AlistairCheeseman/SmartHome-Project/Hardware/Device Pictures/DSC_0228.JPG

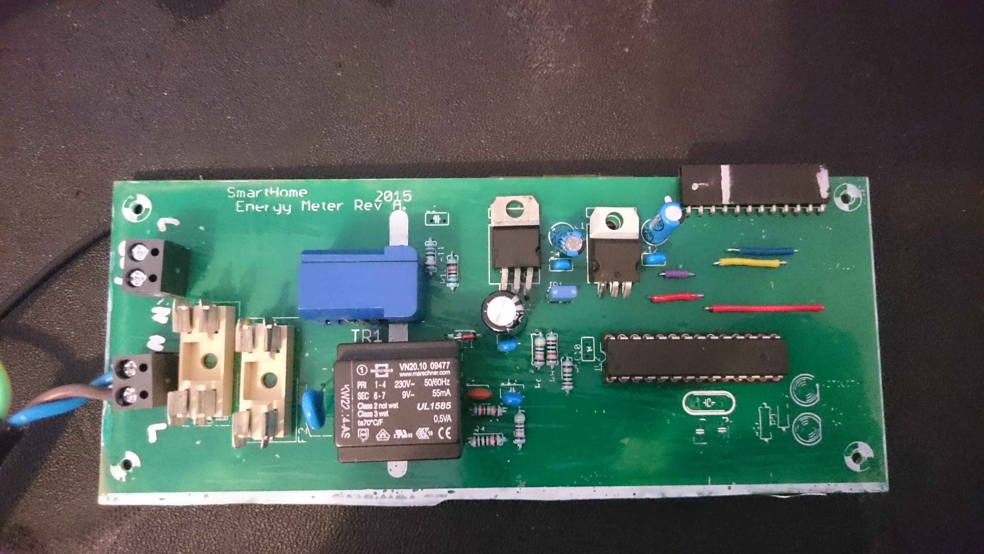
Hardware/Device Pictures/DSC_0228.JPG
