AlistairCheeseman/SmartHome-Project/Hardware/Device Pictures/DSCF8857.JPG

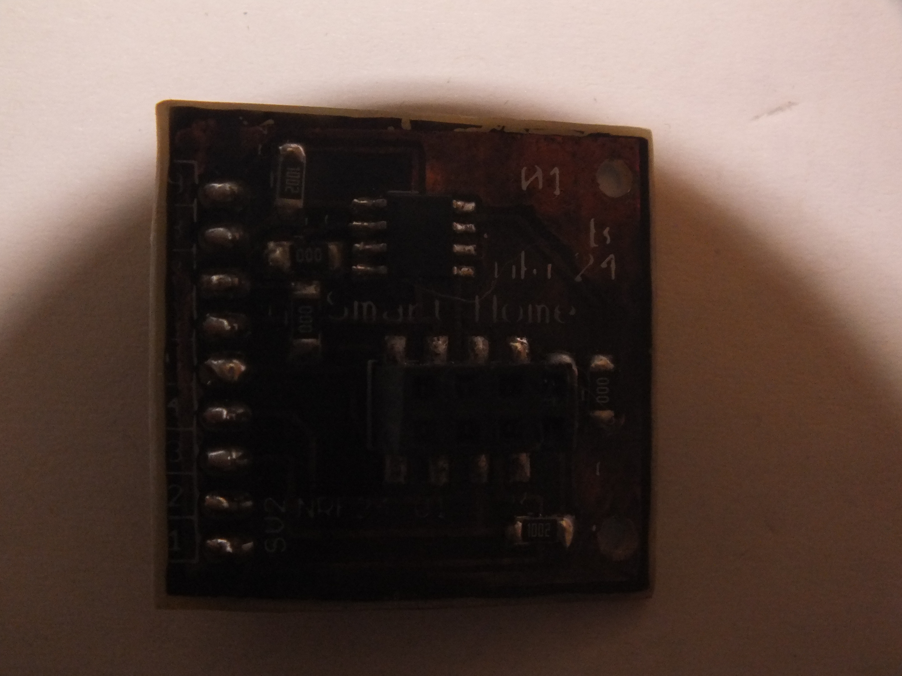
Hardware/Device Pictures/DSCF8857.JPG
