AlistairCheeseman/SmartHome-Project/Hardware/Device Pictures/DSCF8858.JPG

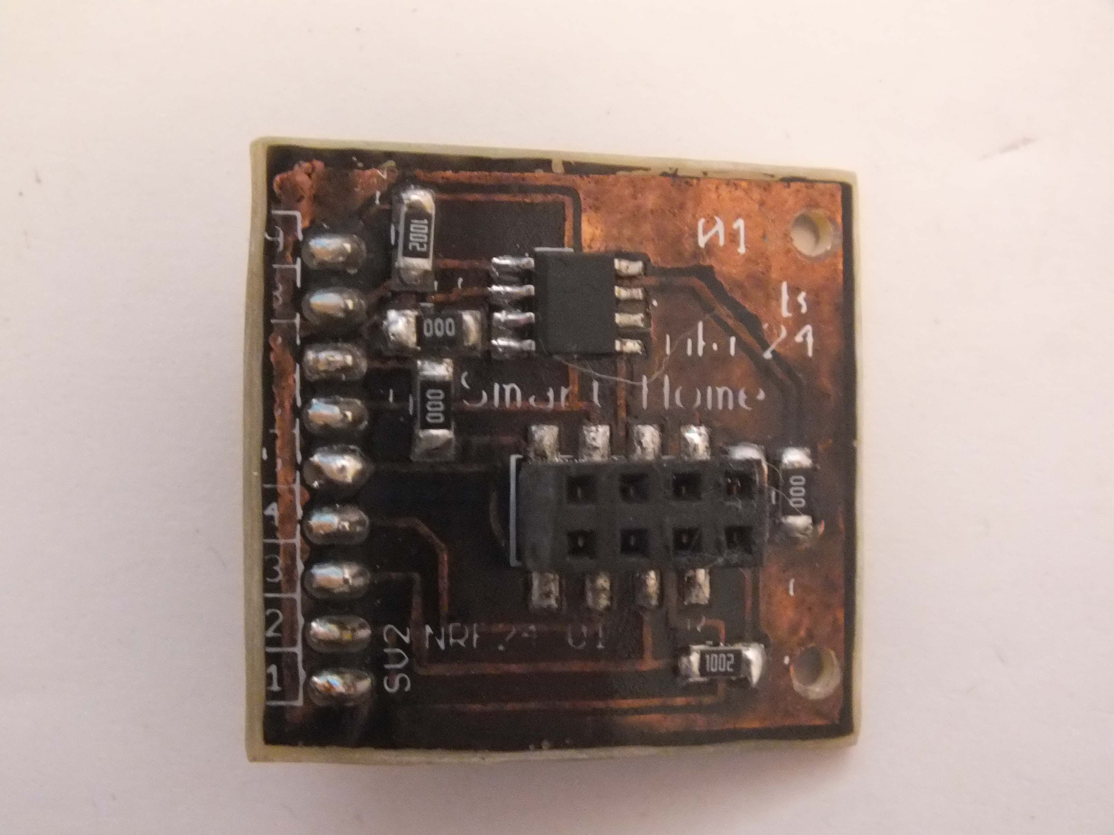
Hardware/Device Pictures/DSCF8858.JPG
