AlistairCheeseman/SmartHome-Project/Hardware/Device Pictures/DSCF8859.JPG

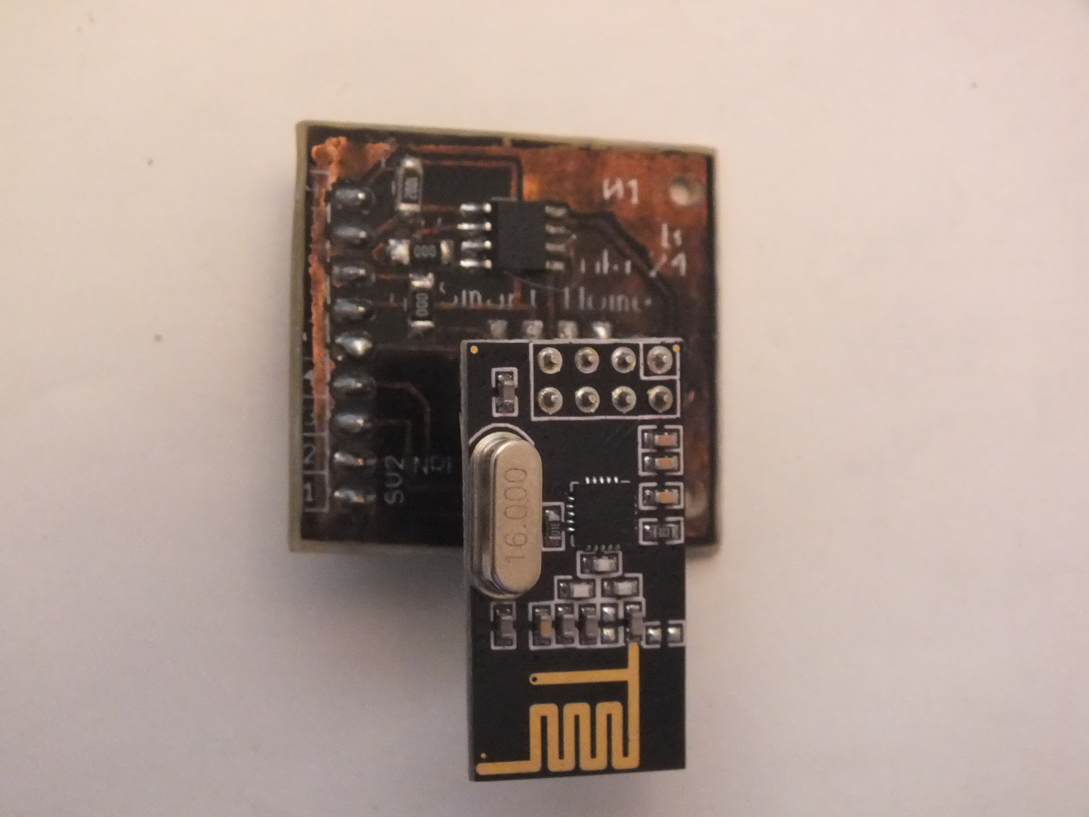
Hardware/Device Pictures/DSCF8859.JPG
