AlistairCheeseman/SmartHome-Project/Hardware/Device Pictures/DSCF8860.JPG

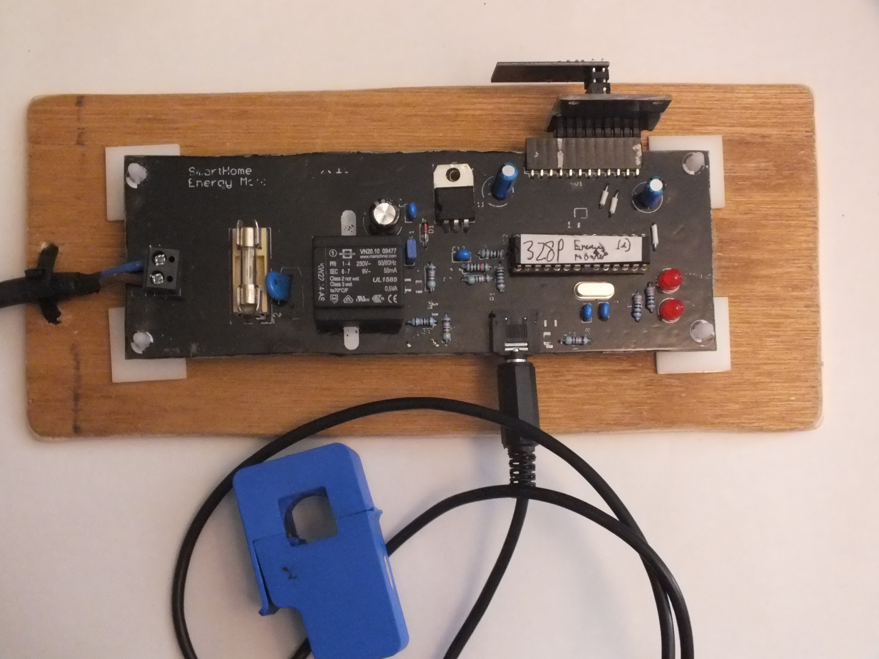
Hardware/Device Pictures/DSCF8860.JPG
