AlistairCheeseman/SmartHome-Project/Hardware/Device Pictures/DSCF8861.JPG

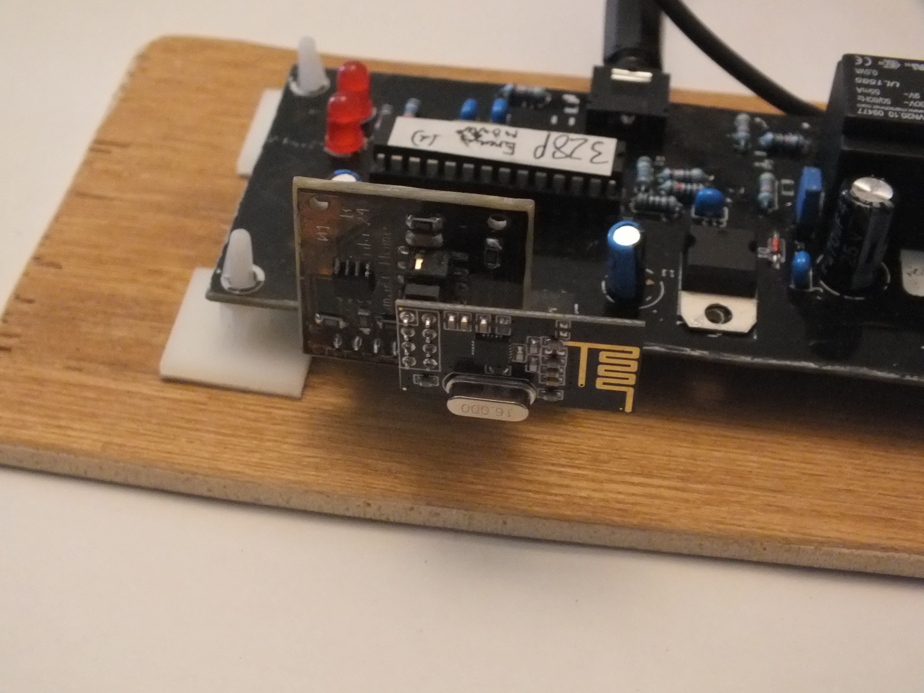
Hardware/Device Pictures/DSCF8861.JPG
