AlistairCheeseman/SmartHome-Project/Hardware/Device Pictures/DSCF8862.JPG

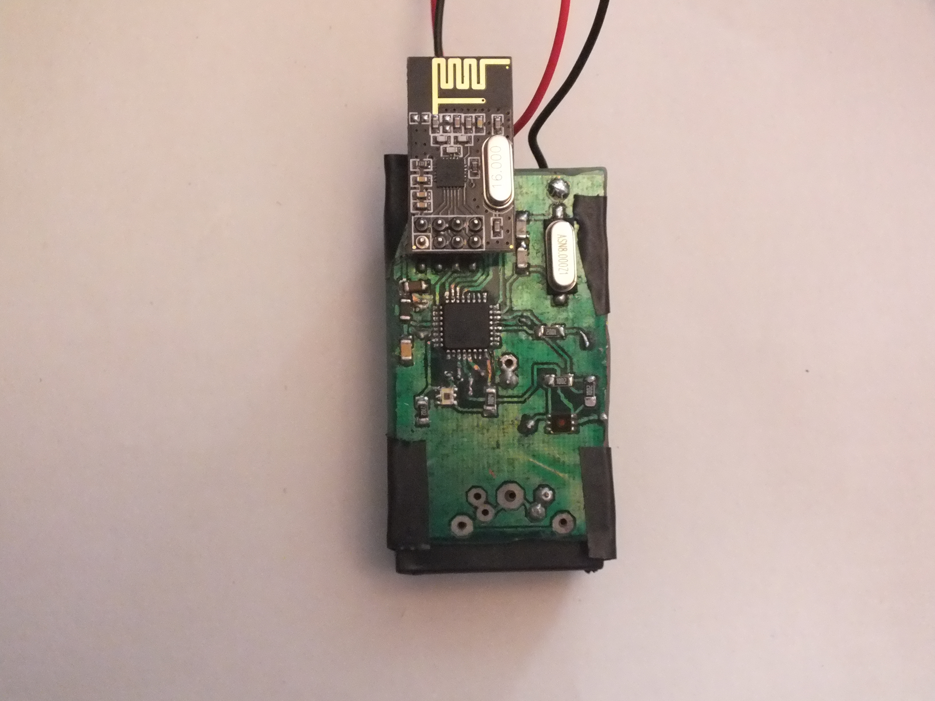
Hardware/Device Pictures/DSCF8862.JPG
