AlistairCheeseman/SmartHome-Project/Hardware/Device Pictures/DSCF8863.JPG

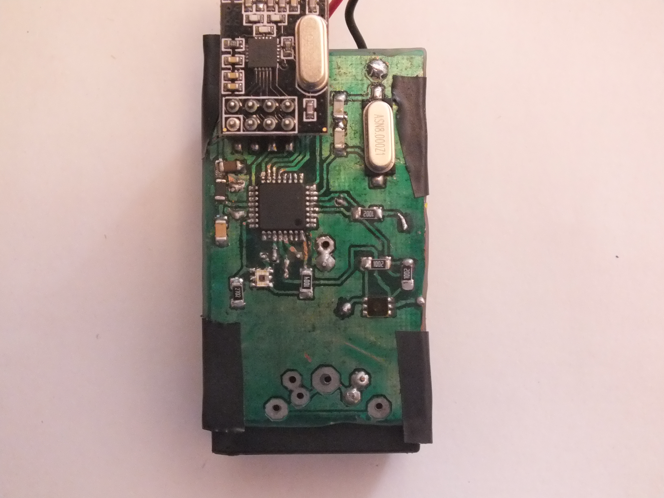
Hardware/Device Pictures/DSCF8863.JPG
