AlistairCheeseman/SmartHome-Project/Hardware/Device Pictures/DSCF8865.JPG

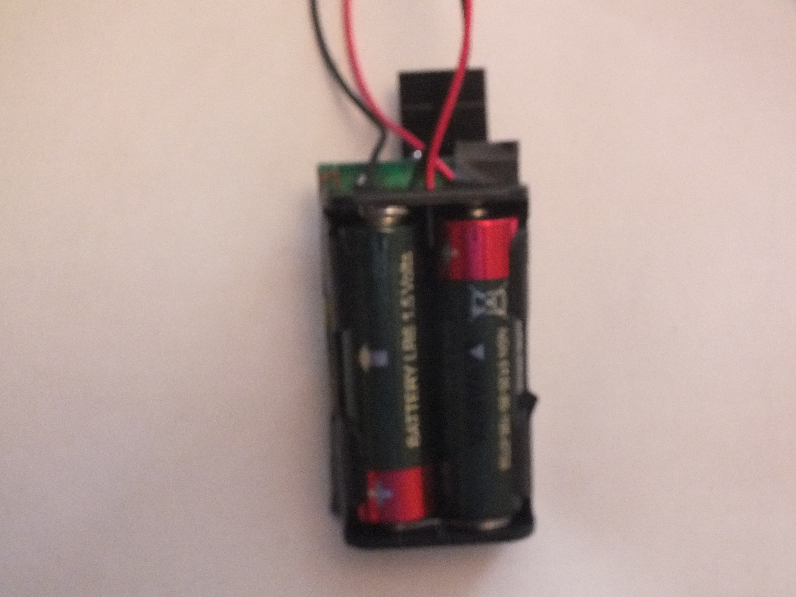
Hardware/Device Pictures/DSCF8865.JPG
