AlistairCheeseman/SmartHome-Project/Hardware/Device Pictures/DSCF8866.JPG

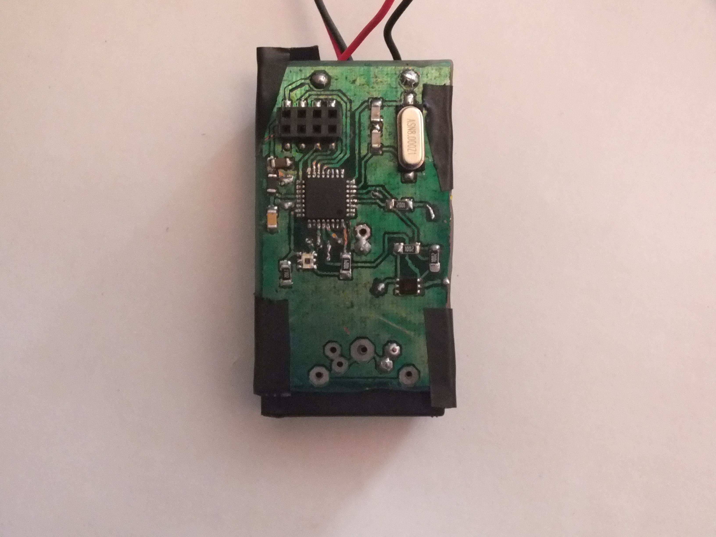
Hardware/Device Pictures/DSCF8866.JPG
