AlistairCheeseman/SmartHome-Project/Hardware/Device Pictures/DSCF8867.JPG

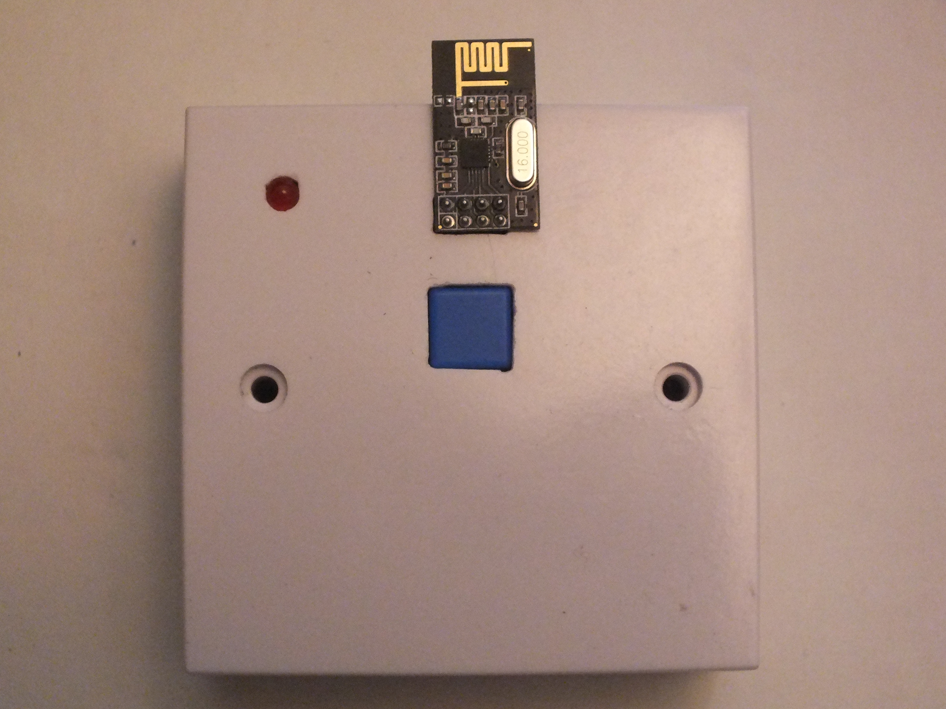
Hardware/Device Pictures/DSCF8867.JPG
