AlistairCheeseman/SmartHome-Project/Hardware/Device Pictures/DSCF8868.JPG

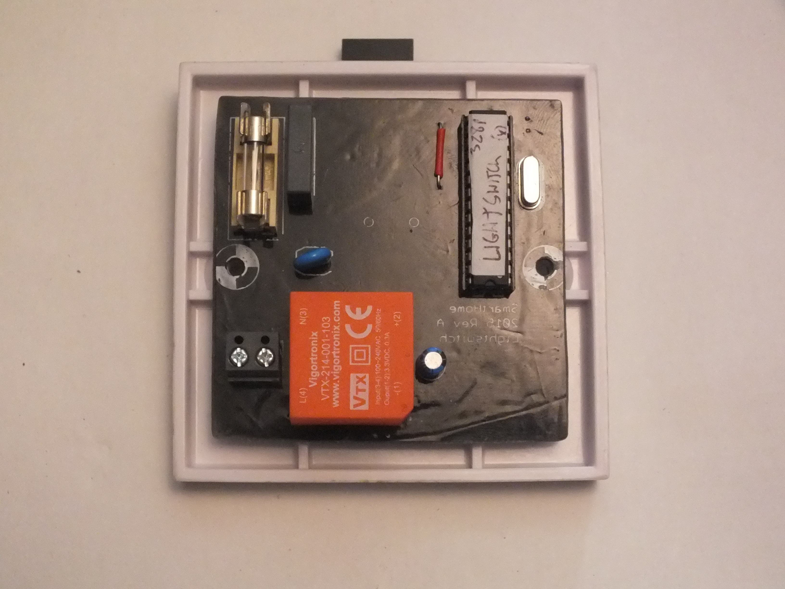
Hardware/Device Pictures/DSCF8868.JPG
