AlistairCheeseman/SmartHome-Project/Hardware/Device Pictures/DSCF8869.JPG

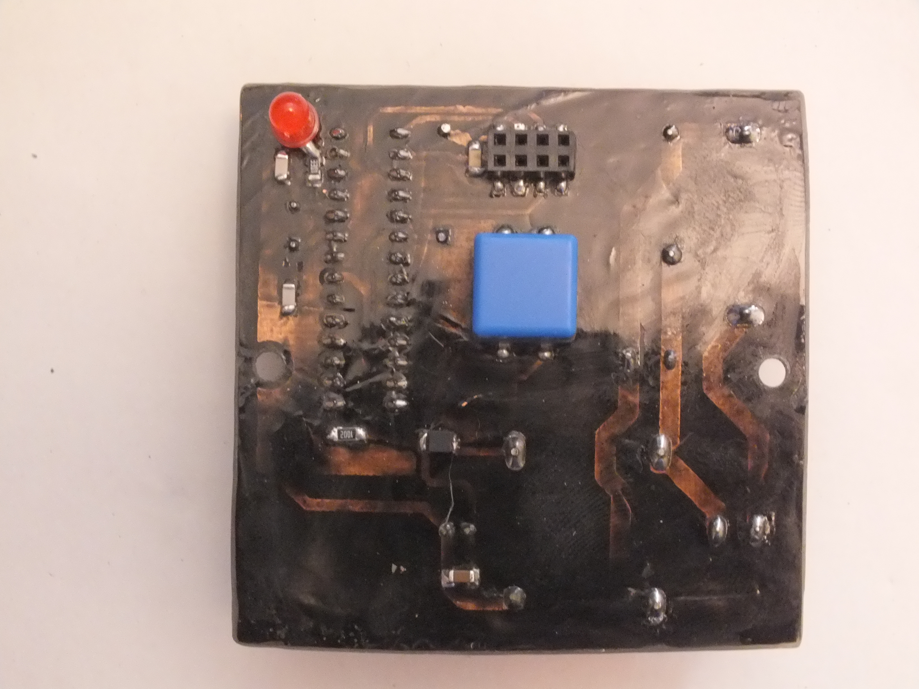
Hardware/Device Pictures/DSCF8869.JPG
