AlistairCheeseman/SmartHome-Project/Hardware/Device Pictures/DSCF8870.JPG

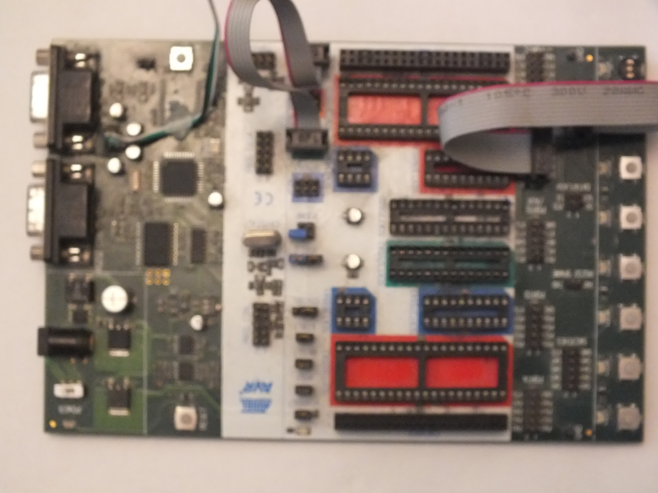
Hardware/Device Pictures/DSCF8870.JPG
