AlistairCheeseman/SmartHome-Project/Hardware/Device Pictures/DSCF8872.JPG

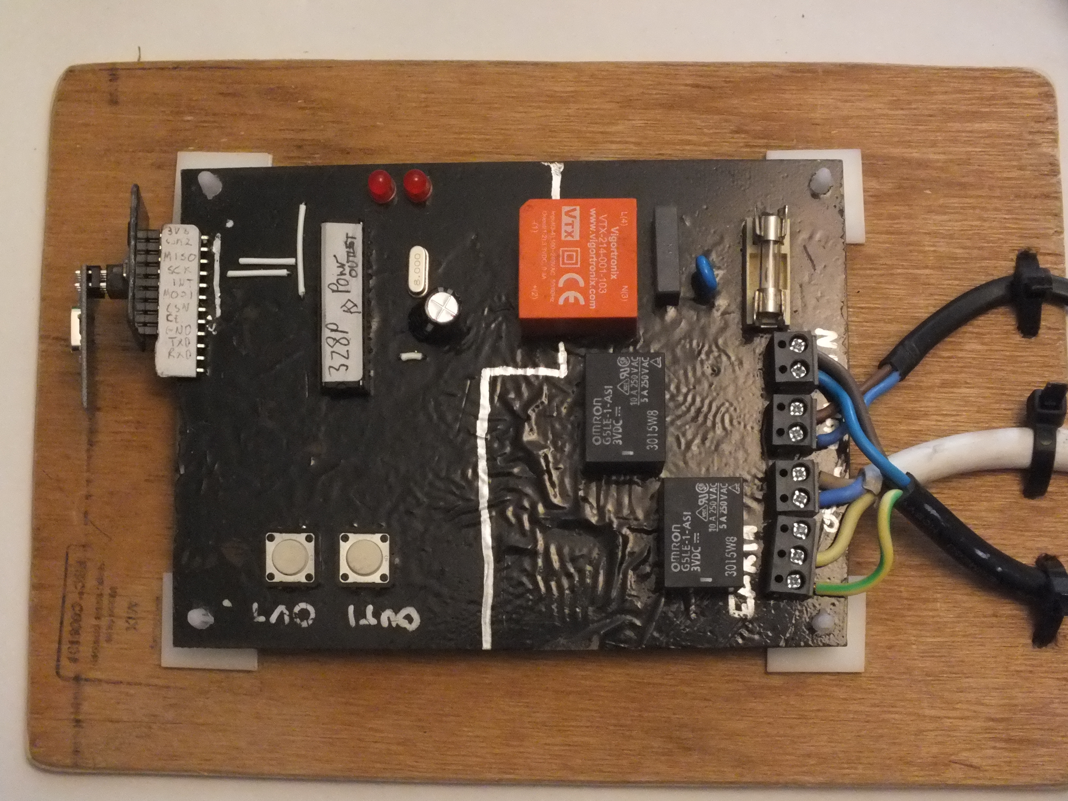
Hardware/Device Pictures/DSCF8872.JPG
