AlistairCheeseman/SmartHome-Project/Hardware/Device Pictures/DSCF8873.JPG

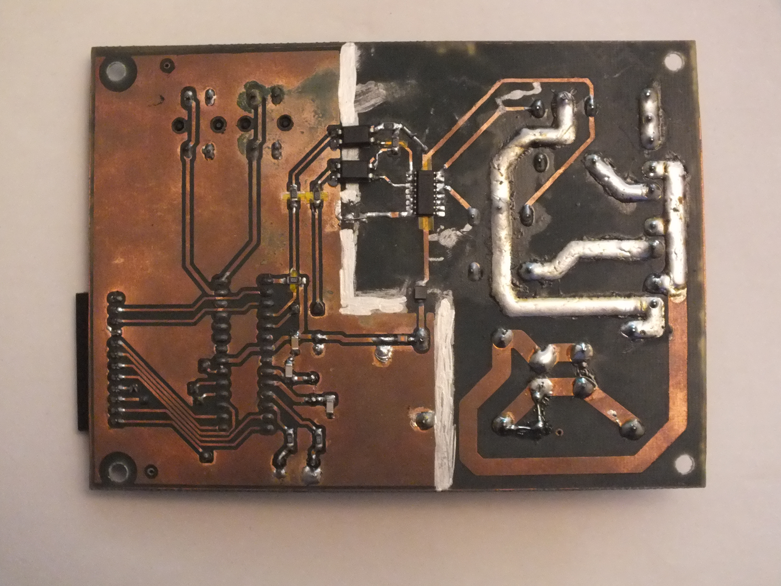
Hardware/Device Pictures/DSCF8873.JPG
