AlistairCheeseman/SmartHome-Project/Hardware/Device Pictures/DSCF8874.JPG

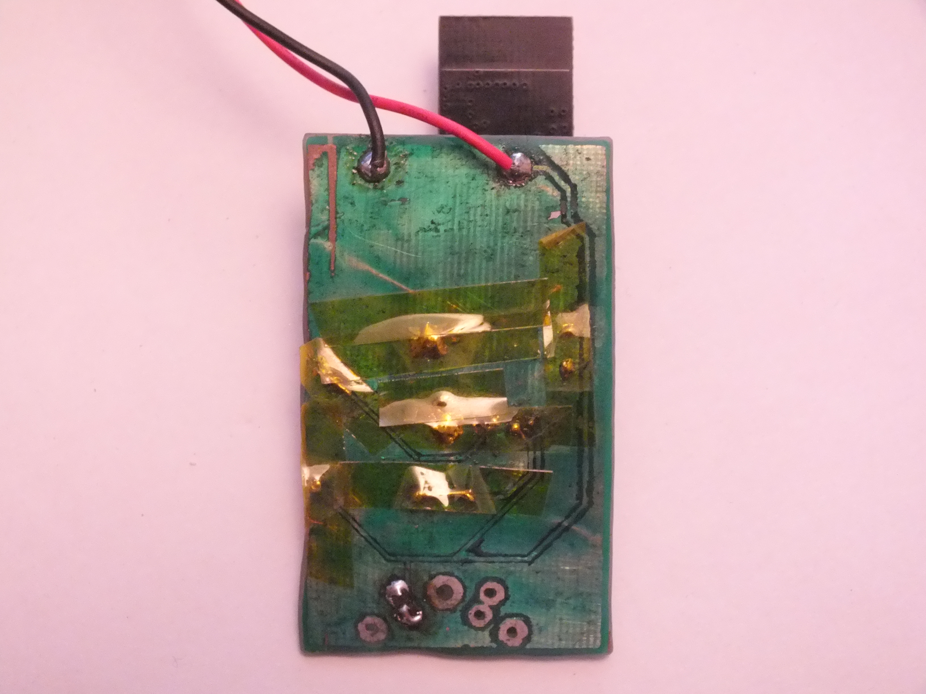
Hardware/Device Pictures/DSCF8874.JPG
