AlistairCheeseman/SmartHome-Project/Hardware/Device Pictures/DSCF8875.JPG

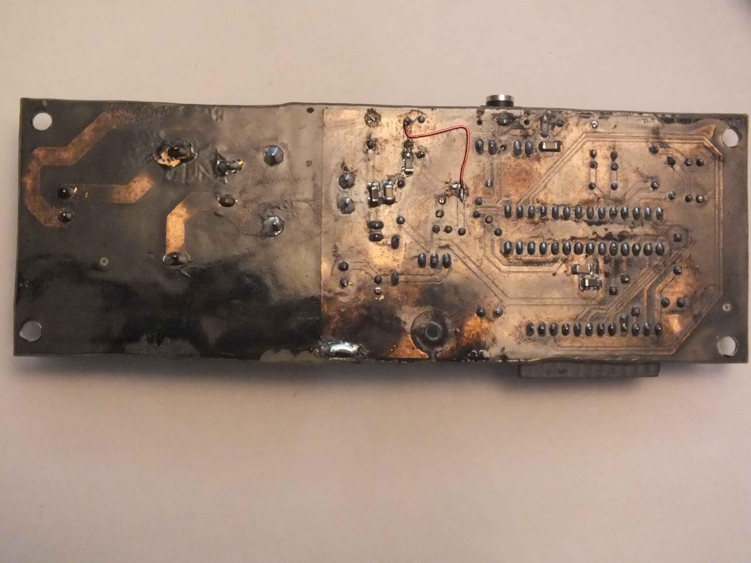
Hardware/Device Pictures/DSCF8875.JPG
