AlistairCheeseman/SmartHome-Project/Hardware/Device Pictures/DSCF8876.JPG

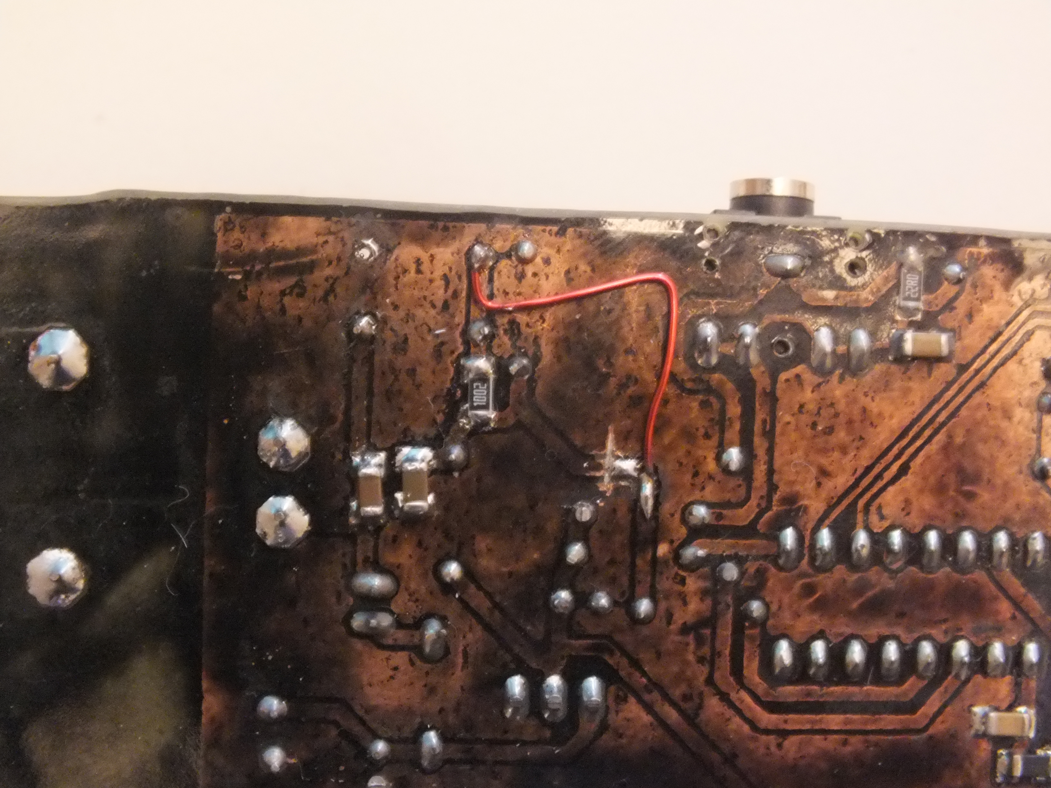
Hardware/Device Pictures/DSCF8876.JPG
