AlistairCheeseman/SmartHome-Project/Hardware/Device Pictures/DSCF8877.JPG

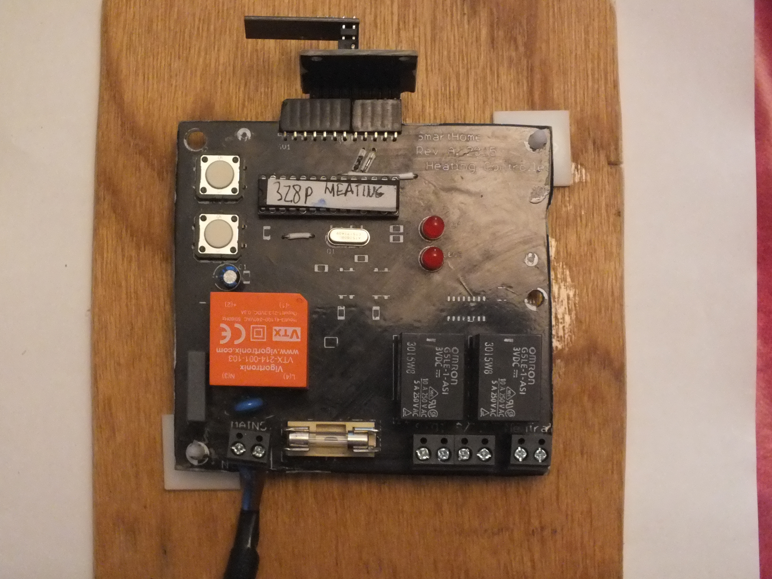
Hardware/Device Pictures/DSCF8877.JPG
