AlistairCheeseman/SmartHome-Project/Hardware/Device Pictures/DSCF8878.JPG

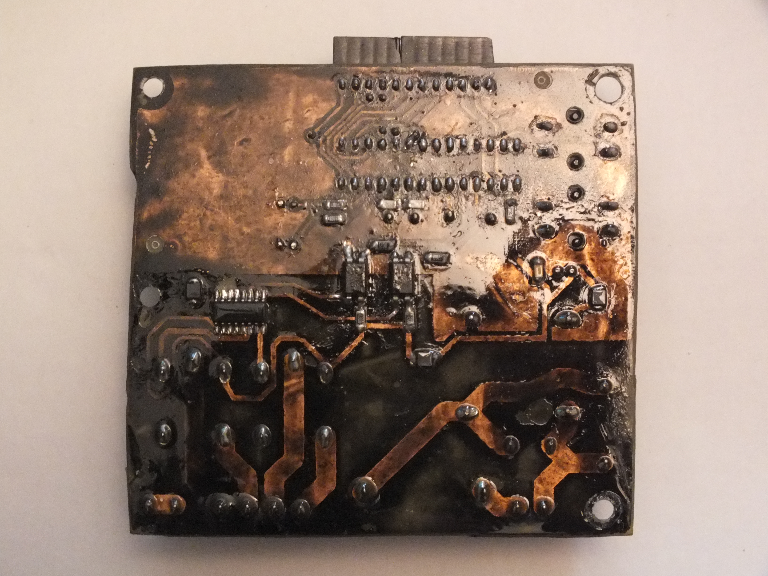
Hardware/Device Pictures/DSCF8878.JPG
