AlistairCheeseman/SmartHome-Project/Hardware/Device Pictures/DSCF8879.JPG

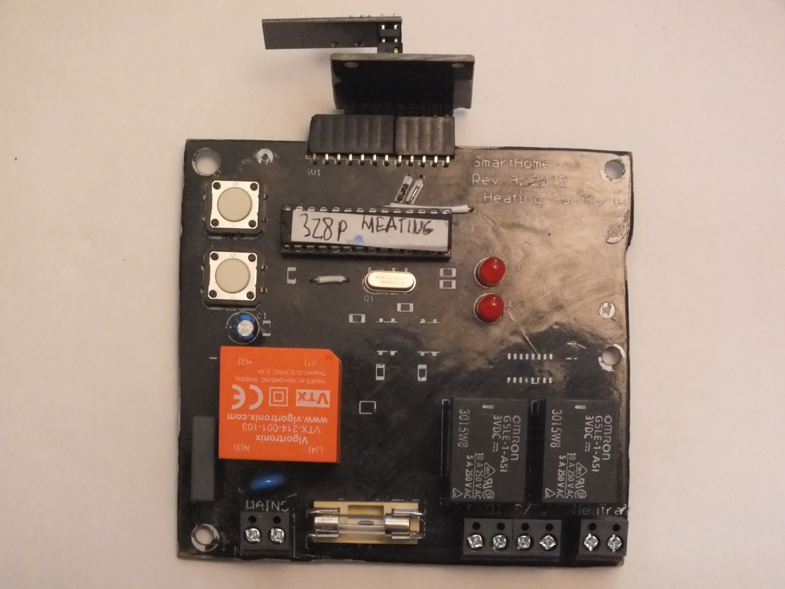
Hardware/Device Pictures/DSCF8879.JPG
