AlistairCheeseman/SmartHome-Project/Hardware/Device Pictures/DSCF8880.JPG

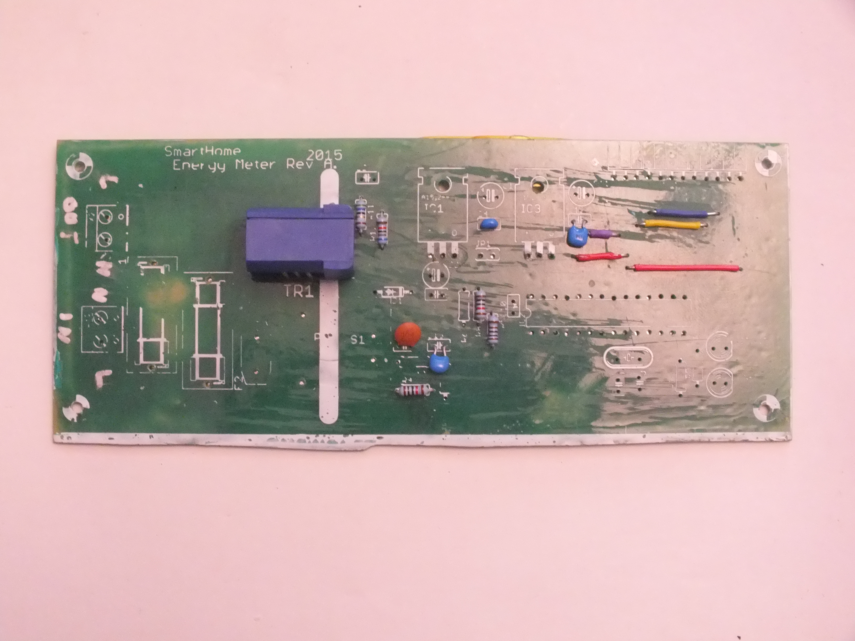
Hardware/Device Pictures/DSCF8880.JPG
