AlistairCheeseman/SmartHome-Project/Hardware/Device Pictures/DSCF8881.JPG

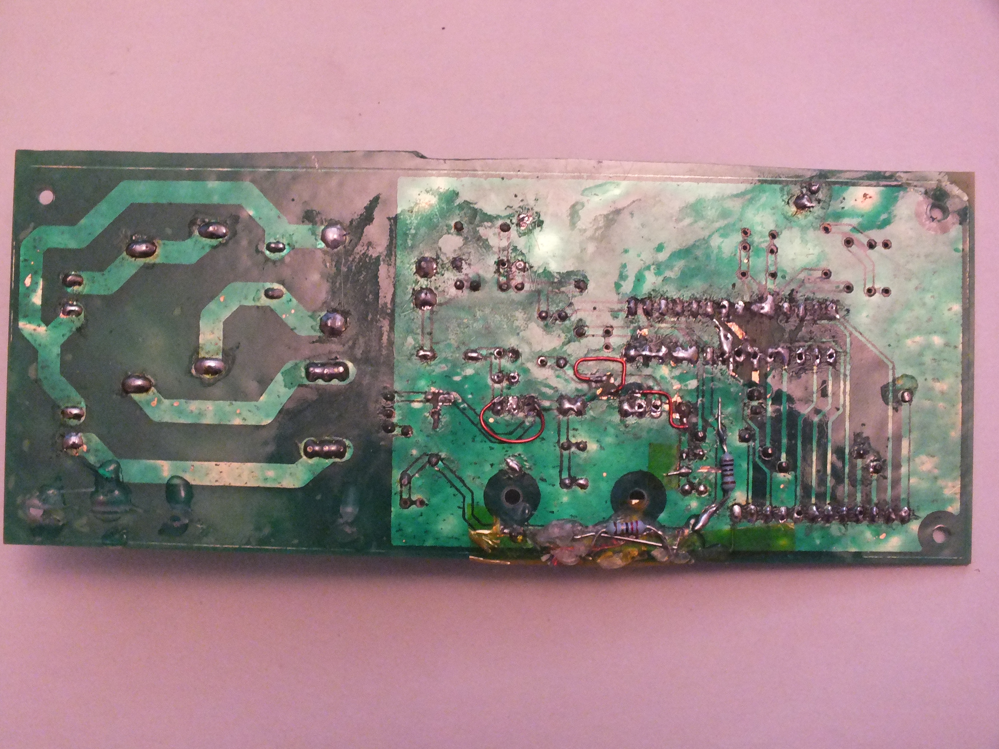
Hardware/Device Pictures/DSCF8881.JPG
