AlistairCheeseman/SmartHome-Project/Hardware/Device Pictures/DSCF8882.JPG

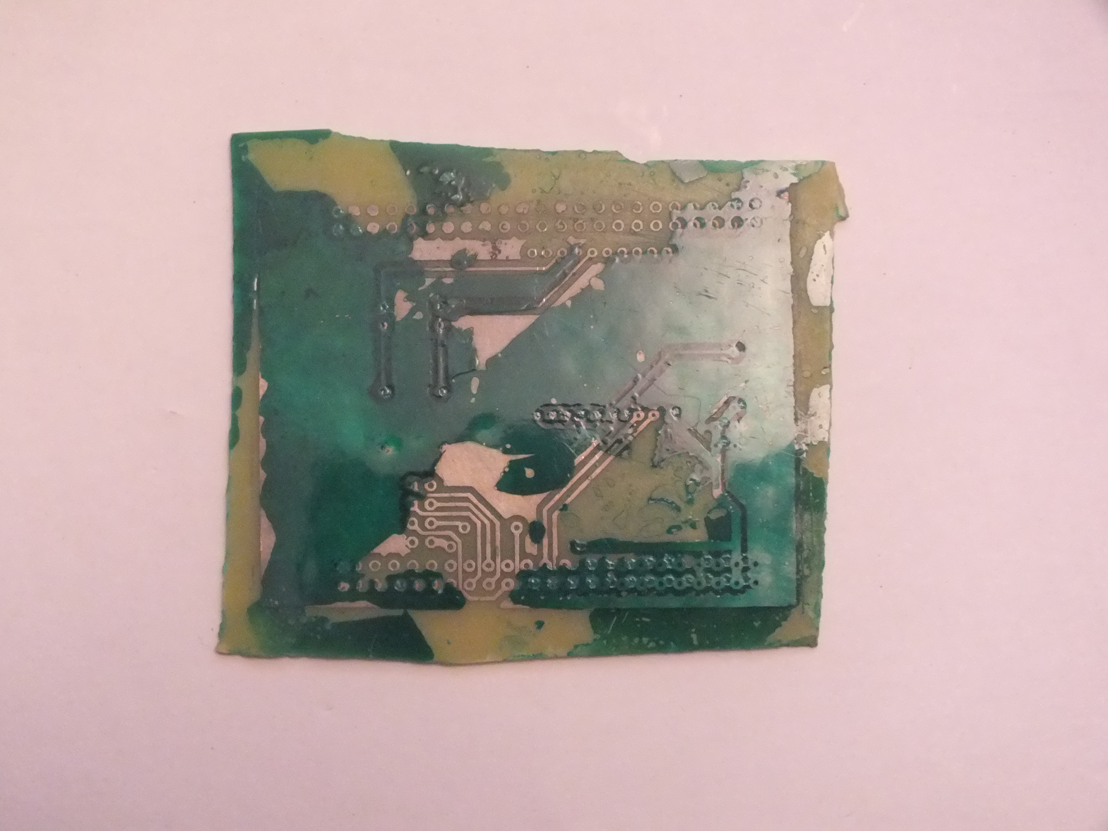
Hardware/Device Pictures/DSCF8882.JPG
