AlistairCheeseman/SmartHome-Project/Hardware/Device Pictures/DSCF8883.JPG

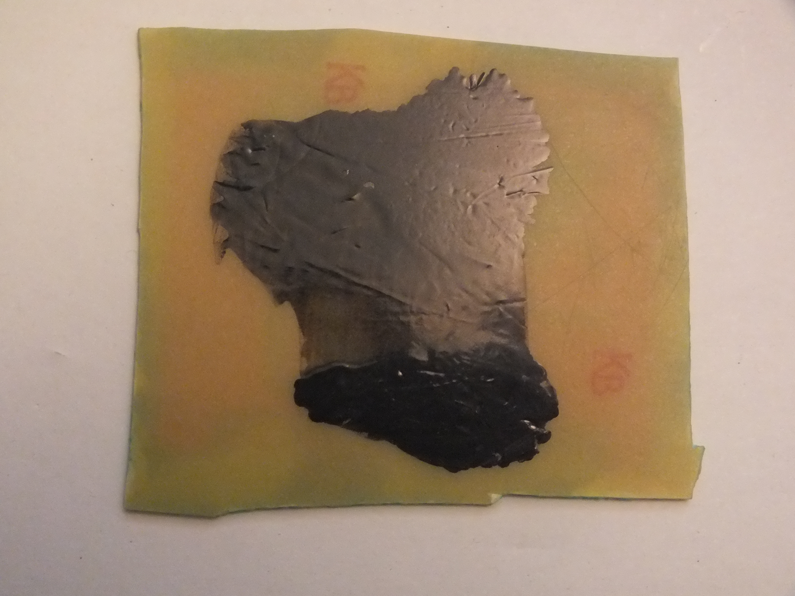
Hardware/Device Pictures/DSCF8883.JPG
