AlistairCheeseman/SmartHome-Project/Hardware/Device Pictures/DSCF8884.JPG

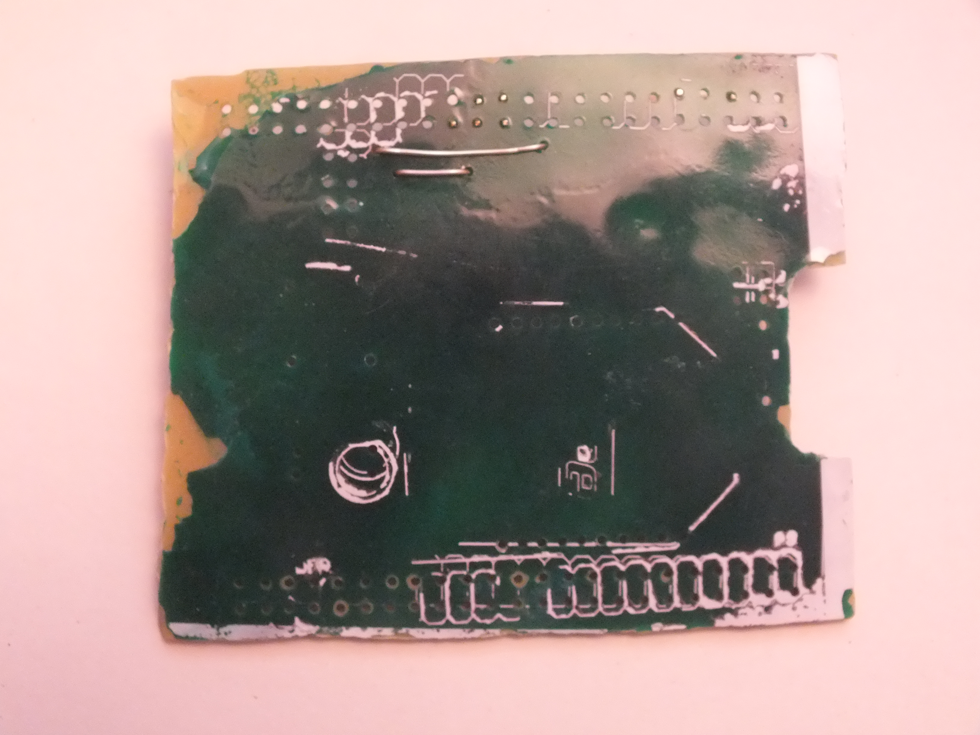
Hardware/Device Pictures/DSCF8884.JPG
