AlistairCheeseman/SmartHome-Project/Hardware/Device Pictures/DSCF8885.JPG

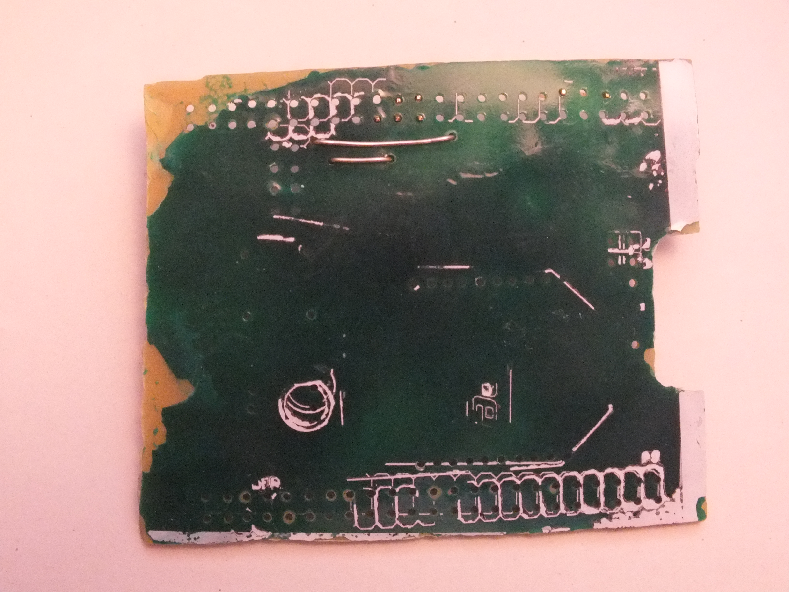
Hardware/Device Pictures/DSCF8885.JPG
