AlistairCheeseman/SmartHome-Project/Hardware/Device Pictures/DSCF8886.JPG

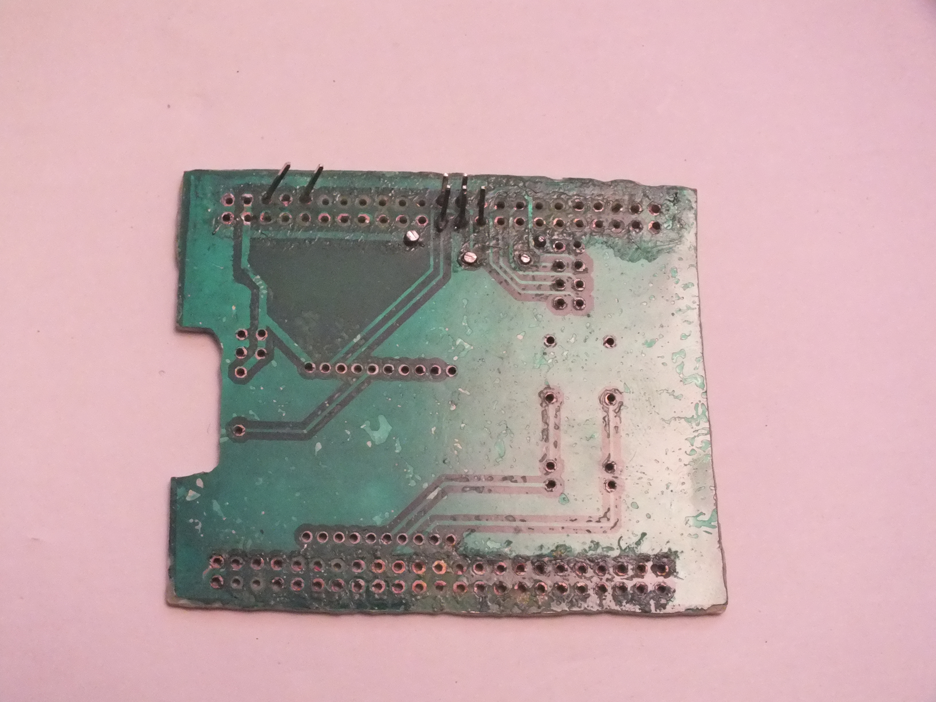
Hardware/Device Pictures/DSCF8886.JPG
