AlistairCheeseman/SmartHome-Project/Hardware/Device Pictures/DSCF8887.JPG

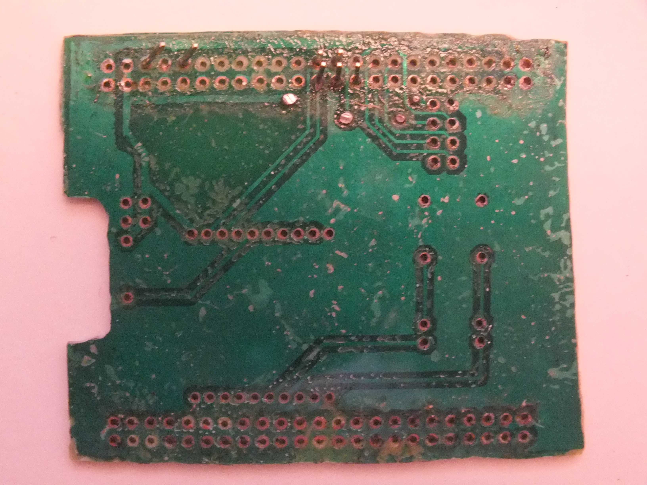
Hardware/Device Pictures/DSCF8887.JPG
