AlistairCheeseman/SmartHome-Project/Hardware/Device Pictures/DSCF8888.JPG

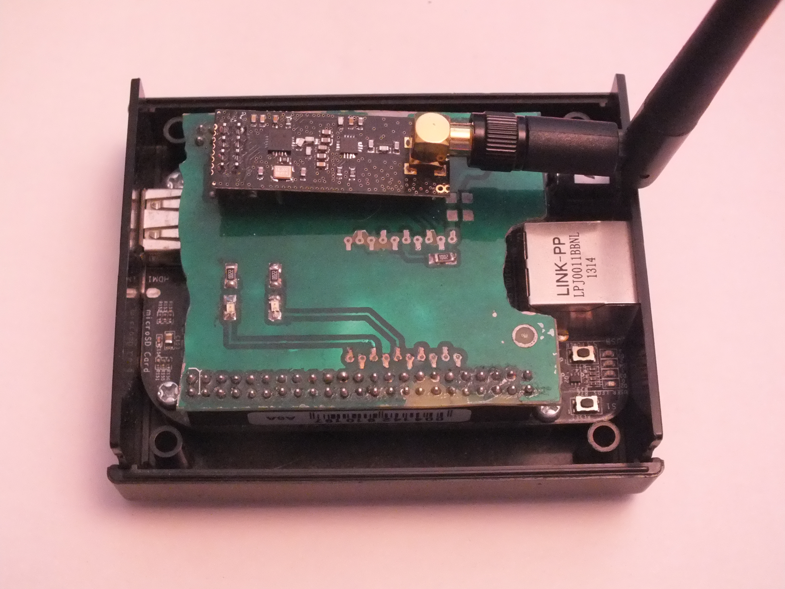
Hardware/Device Pictures/DSCF8888.JPG
