AlistairCheeseman/SmartHome-Project/Hardware/Device Pictures/DSCF8889.JPG

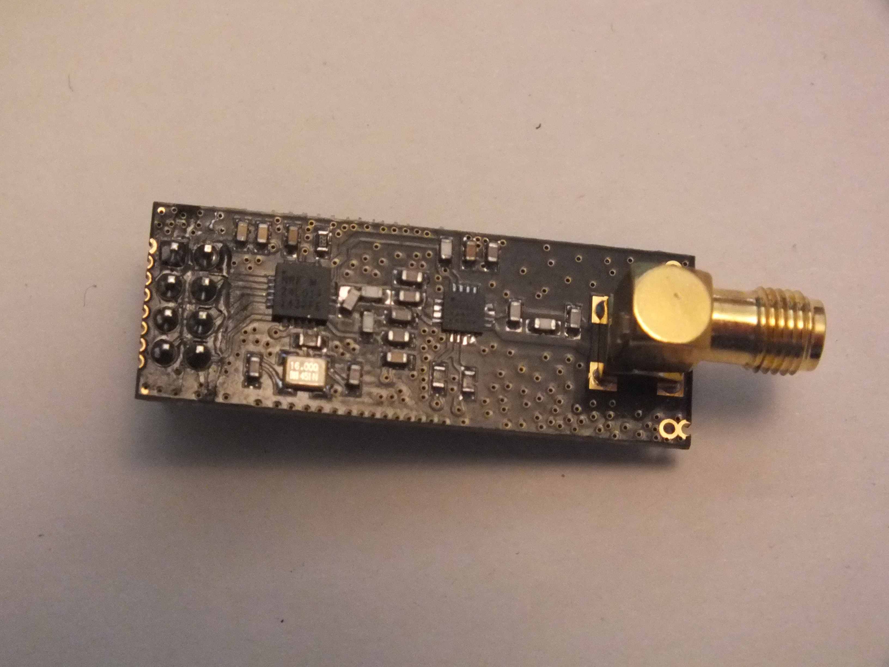
Hardware/Device Pictures/DSCF8889.JPG
