AlistairCheeseman/SmartHome-Project/Hardware/Device Pictures/DSCF8890.JPG

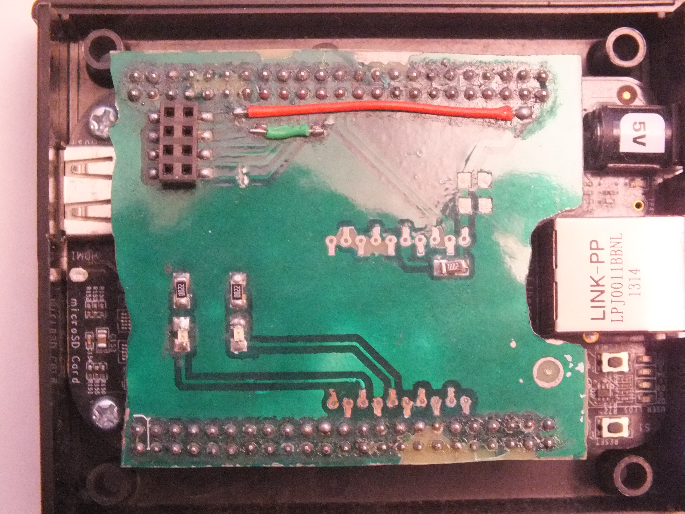
Hardware/Device Pictures/DSCF8890.JPG
