AlistairCheeseman/SmartHome-Project/Hardware/Device Pictures/DSCF8891.JPG

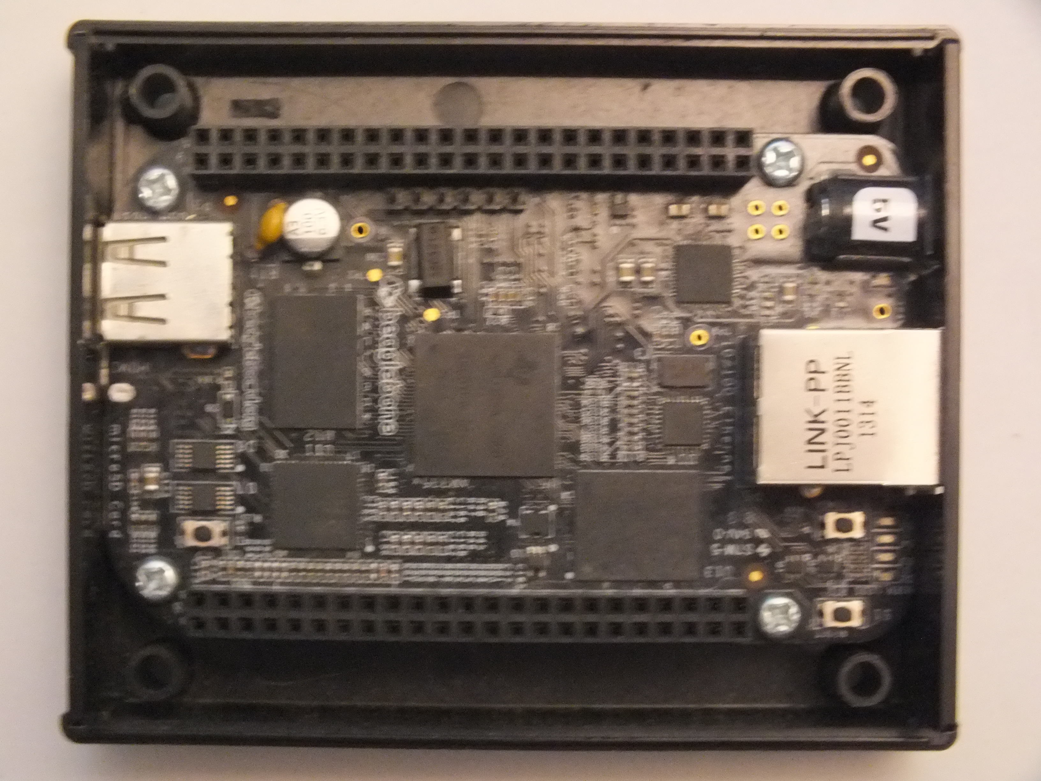
Hardware/Device Pictures/DSCF8891.JPG
