AlistairCheeseman/SmartHome-Project/Hardware/Device Pictures/DSCF8892.JPG

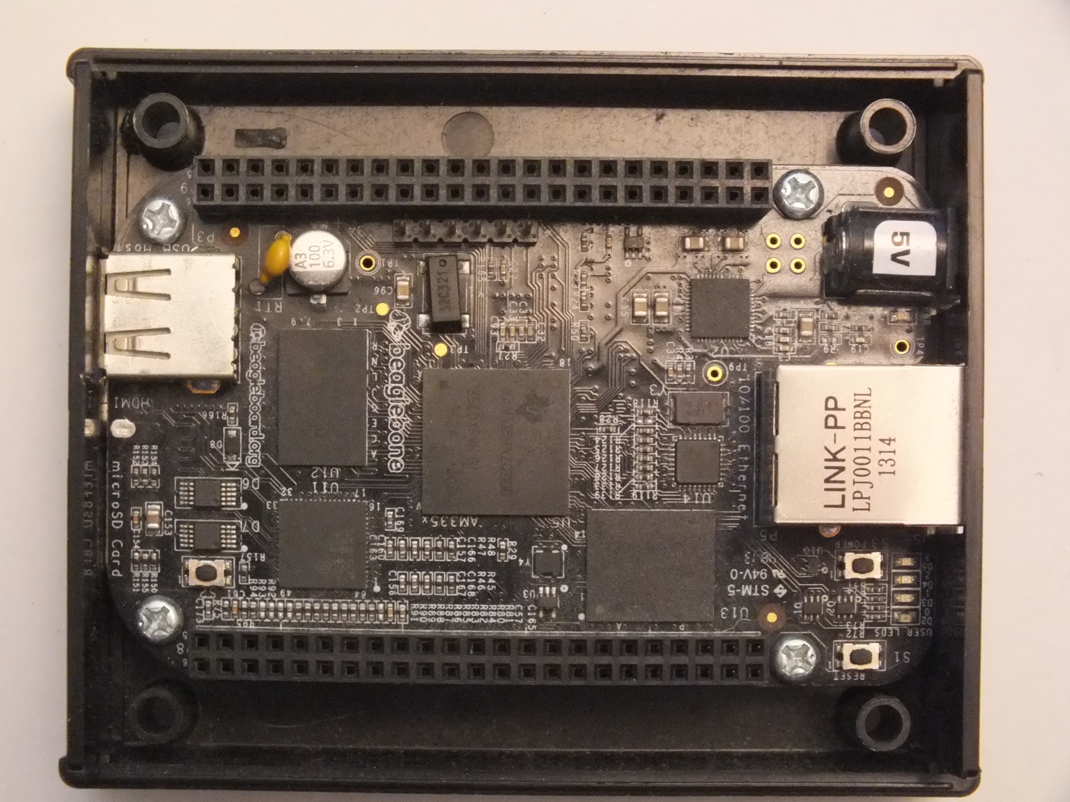
Hardware/Device Pictures/DSCF8892.JPG
