AlistairCheeseman/SmartHome-Project/Hardware/Device Pictures/DSCF8893.JPG

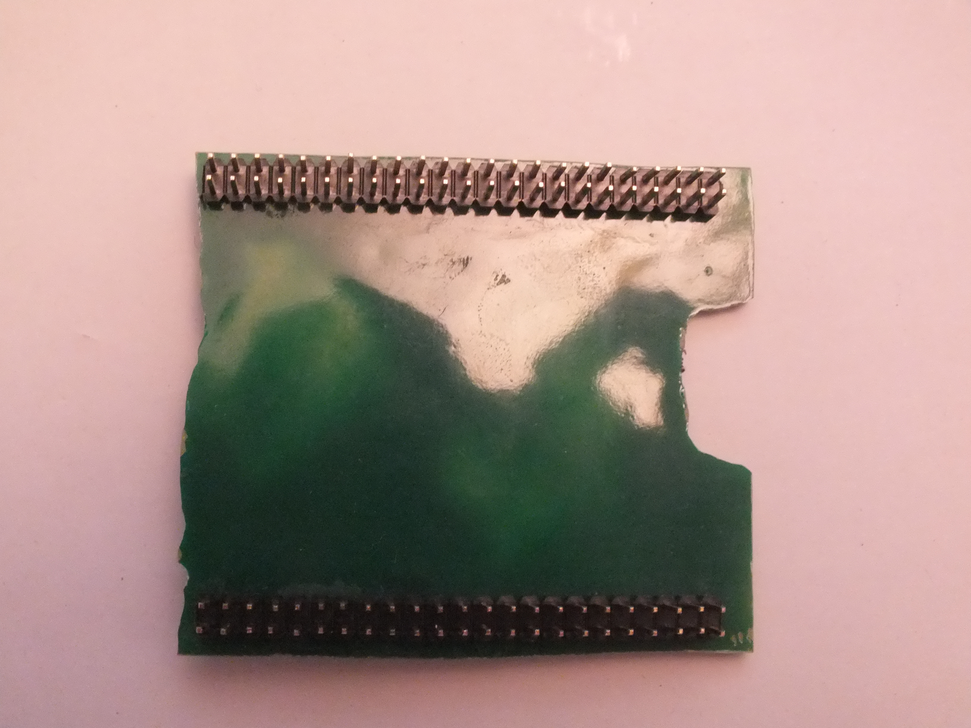
Hardware/Device Pictures/DSCF8893.JPG
