AlistairCheeseman/SmartHome-Project/Hardware/Device Pictures/DSCF8894.JPG

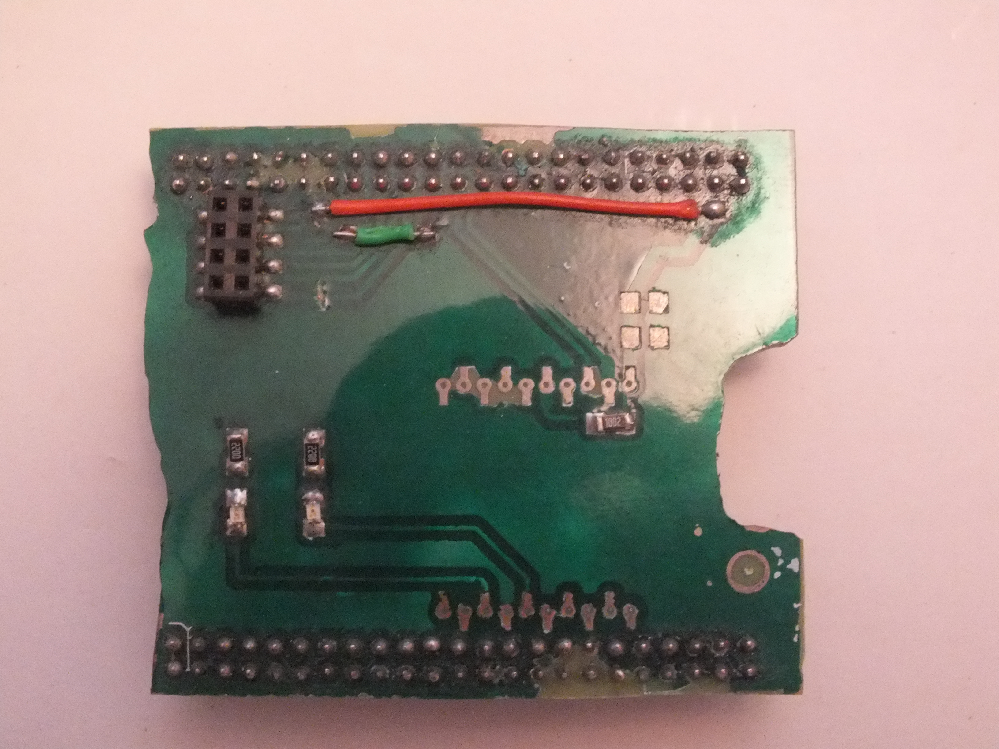
Hardware/Device Pictures/DSCF8894.JPG
