AlistairCheeseman/SmartHome-Project/Hardware/EnergySensor/Energy Sensor.JPG

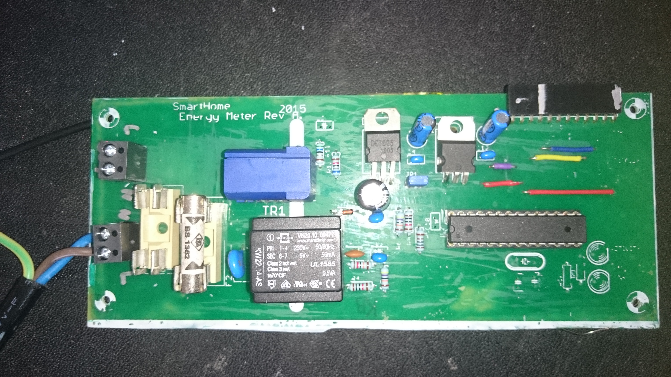
Hardware/EnergySensor/Energy Sensor.JPG
