AlistairCheeseman/SmartHome-Project/Hardware/Manufacturing Pictures/DSC_0122.JPG

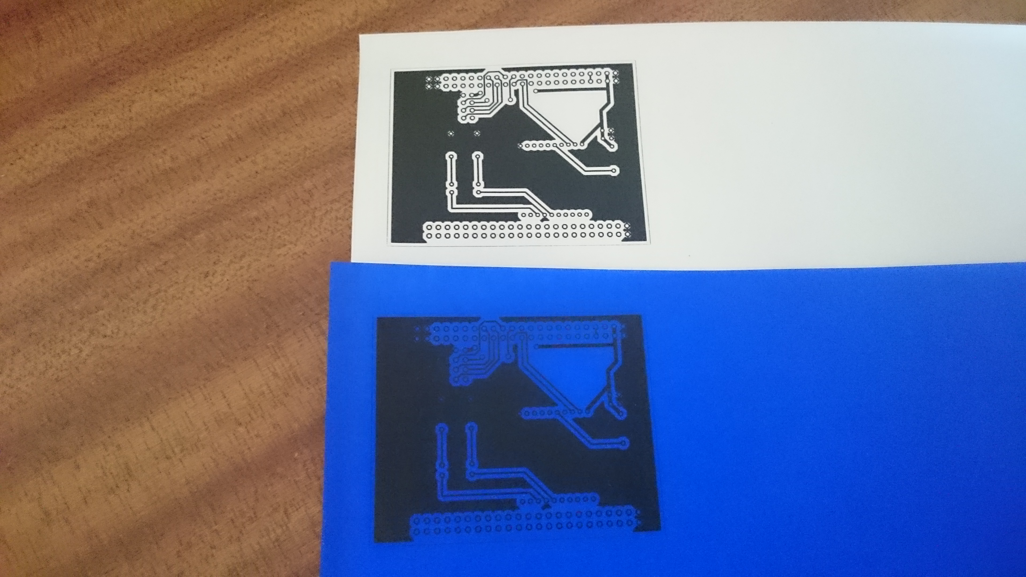
Hardware/Manufacturing Pictures/DSC_0122.JPG
