AlistairCheeseman/SmartHome-Project/Hardware/Manufacturing Pictures/DSC_0124.JPG

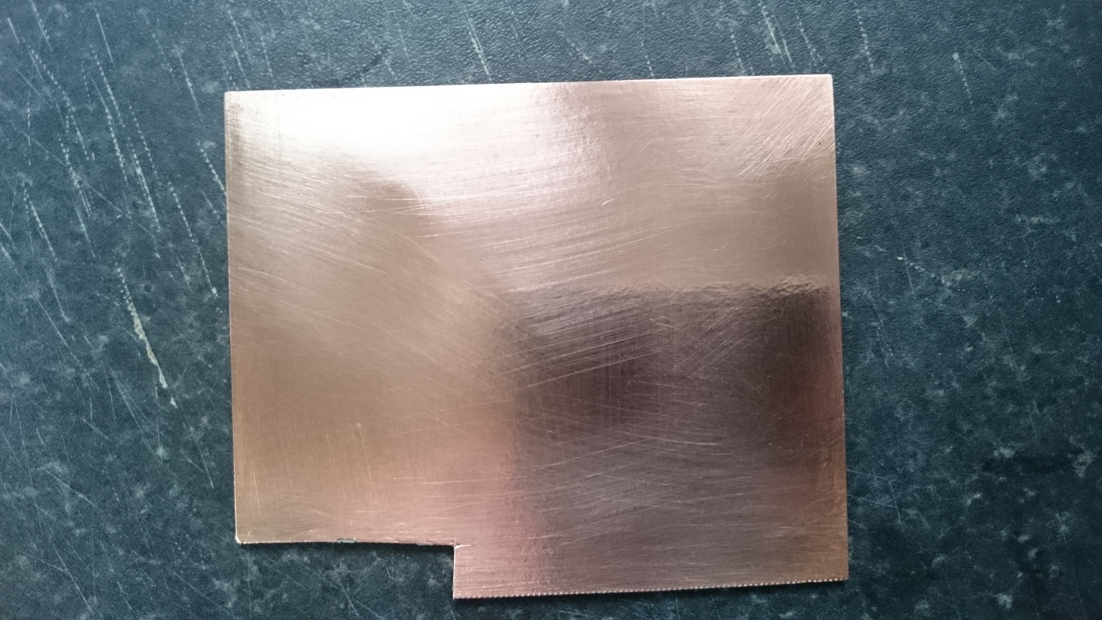
Hardware/Manufacturing Pictures/DSC_0124.JPG
