AlistairCheeseman/SmartHome-Project/Hardware/Manufacturing Pictures/DSC_0126.JPG

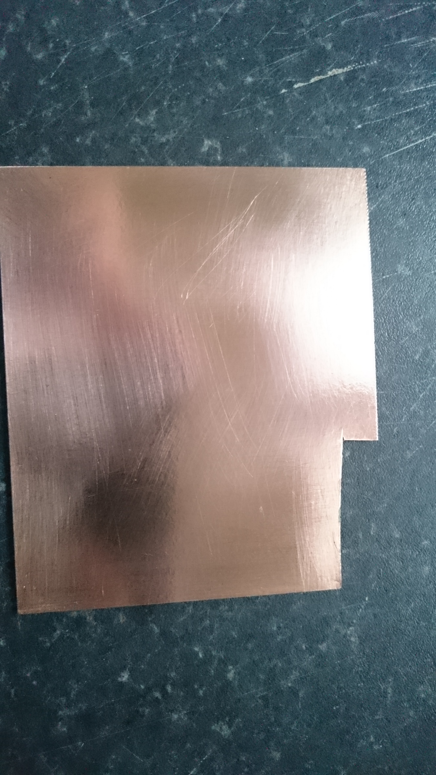
Hardware/Manufacturing Pictures/DSC_0126.JPG
