AlistairCheeseman/SmartHome-Project/Hardware/Manufacturing Pictures/DSC_0127.JPG

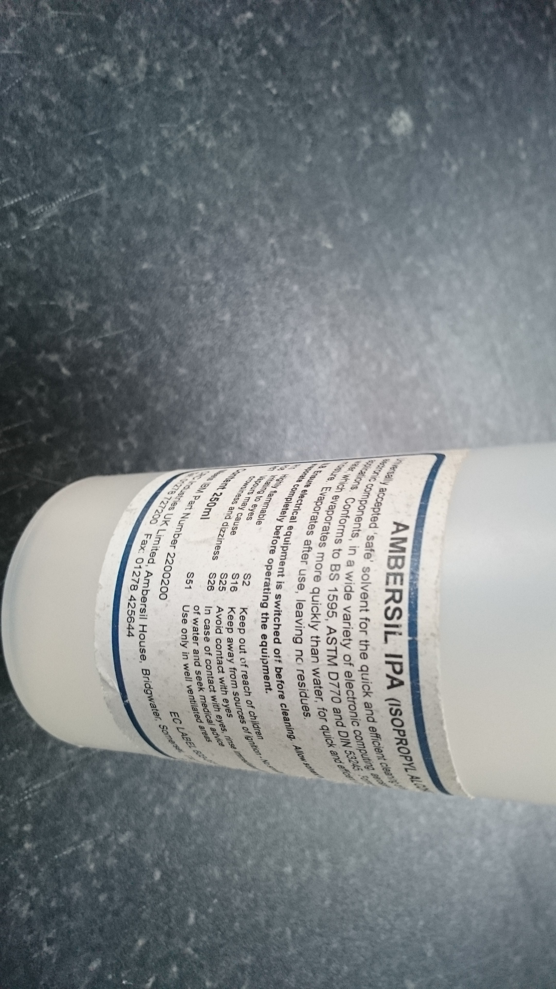
Hardware/Manufacturing Pictures/DSC_0127.JPG
