AlistairCheeseman/SmartHome-Project/Hardware/Manufacturing Pictures/DSC_0128.JPG

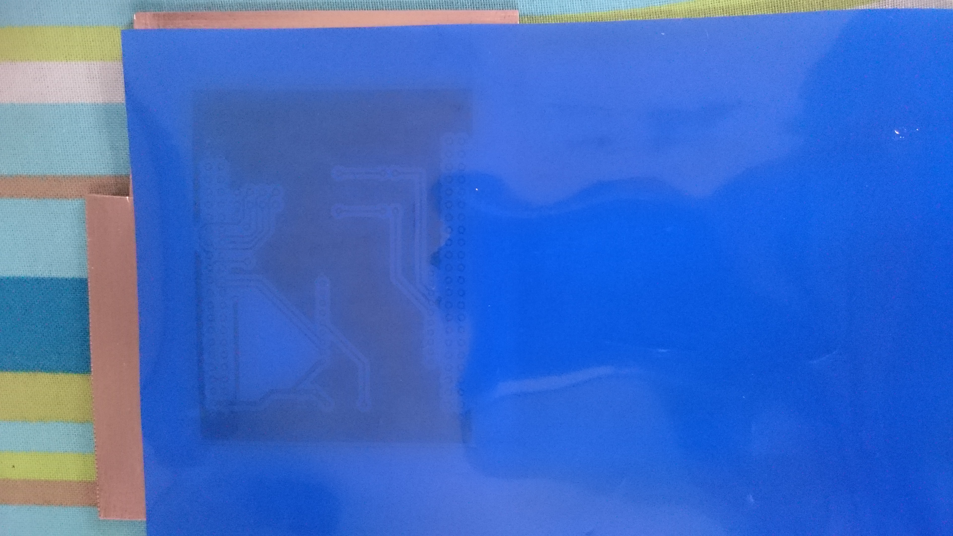
Hardware/Manufacturing Pictures/DSC_0128.JPG
