AlistairCheeseman/SmartHome-Project/Hardware/Manufacturing Pictures/DSC_0129.JPG

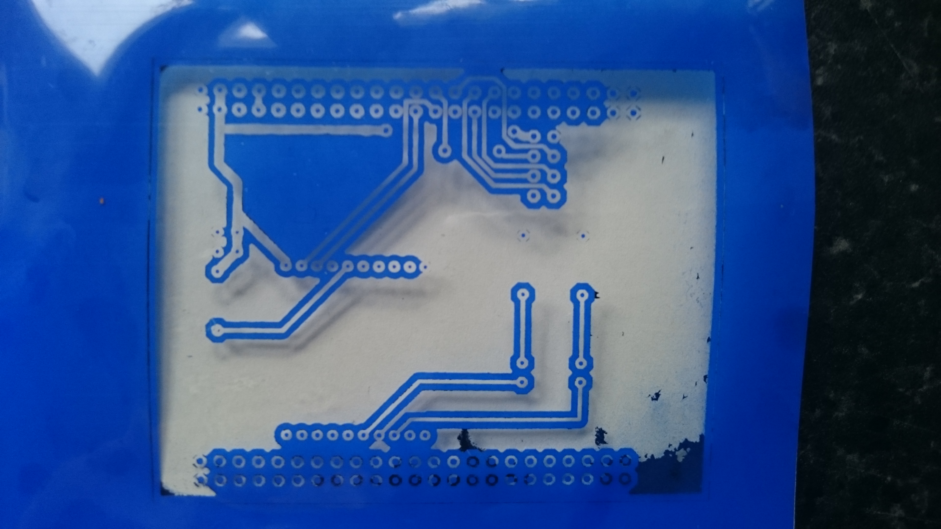
Hardware/Manufacturing Pictures/DSC_0129.JPG
