AlistairCheeseman/SmartHome-Project/Hardware/Manufacturing Pictures/DSC_0130.JPG

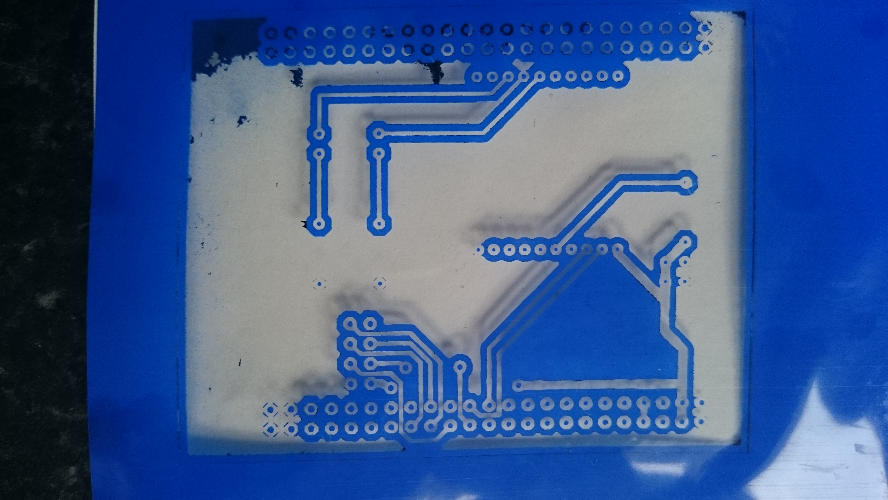
Hardware/Manufacturing Pictures/DSC_0130.JPG
