AlistairCheeseman/SmartHome-Project/Hardware/Manufacturing Pictures/DSC_0131.JPG

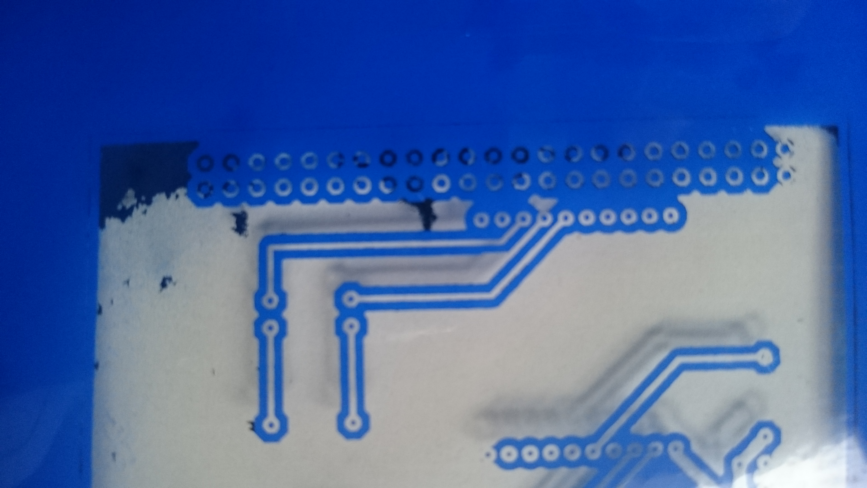
Hardware/Manufacturing Pictures/DSC_0131.JPG
