AlistairCheeseman/SmartHome-Project/Hardware/Manufacturing Pictures/DSC_0132.JPG

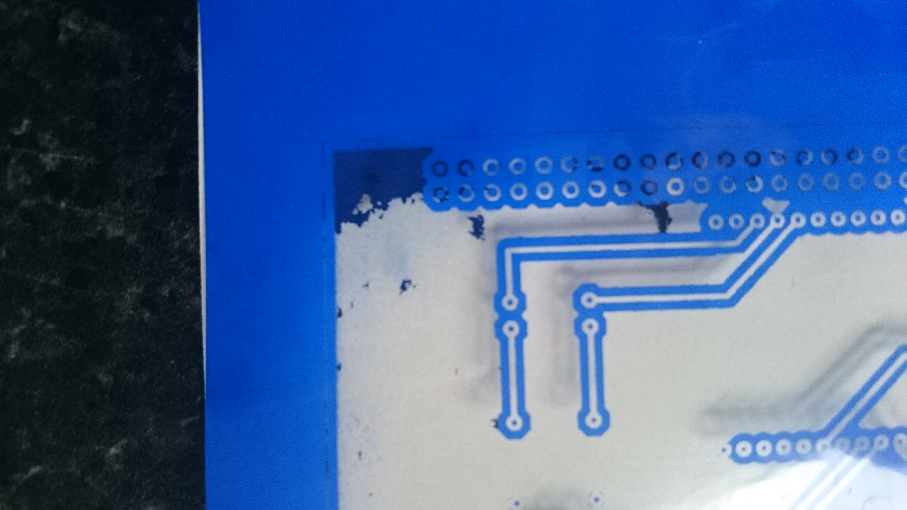
Hardware/Manufacturing Pictures/DSC_0132.JPG
