AlistairCheeseman/SmartHome-Project/Hardware/Manufacturing Pictures/DSC_0134.JPG

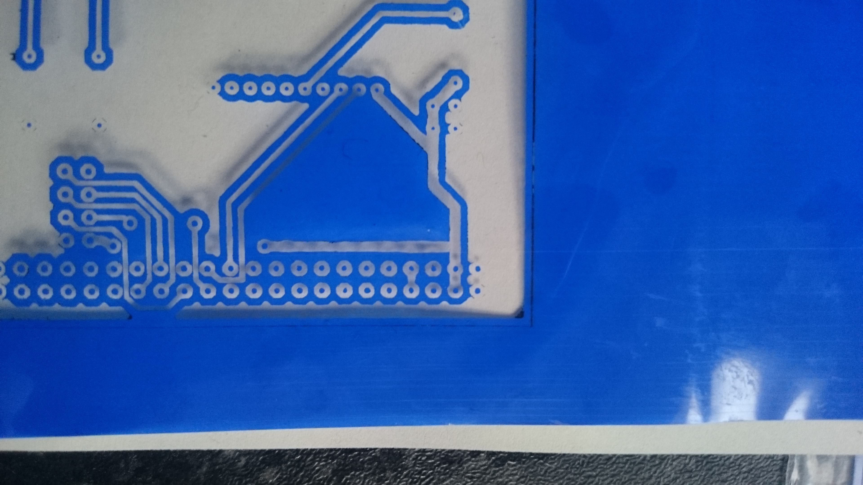
Hardware/Manufacturing Pictures/DSC_0134.JPG
