AlistairCheeseman/SmartHome-Project/Hardware/Manufacturing Pictures/DSC_0135.JPG

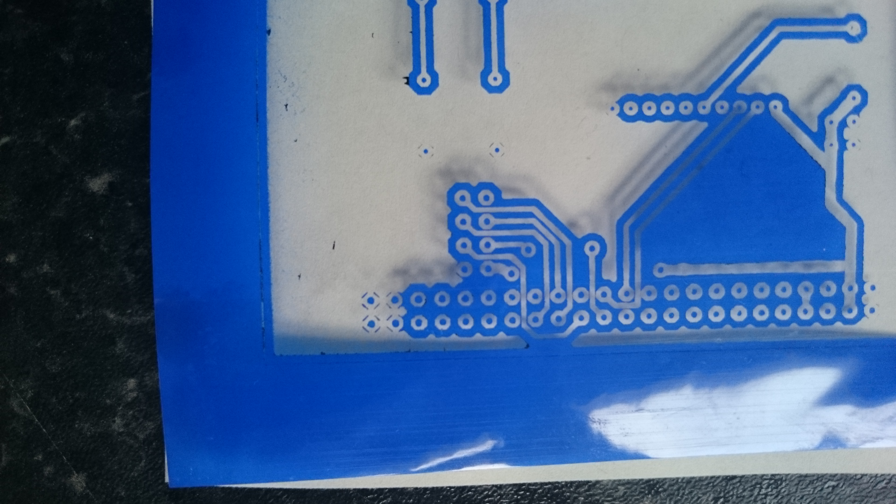
Hardware/Manufacturing Pictures/DSC_0135.JPG
