AlistairCheeseman/SmartHome-Project/Hardware/Manufacturing Pictures/DSC_0136.JPG

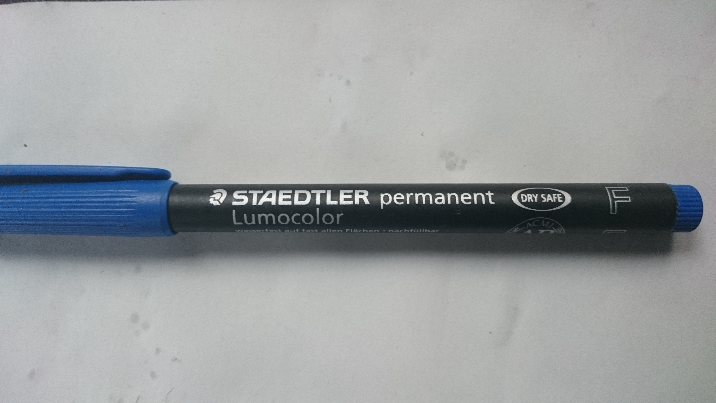
Hardware/Manufacturing Pictures/DSC_0136.JPG
