AlistairCheeseman/SmartHome-Project/Hardware/Manufacturing Pictures/DSC_0137.JPG

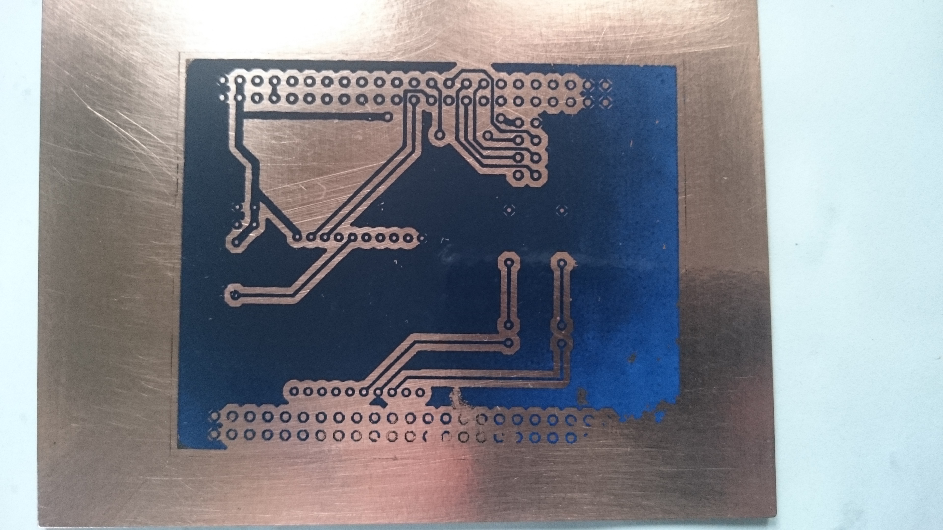
Hardware/Manufacturing Pictures/DSC_0137.JPG
