AlistairCheeseman/SmartHome-Project/Hardware/Manufacturing Pictures/DSC_0138.JPG

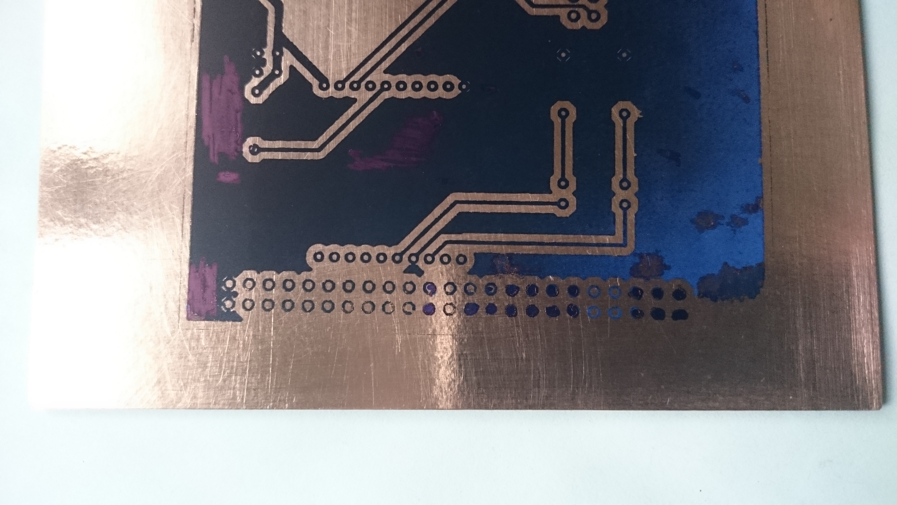
Hardware/Manufacturing Pictures/DSC_0138.JPG
