AlistairCheeseman/SmartHome-Project/Hardware/Manufacturing Pictures/DSC_0139.JPG

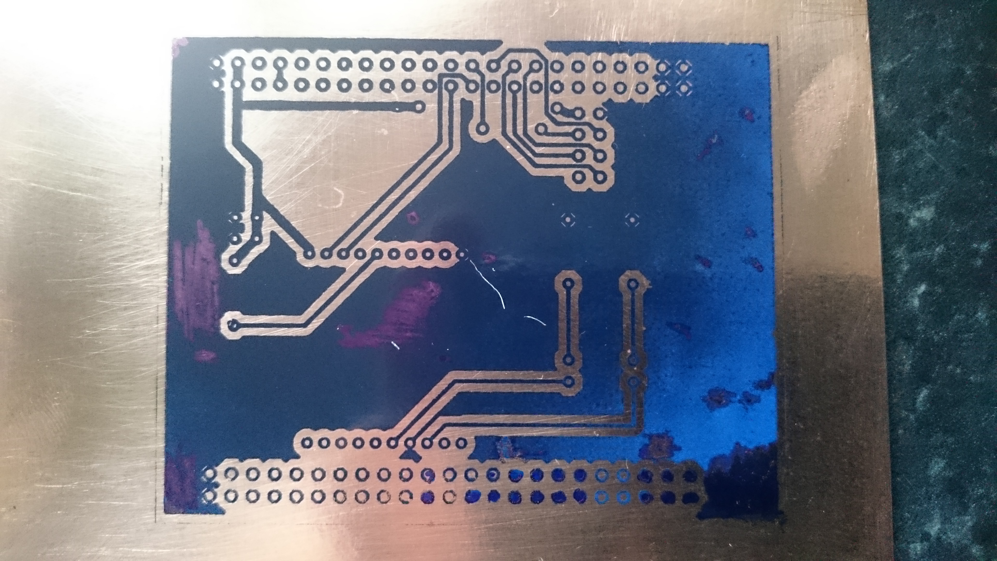
Hardware/Manufacturing Pictures/DSC_0139.JPG
