AlistairCheeseman/SmartHome-Project/Hardware/Manufacturing Pictures/DSC_0140.JPG

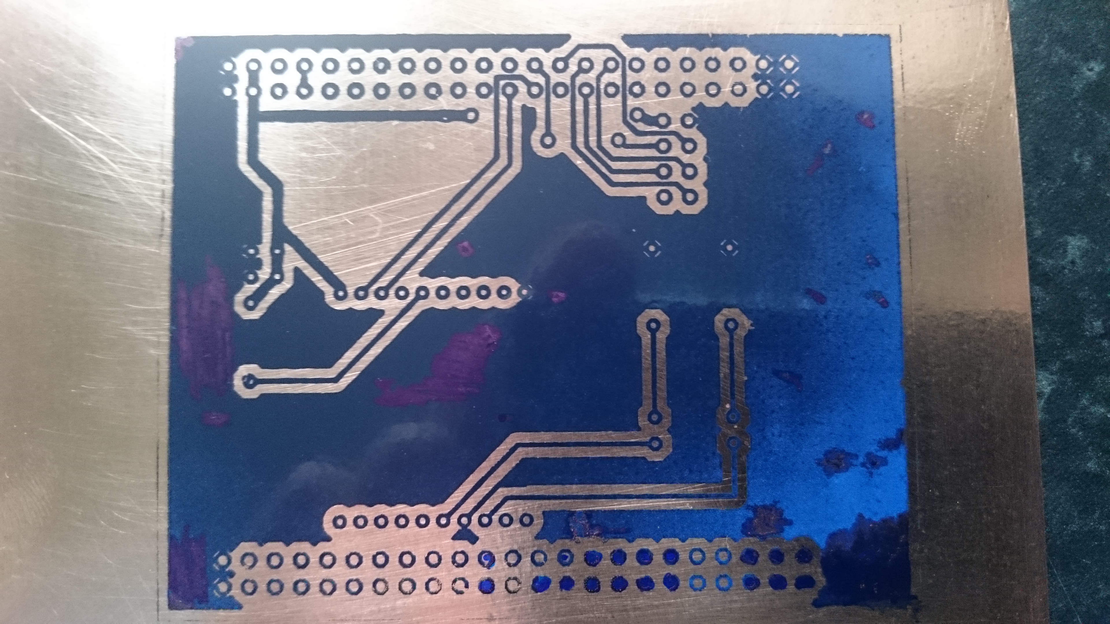
Hardware/Manufacturing Pictures/DSC_0140.JPG
