AlistairCheeseman/SmartHome-Project/Hardware/Manufacturing Pictures/DSC_0141.JPG

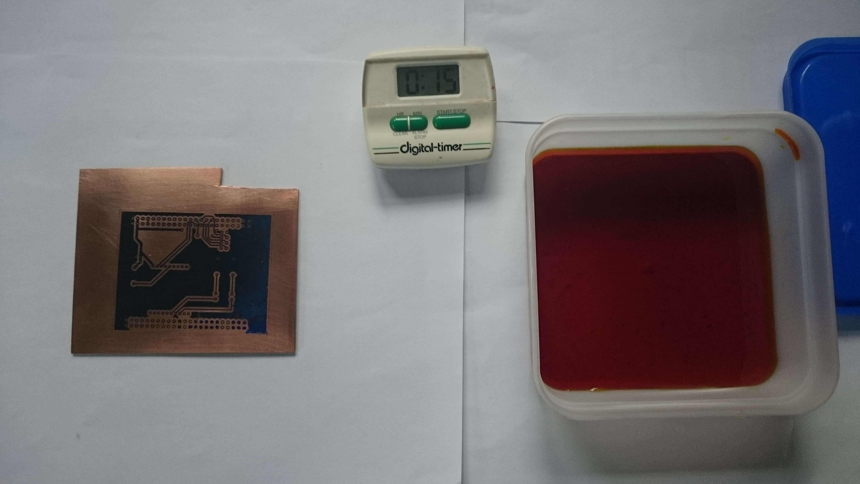
Hardware/Manufacturing Pictures/DSC_0141.JPG
