AlistairCheeseman/SmartHome-Project/Hardware/Manufacturing Pictures/DSC_0142.JPG

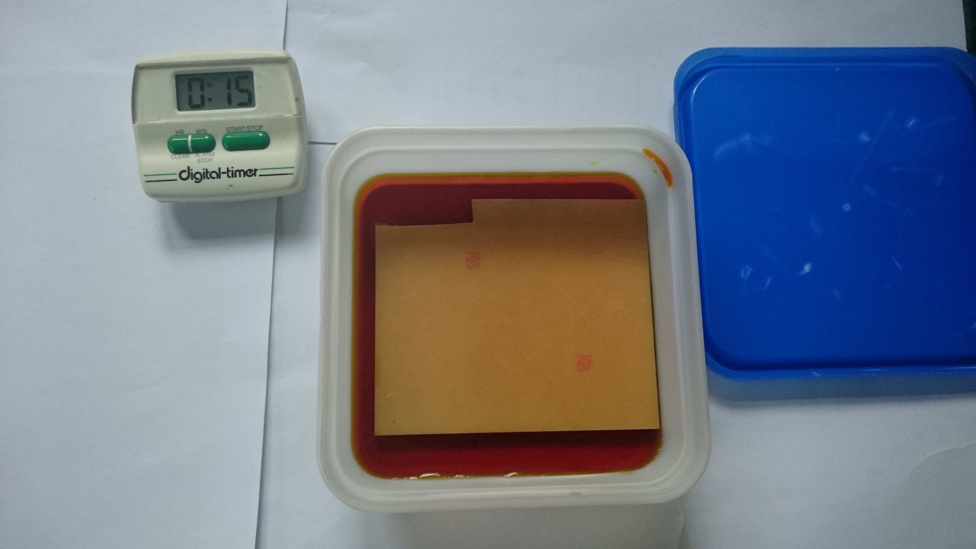
Hardware/Manufacturing Pictures/DSC_0142.JPG
