AlistairCheeseman/SmartHome-Project/Hardware/Manufacturing Pictures/DSC_0144.JPG

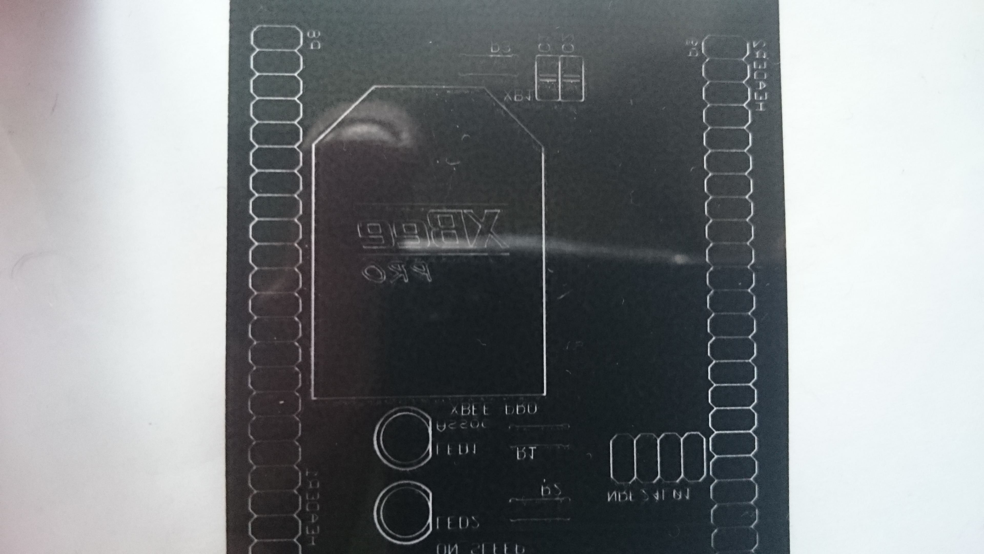
Hardware/Manufacturing Pictures/DSC_0144.JPG
