AlistairCheeseman/SmartHome-Project/Hardware/Manufacturing Pictures/DSC_0145.JPG

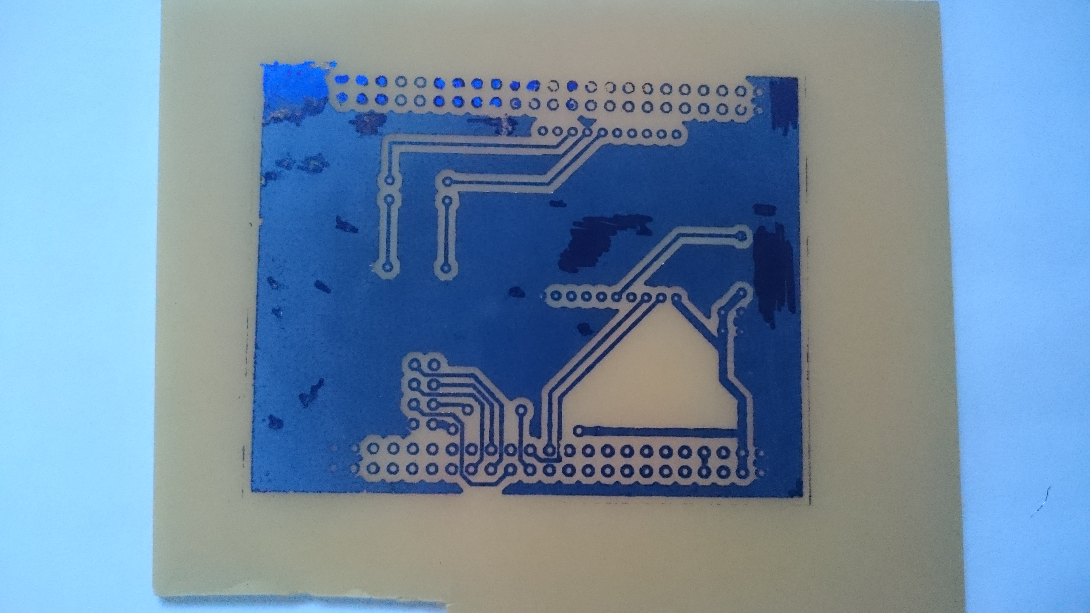
Hardware/Manufacturing Pictures/DSC_0145.JPG
