AlistairCheeseman/SmartHome-Project/Hardware/Manufacturing Pictures/DSC_0146.JPG

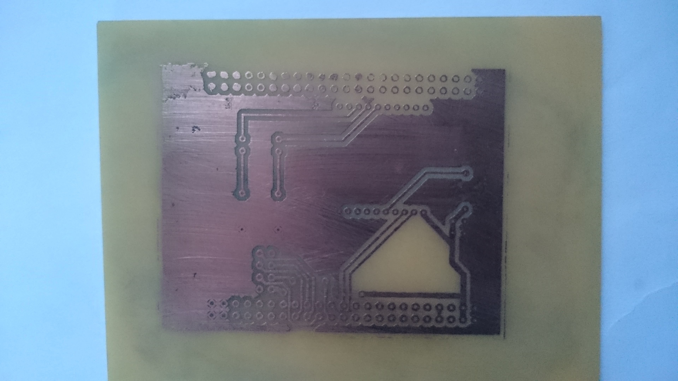
Hardware/Manufacturing Pictures/DSC_0146.JPG
