AlistairCheeseman/SmartHome-Project/Hardware/Manufacturing Pictures/DSC_0147.JPG

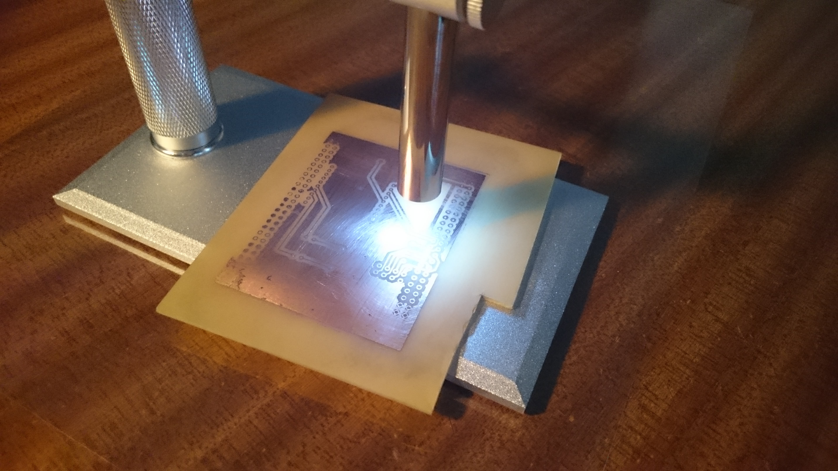
Hardware/Manufacturing Pictures/DSC_0147.JPG
