AlistairCheeseman/SmartHome-Project/Hardware/Manufacturing Pictures/DSC_0148.JPG

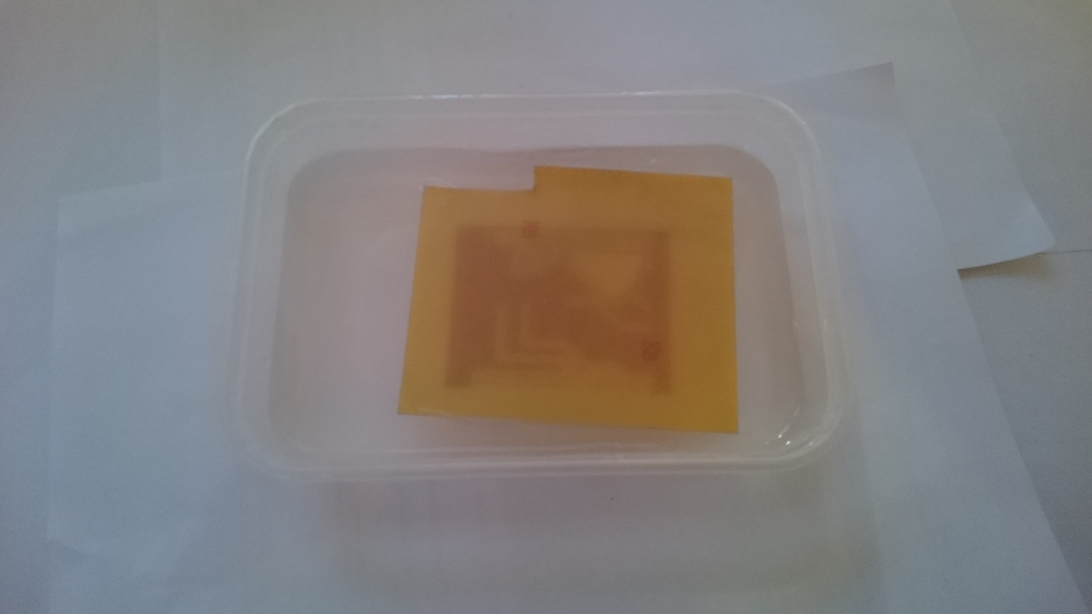
Hardware/Manufacturing Pictures/DSC_0148.JPG
