AlistairCheeseman/SmartHome-Project/Hardware/Manufacturing Pictures/DSC_0149.JPG

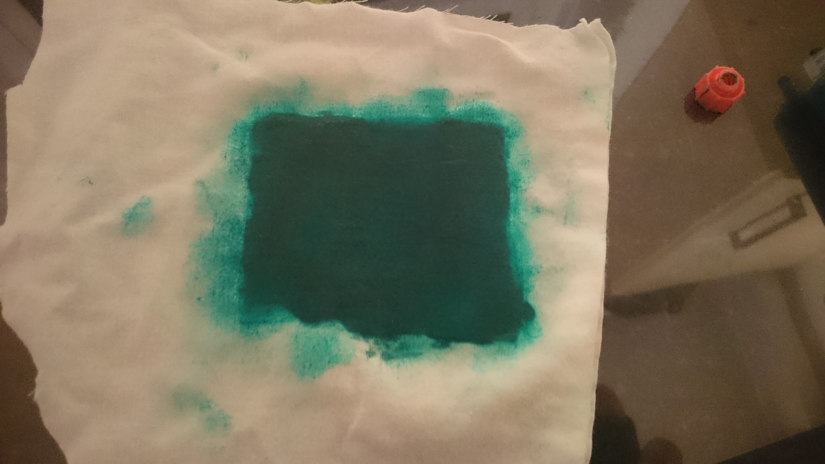
Hardware/Manufacturing Pictures/DSC_0149.JPG
