AlistairCheeseman/SmartHome-Project/Hardware/Manufacturing Pictures/DSC_0150.JPG

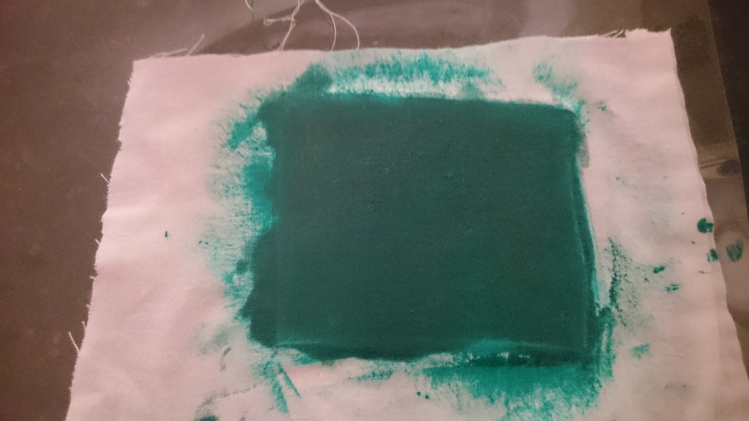
Hardware/Manufacturing Pictures/DSC_0150.JPG
