AlistairCheeseman/SmartHome-Project/Hardware/Manufacturing Pictures/DSC_0151.JPG

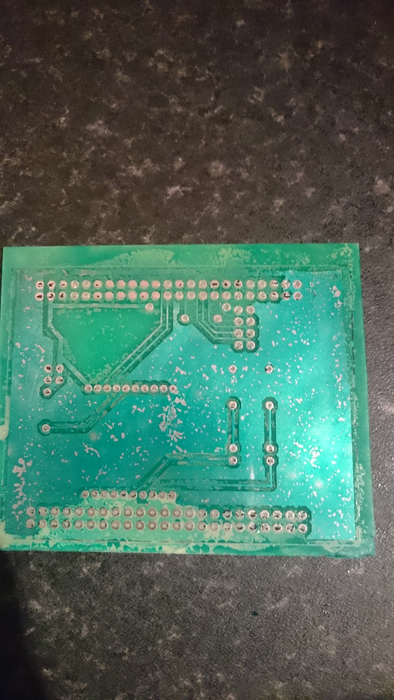
Hardware/Manufacturing Pictures/DSC_0151.JPG
