AlistairCheeseman/SmartHome-Project/Hardware/Manufacturing Pictures/DSC_0152.JPG

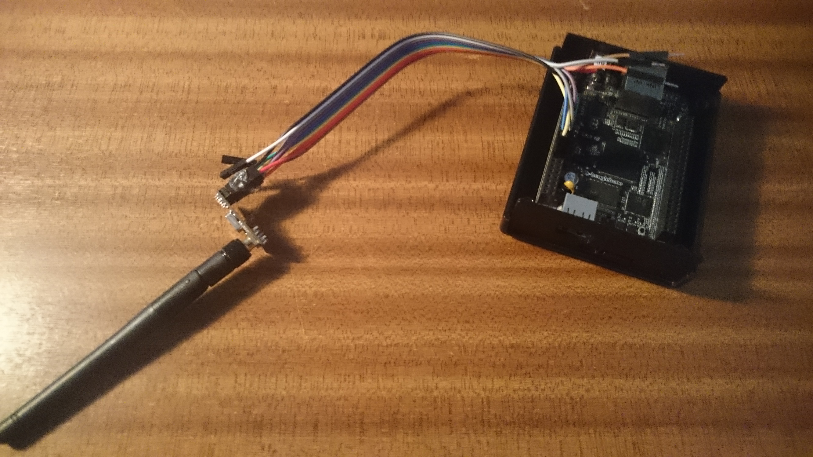
Hardware/Manufacturing Pictures/DSC_0152.JPG
