AlistairCheeseman/SmartHome-Project/Hardware/Manufacturing Pictures/DSC_0153.JPG

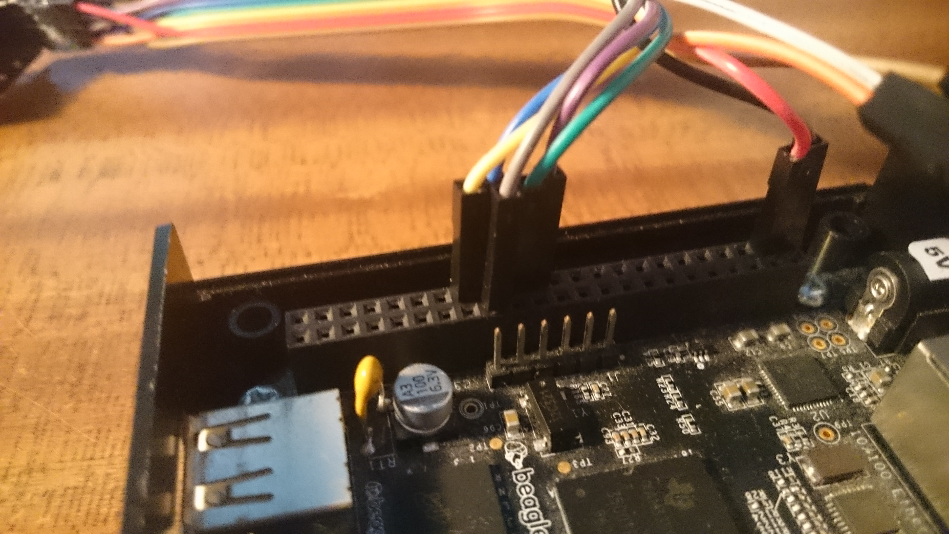
Hardware/Manufacturing Pictures/DSC_0153.JPG
