AlistairCheeseman/SmartHome-Project/Hardware/Manufacturing Pictures/DSC_0154.JPG

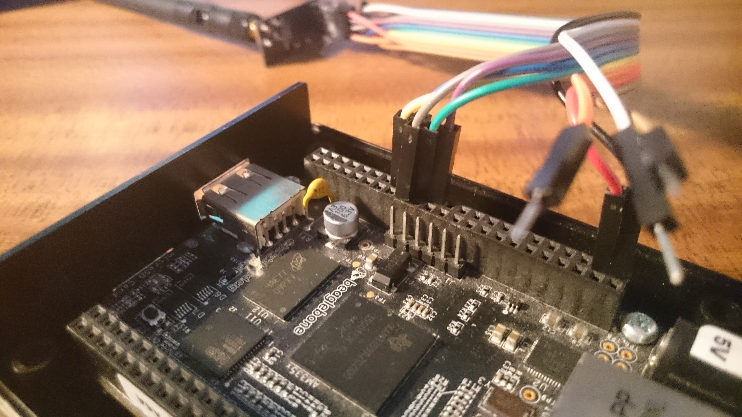
Hardware/Manufacturing Pictures/DSC_0154.JPG
