AlistairCheeseman/SmartHome-Project/Hardware/Manufacturing Pictures/DSC_0155.JPG

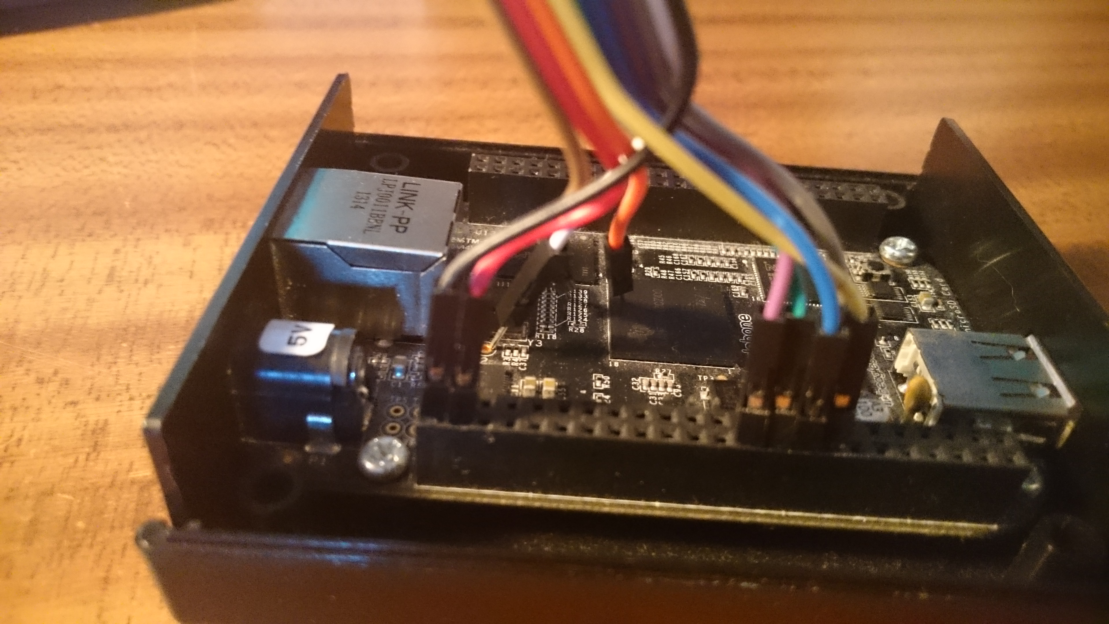
Hardware/Manufacturing Pictures/DSC_0155.JPG
