AlistairCheeseman/SmartHome-Project/Hardware/Manufacturing Pictures/DSC_0206.JPG

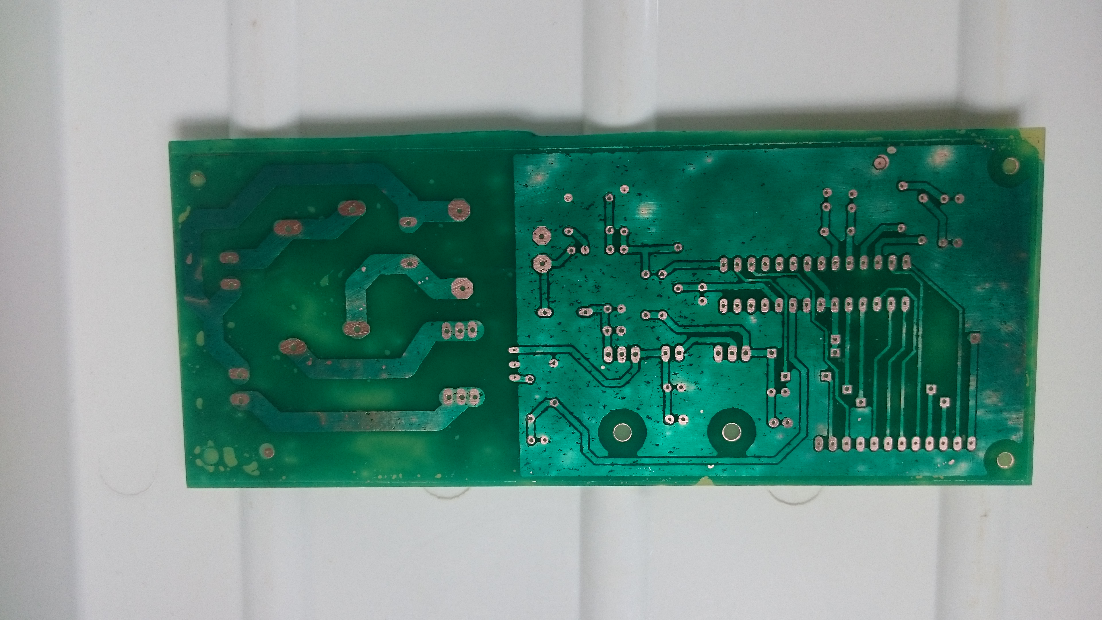
Hardware/Manufacturing Pictures/DSC_0206.JPG
