AlistairCheeseman/SmartHome-Project/Hardware/Manufacturing Pictures/DSC_0207.JPG

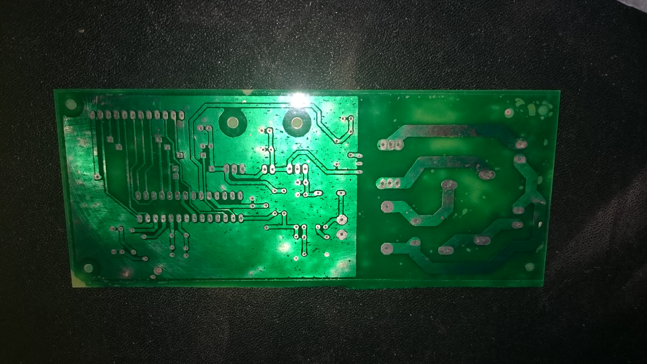
Hardware/Manufacturing Pictures/DSC_0207.JPG
