AlistairCheeseman/SmartHome-Project/Hardware/Manufacturing Pictures/DSC_0208.JPG

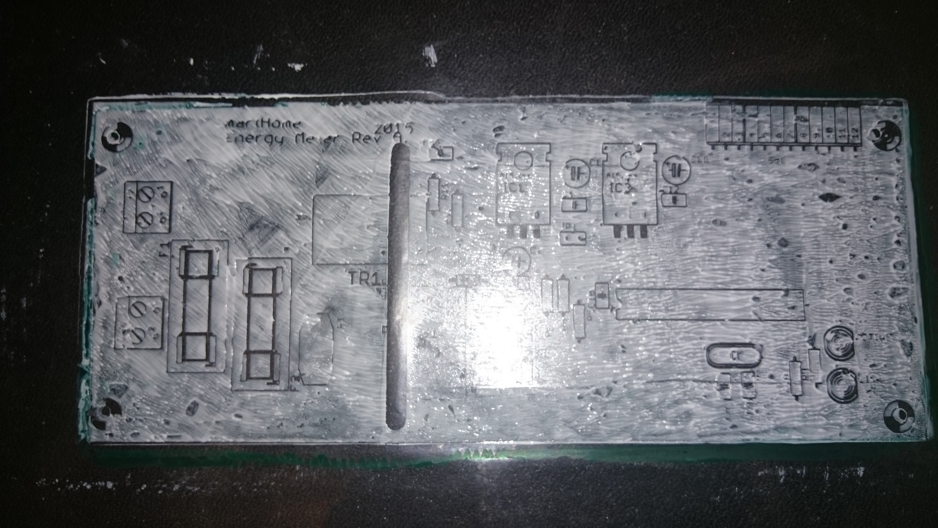
Hardware/Manufacturing Pictures/DSC_0208.JPG
