AlistairCheeseman/SmartHome-Project/Hardware/Manufacturing Pictures/DSC_0209.JPG

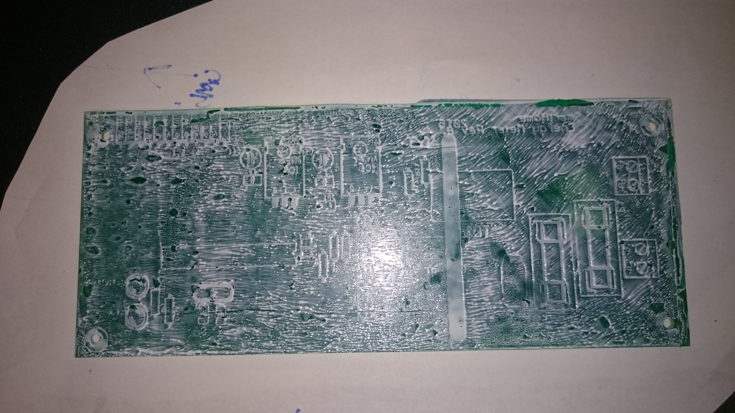
Hardware/Manufacturing Pictures/DSC_0209.JPG
