AlistairCheeseman/SmartHome-Project/Hardware/BeagleboneCape/BeagleboneCape.pdf

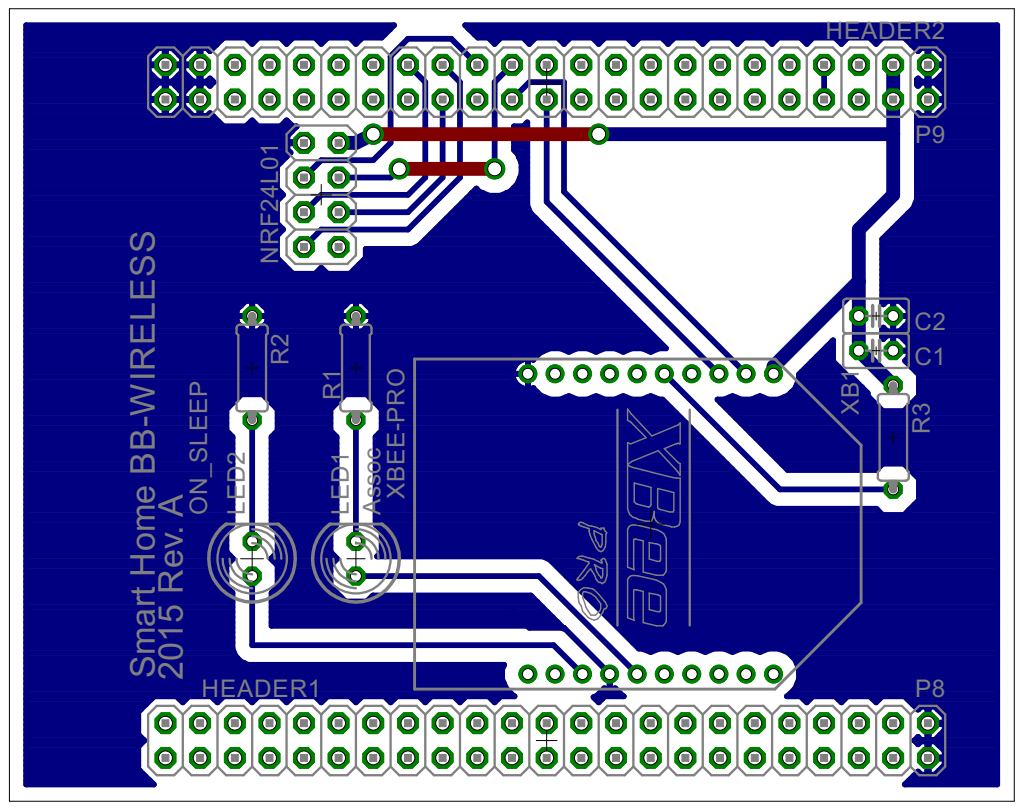
[picture p79: page 1]

NRF24L01 XB1 R1 LED1 P8P9 LED2 R2C1 C2R3 XBEE-PRO Assoc HEADER1 HEADER2 ON_SLEEP Smart Home BB-WIRELESS 2015 Rev. A
