AlistairCheeseman/SmartHome-Project/Hardware/EnergySensor/Energy SensorRevB-Etch.pdf

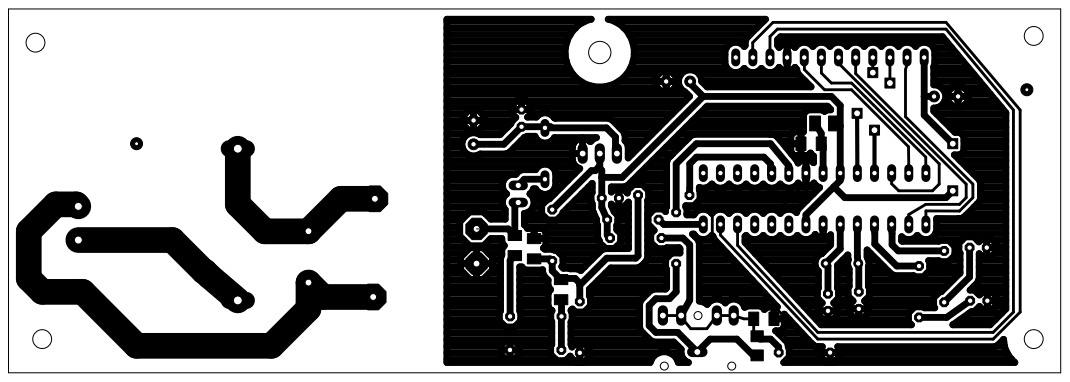
[picture p92: page 1]
