AlistairCheeseman/SmartHome-Project/Hardware/EnergySensor/Energy SensorRevB-EtchM.pdf

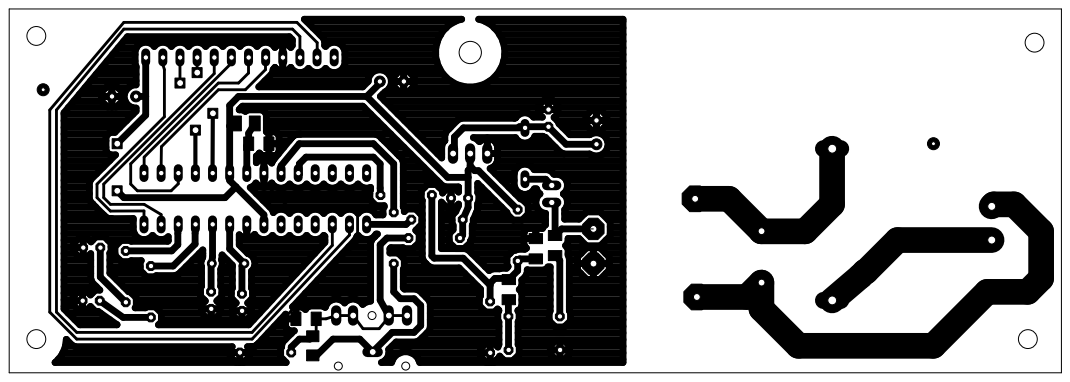
[picture p93: page 1]
