AlistairCheeseman/SmartHome-Project/Hardware/EnergySensor/Energy SensorRevB-Resist.pdf

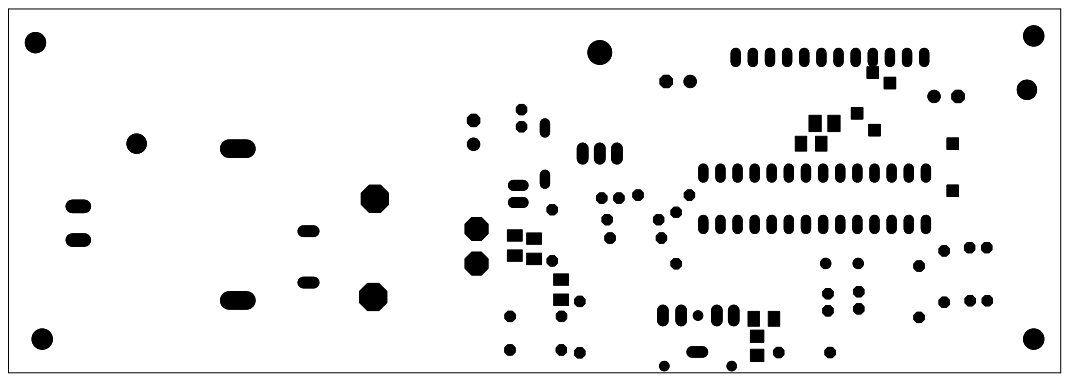
[picture p94: page 1]
