AlistairCheeseman/SmartHome-Project/Hardware/EnergySensor/Energy SensorRevB-ResistM.pdf

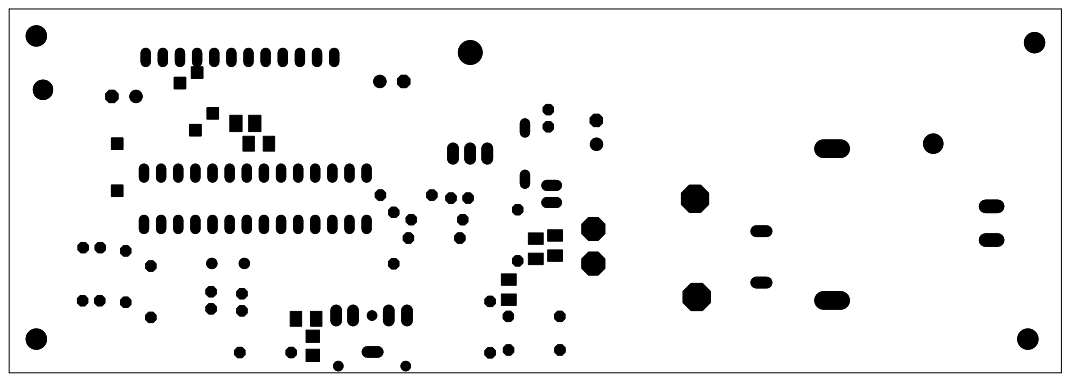
[picture p95: page 1]
