AlistairCheeseman/SmartHome-Project/Hardware/EnergySensor/Energy SensorRevB-Silk.pdf

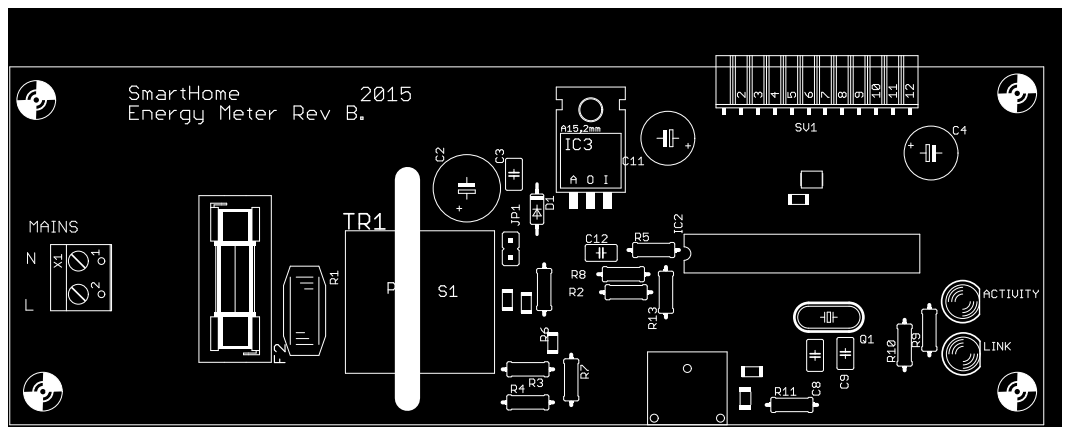
[picture p96: page 1]
