AlistairCheeseman/SmartHome-Project/Hardware/EnergySensor/Energy SensorRevB-SilkM.pdf

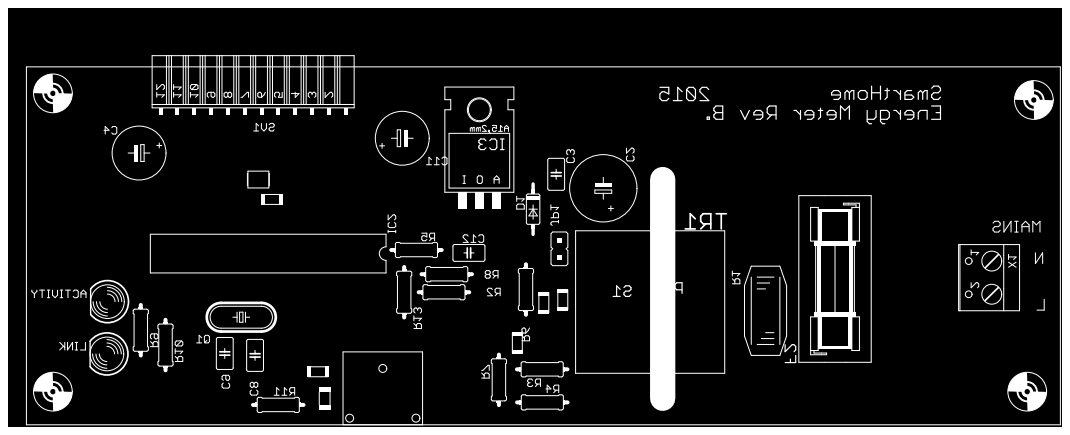
[picture p97: page 1]
