AlistairCheeseman/SmartHome-Project/Hardware/EnvironmentSensor/Environment Sensor-BottomEtch.pdf

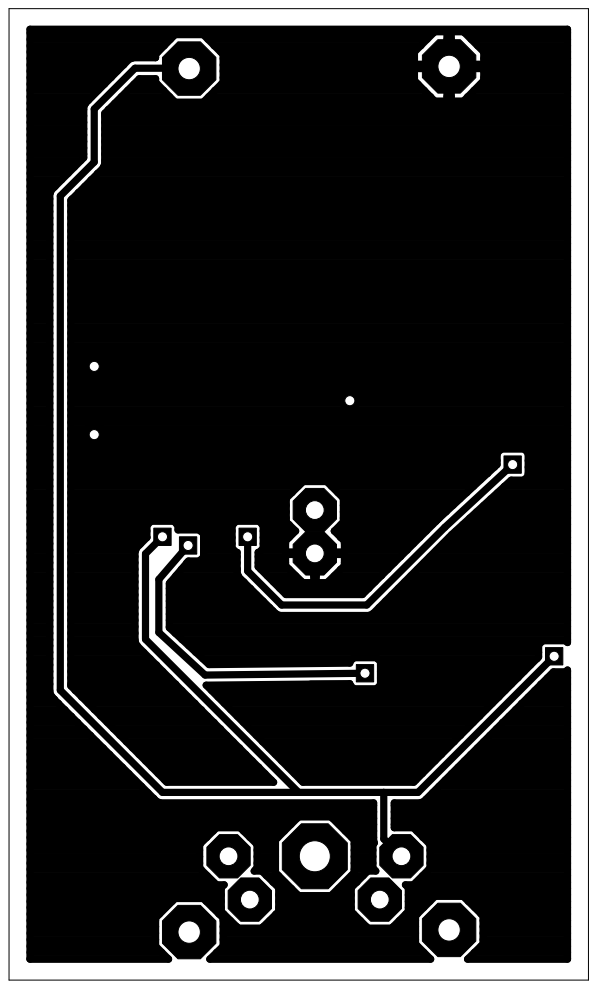
[picture p98: page 1]
