AlistairCheeseman/SmartHome-Project/Hardware/EnvironmentSensor/Environment Sensor-BottomEtchM.pdf

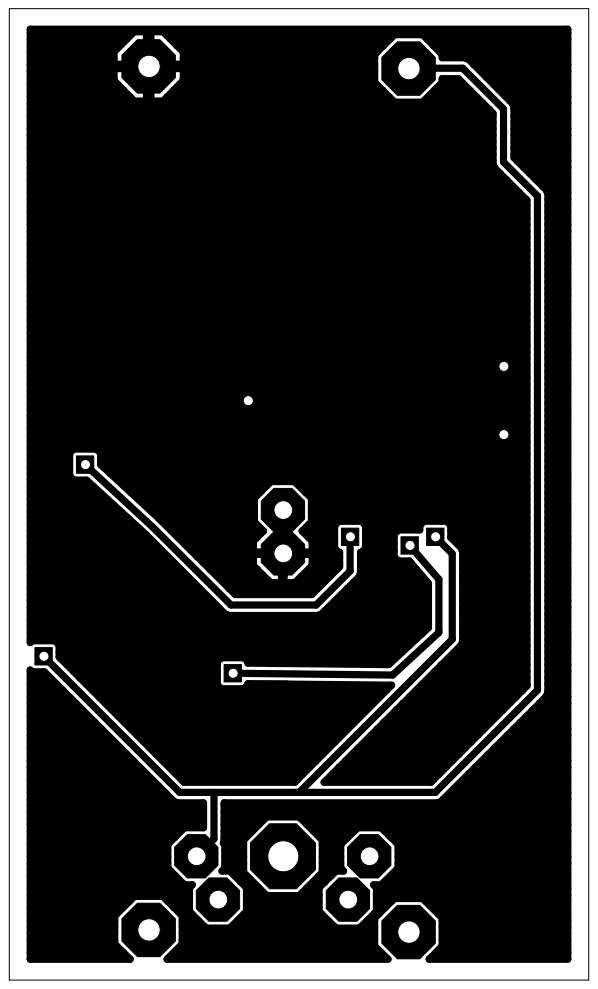
[picture p99: page 1]
