AlistairCheeseman/SmartHome-Project/Hardware/EnvironmentSensor/Environment Sensor-BottomResist.pdf

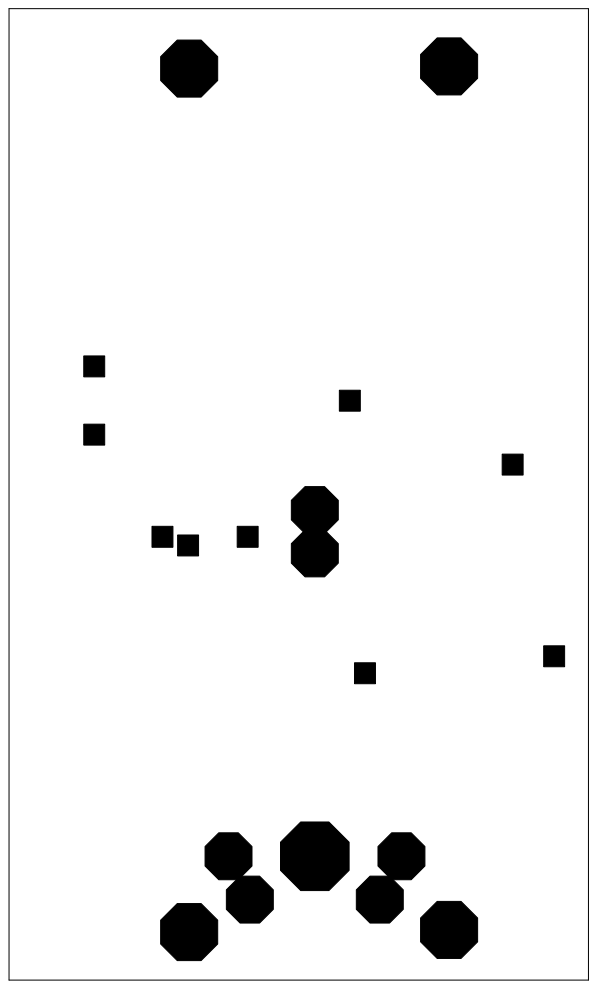
[picture p100: page 1]
