AlistairCheeseman/SmartHome-Project/Hardware/EnvironmentSensor/Environment Sensor-BottomResistM.pdf

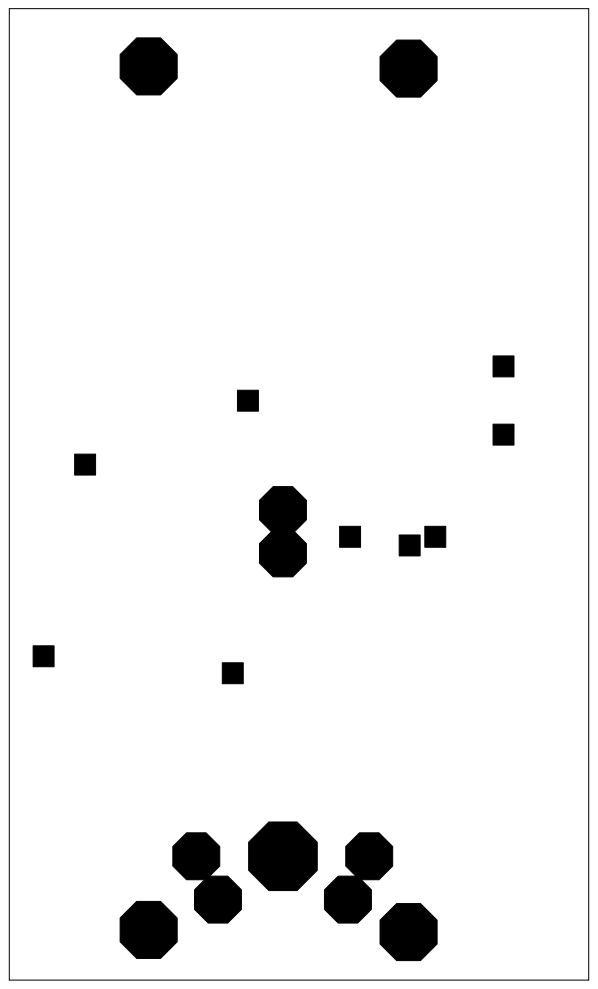
[picture p101: page 1]
