AlistairCheeseman/SmartHome-Project/Hardware/EnvironmentSensor/Environment Sensor-ResistTop.pdf

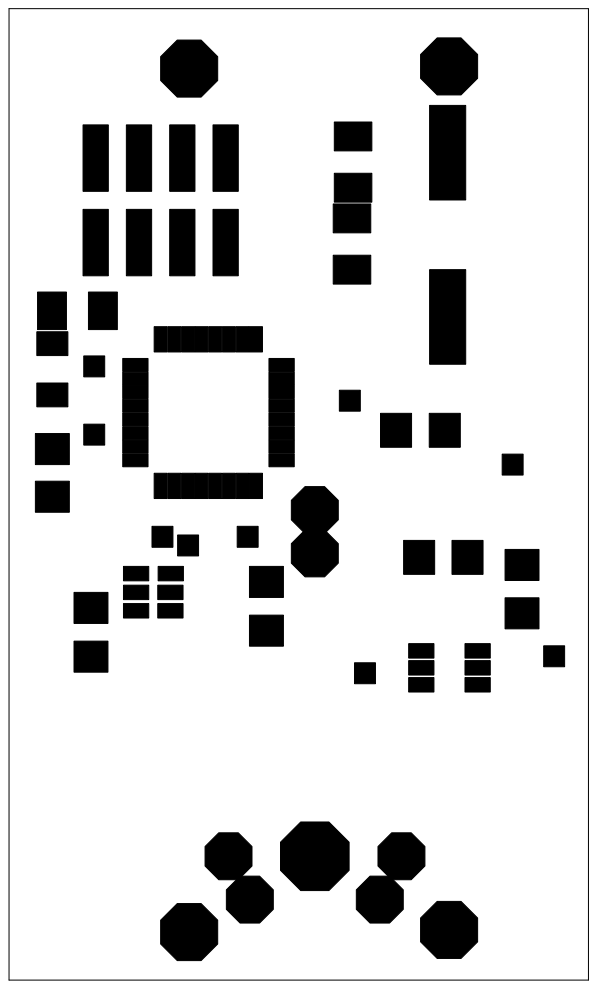
[picture p102: page 1]
