AlistairCheeseman/SmartHome-Project/Hardware/EnvironmentSensor/Environment Sensor-ResistTopM.pdf

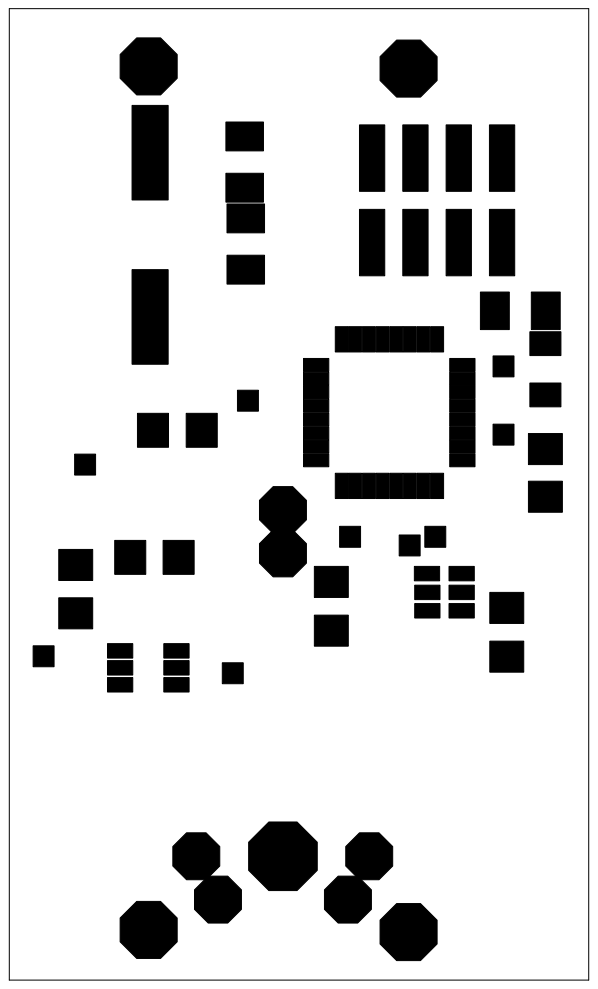
[picture p103: page 1]
