AlistairCheeseman/SmartHome-Project/Hardware/EnvironmentSensor/Environment Sensor-TopEtch.pdf

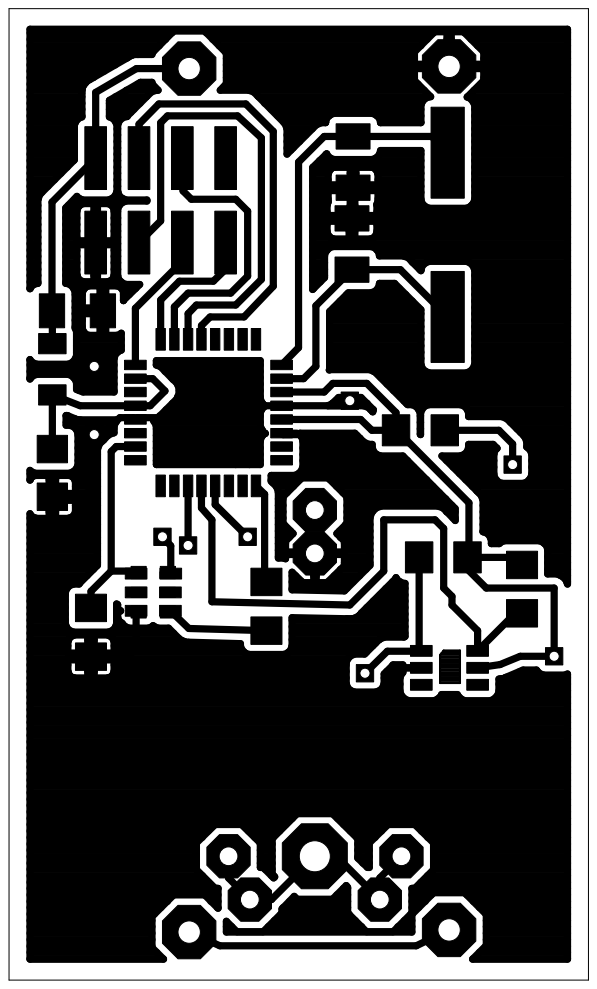
[picture p104: page 1]
