AlistairCheeseman/SmartHome-Project/Hardware/EnvironmentSensor/Environment Sensor-TopEtchM.pdf

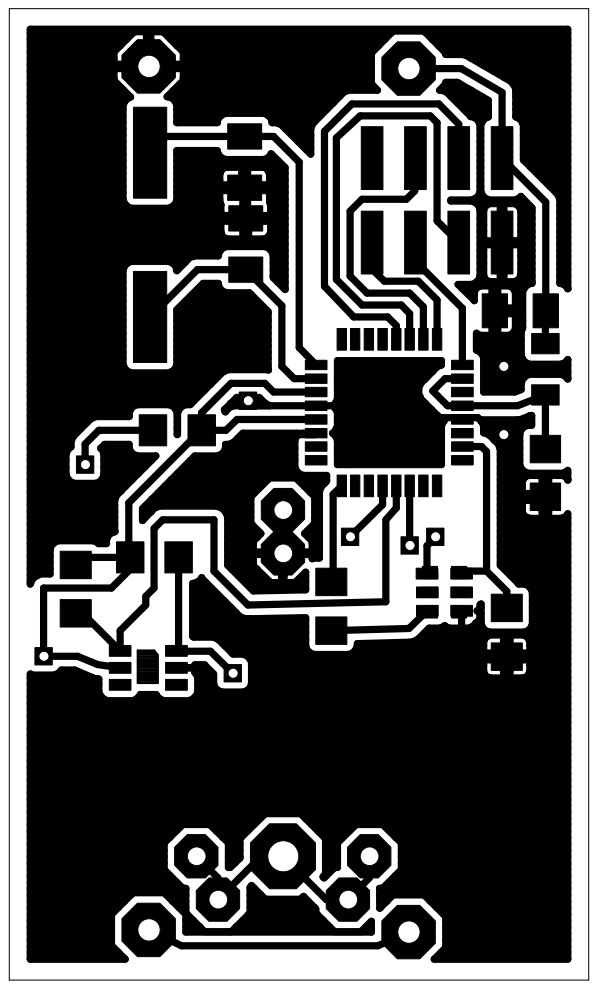
[picture p105: page 1]
