AlistairCheeseman/SmartHome-Project/Hardware/HeatingController/Heating Controller-Etch.pdf

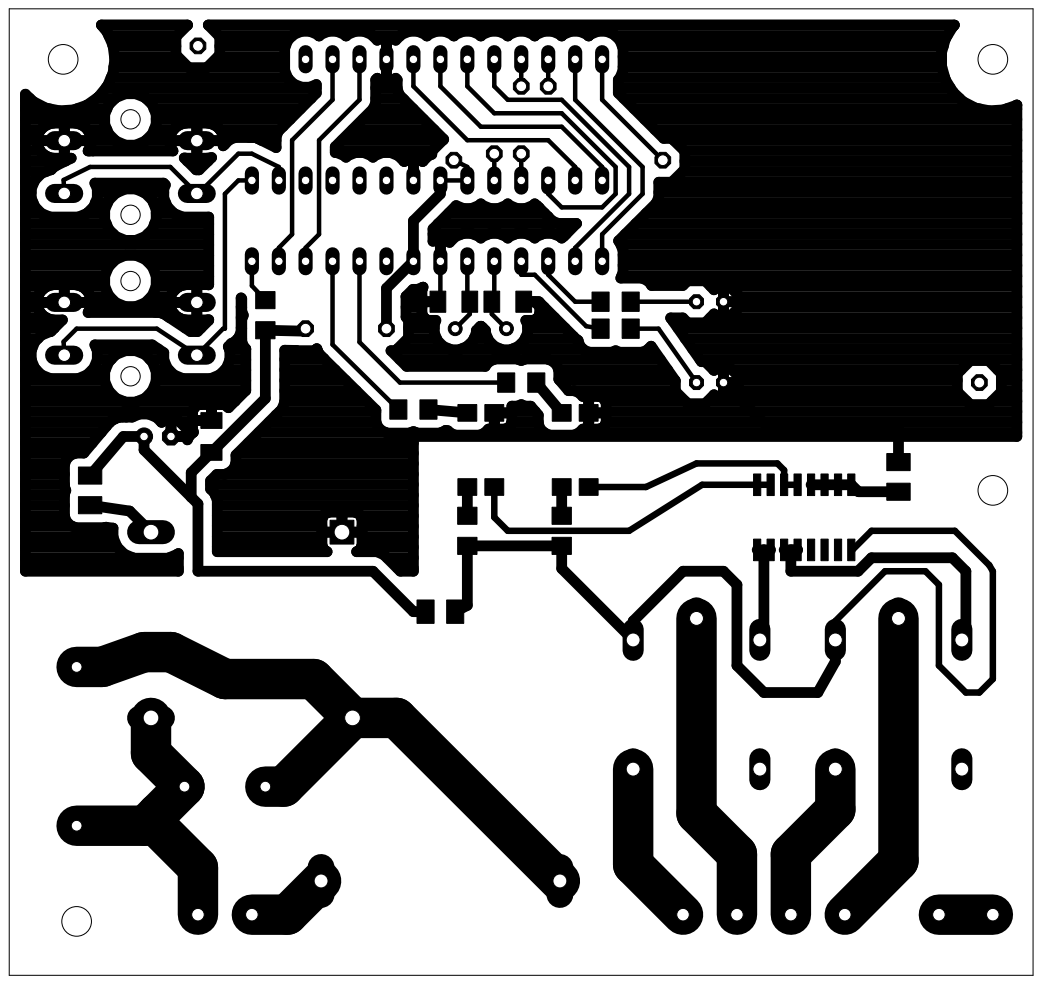
[picture p106: page 1]
