AlistairCheeseman/SmartHome-Project/Hardware/HeatingController/Heating Controller-EtchM.pdf

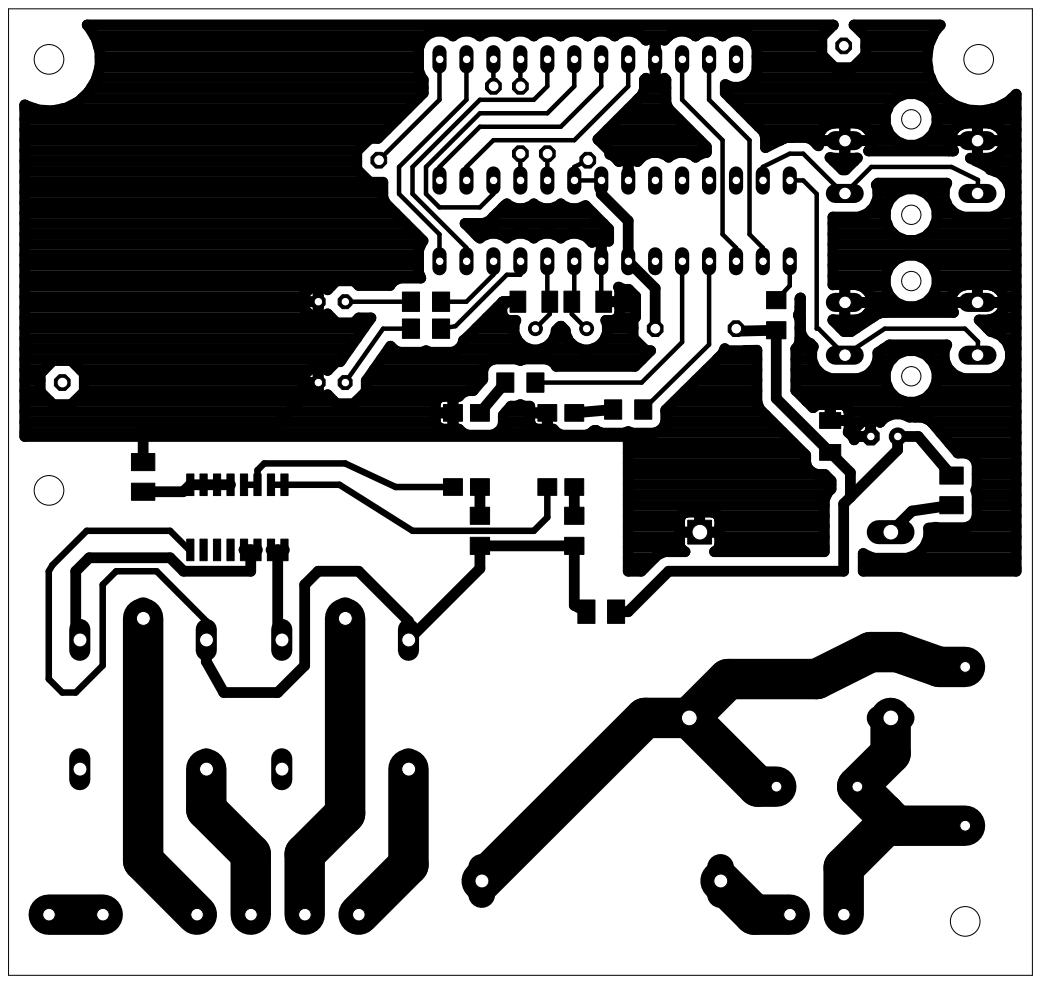
[picture p107: page 1]
