AlistairCheeseman/SmartHome-Project/Hardware/HeatingController/Heating Controller-Resist.pdf

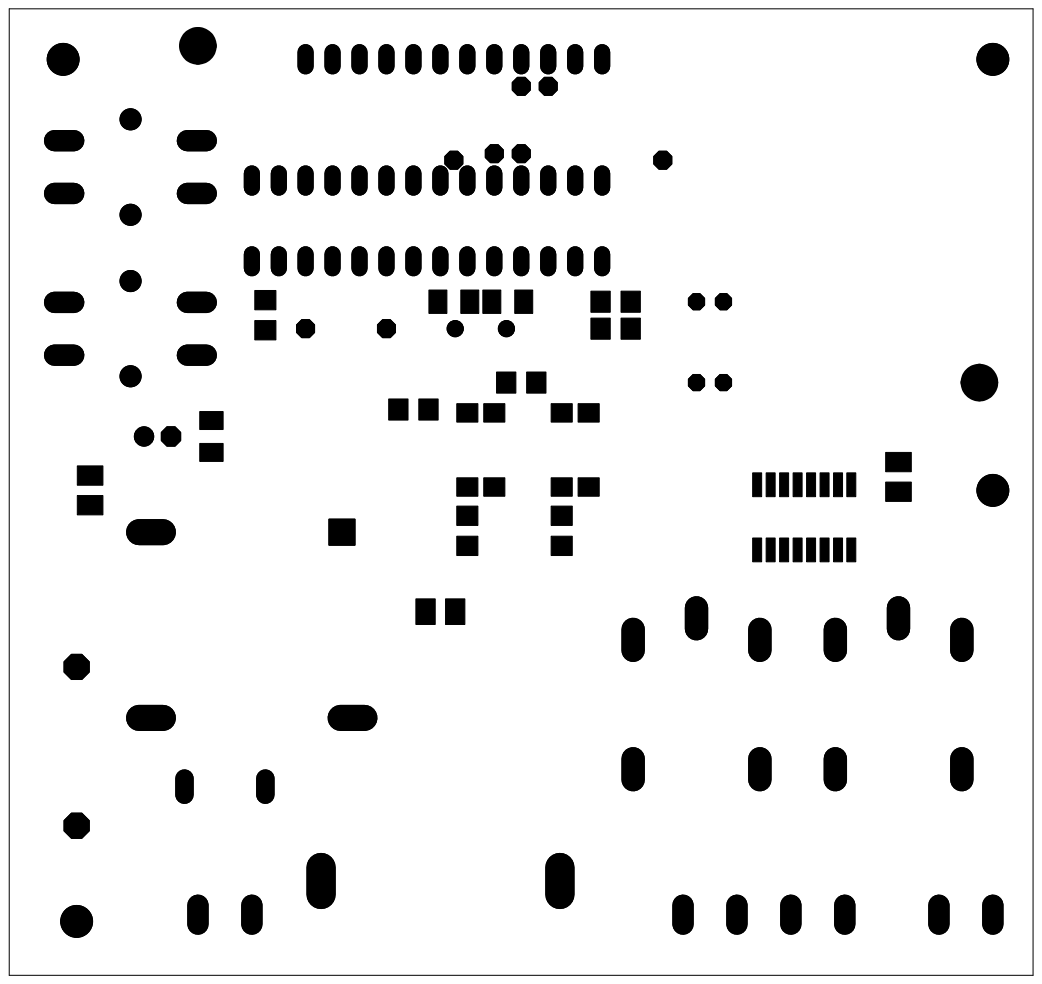
[picture p108: page 1]
