AlistairCheeseman/SmartHome-Project/Hardware/HeatingController/Heating Controller-ResistM.pdf

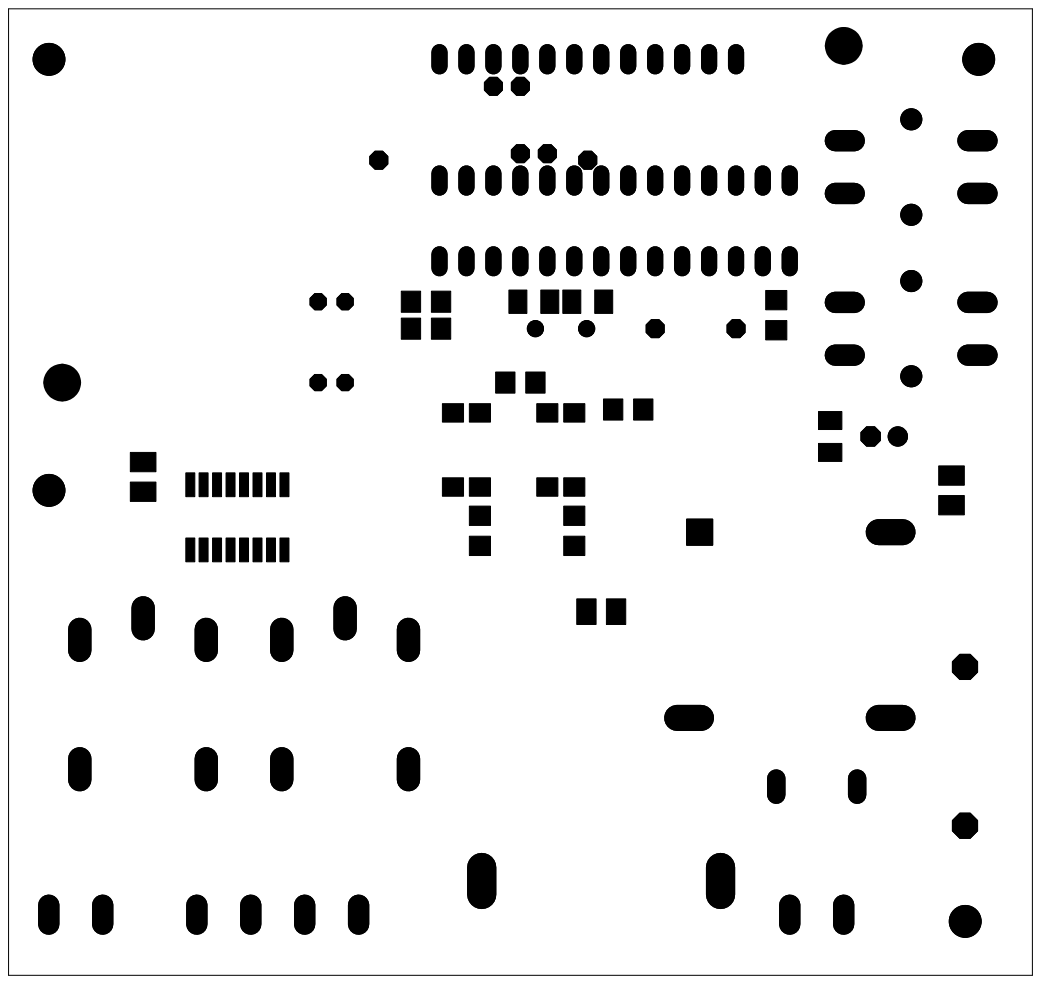
[picture p109: page 1]
