AlistairCheeseman/SmartHome-Project/Hardware/HeatingController/Heating Controller-Silk.pdf

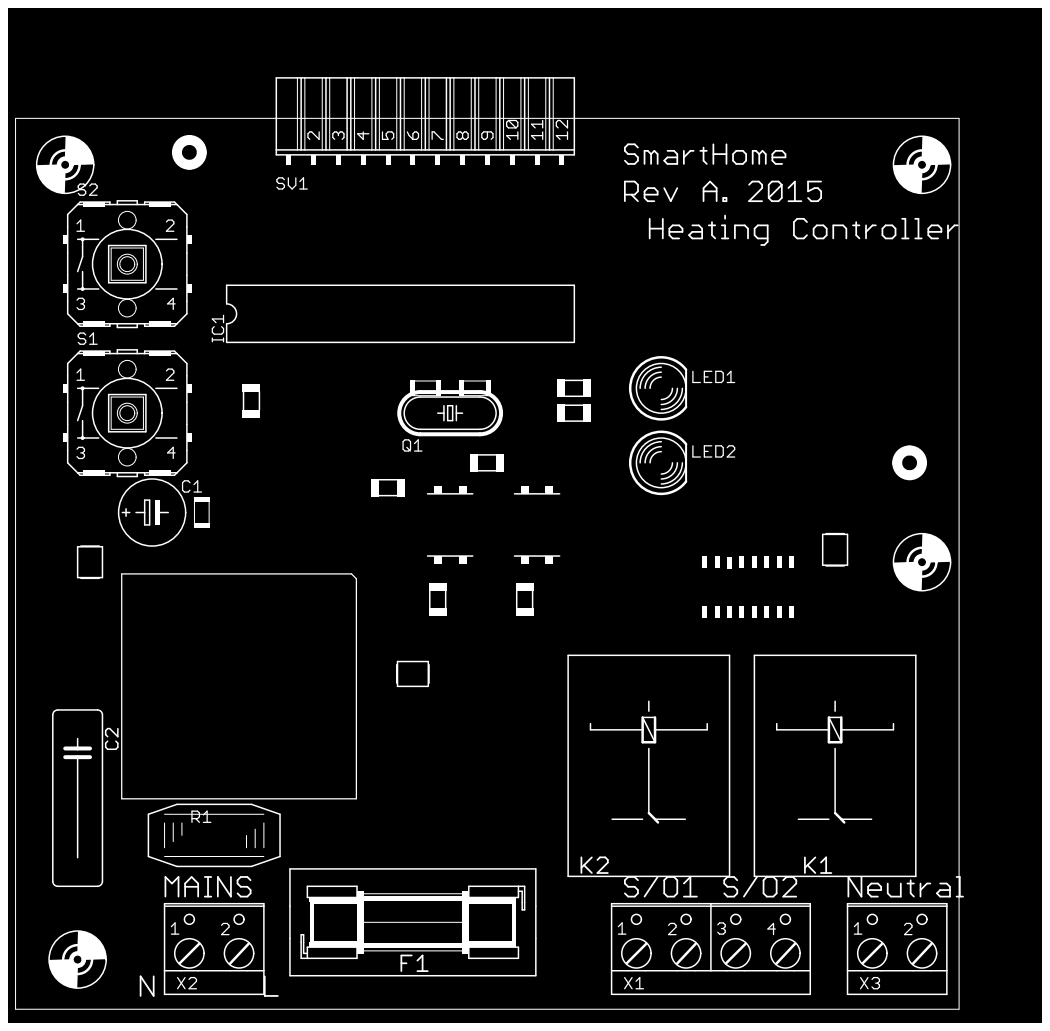
[picture p110: page 1]
