AlistairCheeseman/SmartHome-Project/Hardware/HeatingController/Heating Controller-SilkM.pdf

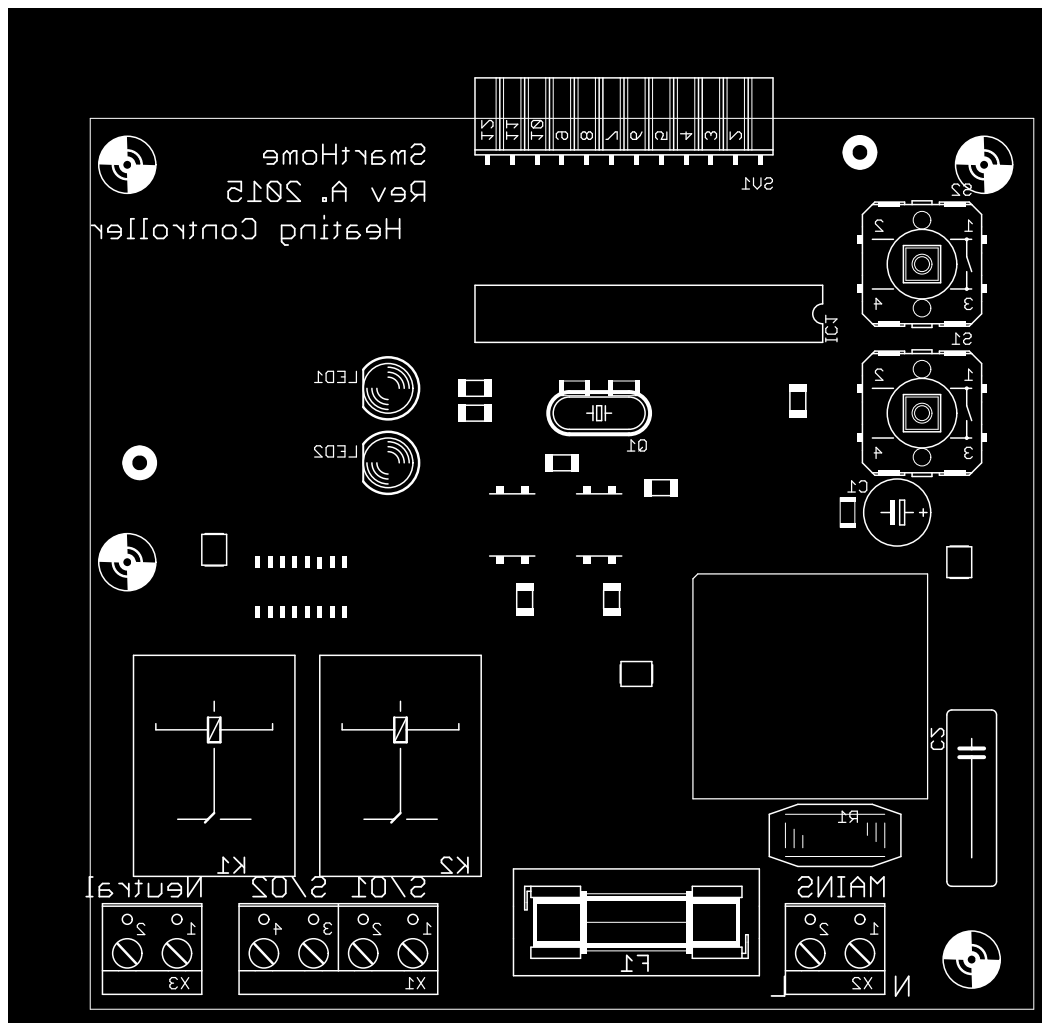
[picture p111: page 1]
