AlistairCheeseman/SmartHome-Project/Hardware/LightSwitch/LightSwitch-Etch.pdf

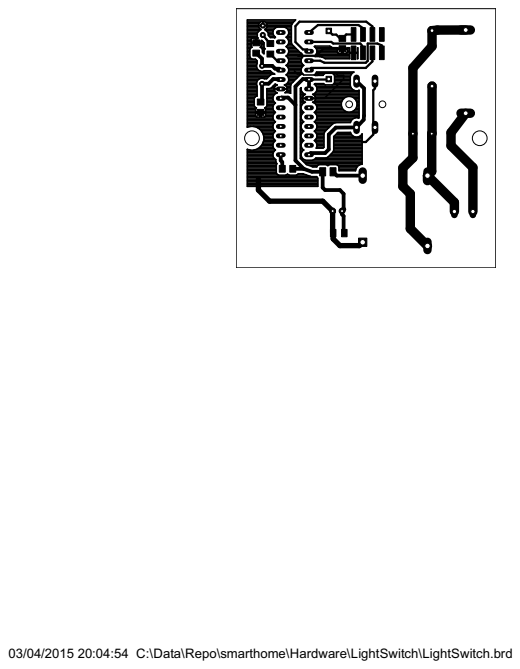
[picture p112: page 1]

03/04/2015 20:04:54 C:\Data\Repo\smarthome\Hardware\LightSwitch\LightSwitch.brd
