AlistairCheeseman/SmartHome-Project/Hardware/LightSwitch/LightSwitch-EtchM.pdf

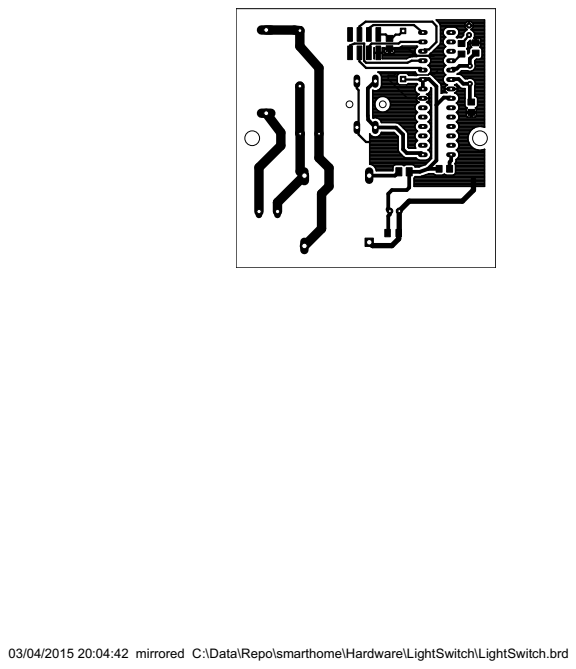
[picture p113: page 1]

03/04/2015 20:04:42 mirrored C:\Data\Repo\smarthome\Hardware\LightSwitch\LightSwitch.brd
