AlistairCheeseman/SmartHome-Project/Hardware/LightSwitch/LightSwitch-Resist.pdf

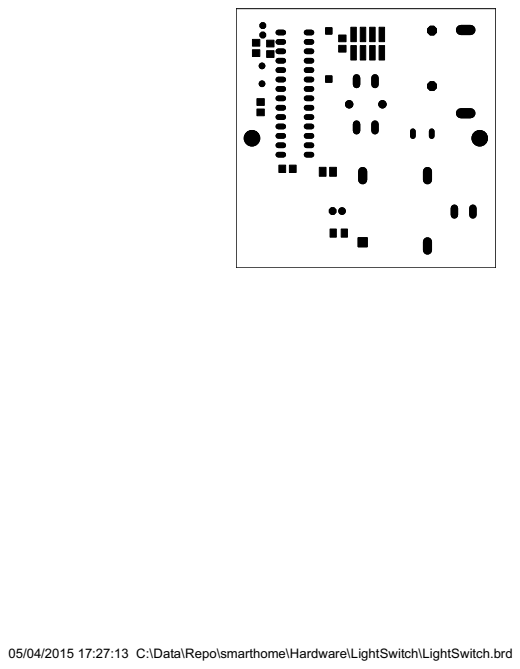
[picture p114: page 1]

05/04/2015 17:27:13 C:\Data\Repo\smarthome\Hardware\LightSwitch\LightSwitch.brd
