AlistairCheeseman/SmartHome-Project/Hardware/LightSwitch/LightSwitch-ResistM.pdf

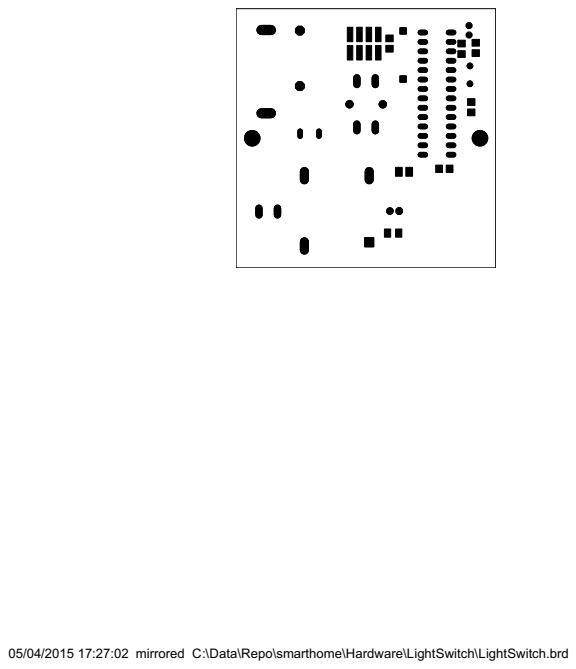
[picture p115: page 1]

05/04/2015 17:27:02 mirrored C:\Data\Repo\smarthome\Hardware\LightSwitch\LightSwitch.brd
