AlistairCheeseman/SmartHome-Project/Hardware/LightSwitch/LightSwitch-Silk.pdf

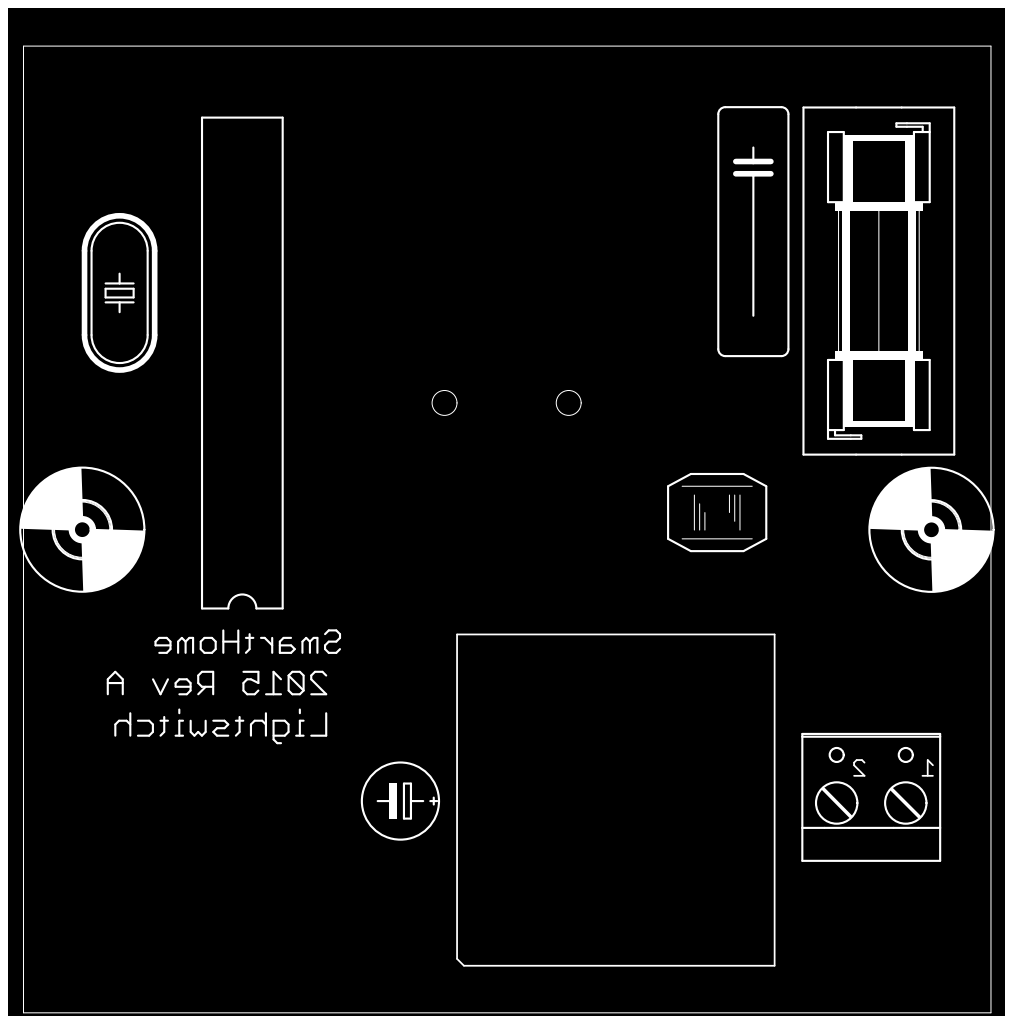
[picture p116: page 1]
