AlistairCheeseman/SmartHome-Project/Hardware/LightSwitch/LightSwitch-SilkM.pdf

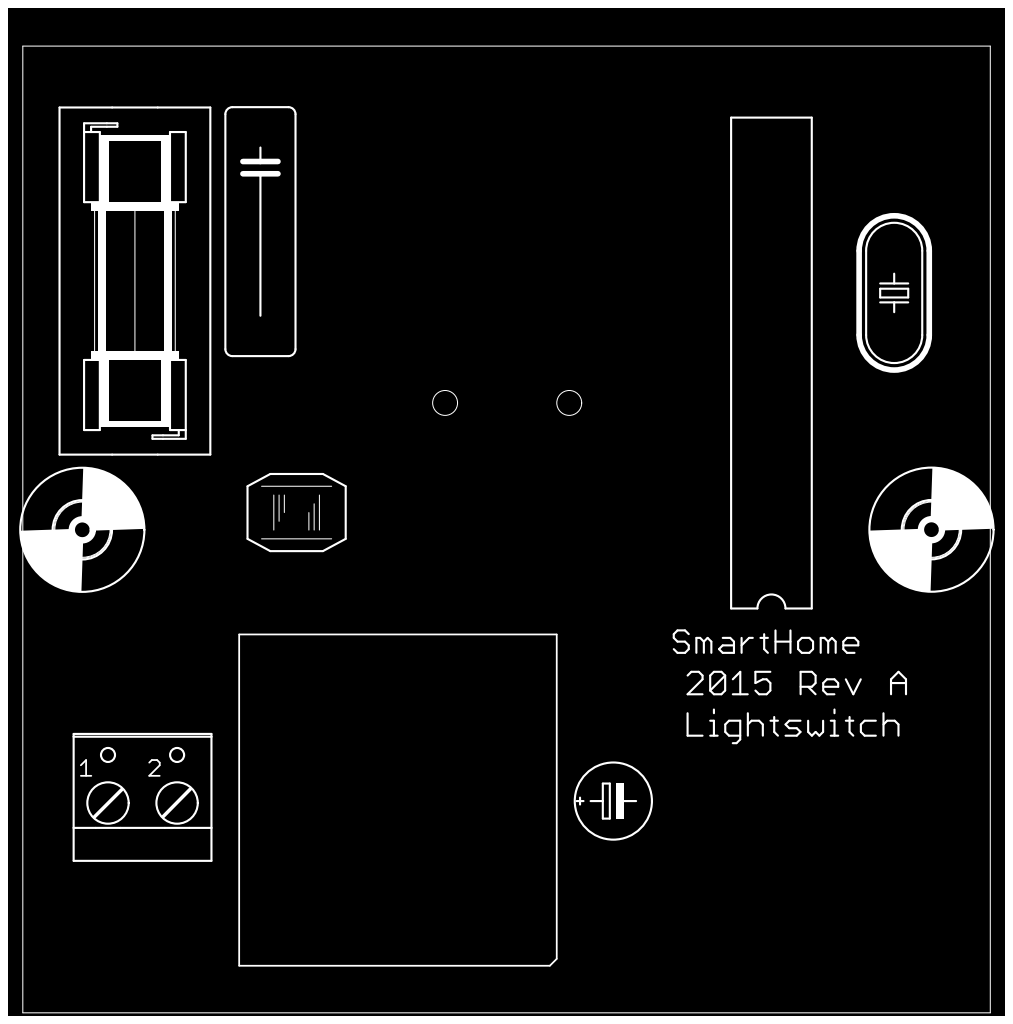
[picture p117: page 1]
