AlistairCheeseman/SmartHome-Project/Hardware/Connections/NRF24L01_PCB-Etch.pdf

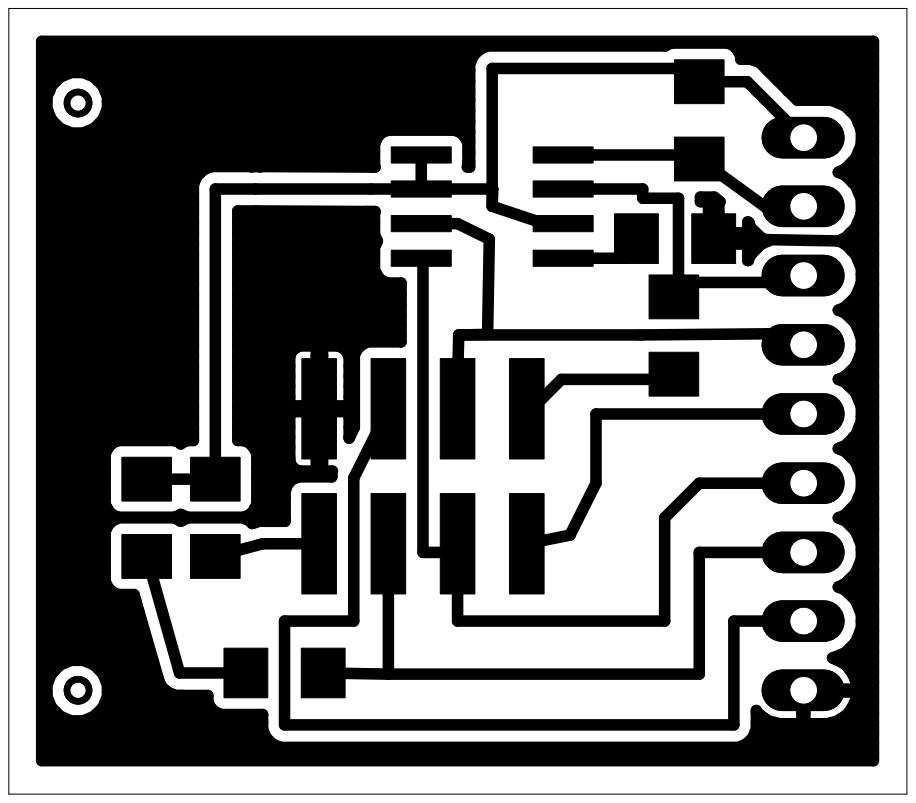
[picture p118: page 1]
