AlistairCheeseman/SmartHome-Project/Hardware/Connections/NRF24L01_PCB-Silk.pdf

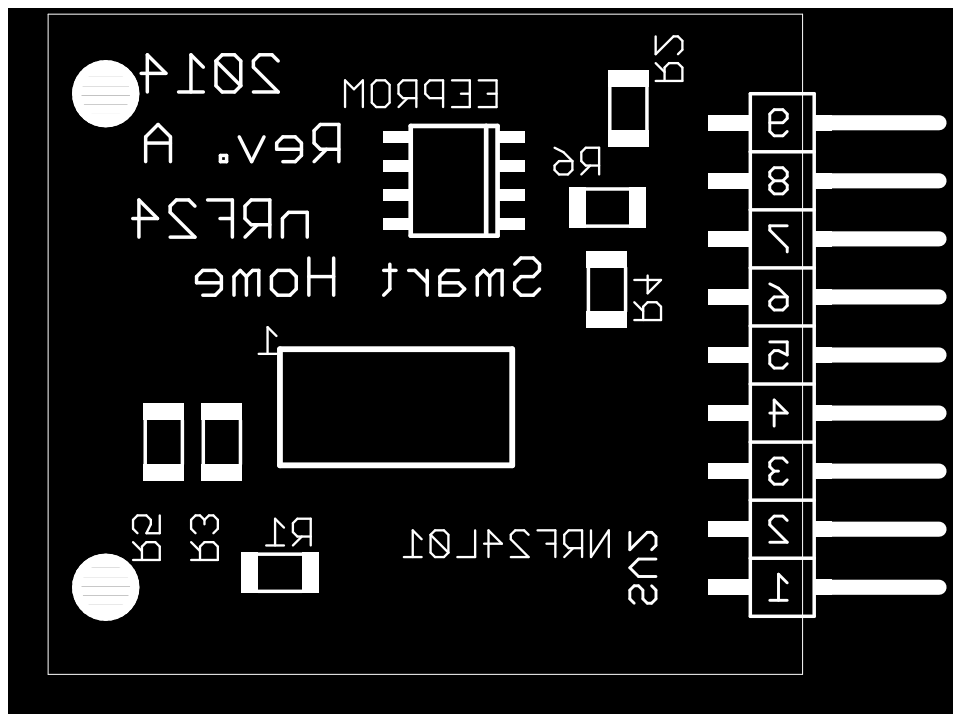
[picture p119: page 1]
