AlistairCheeseman/SmartHome-Project/Hardware/Connections/NRF24L01_PCB-SolderResist.pdf

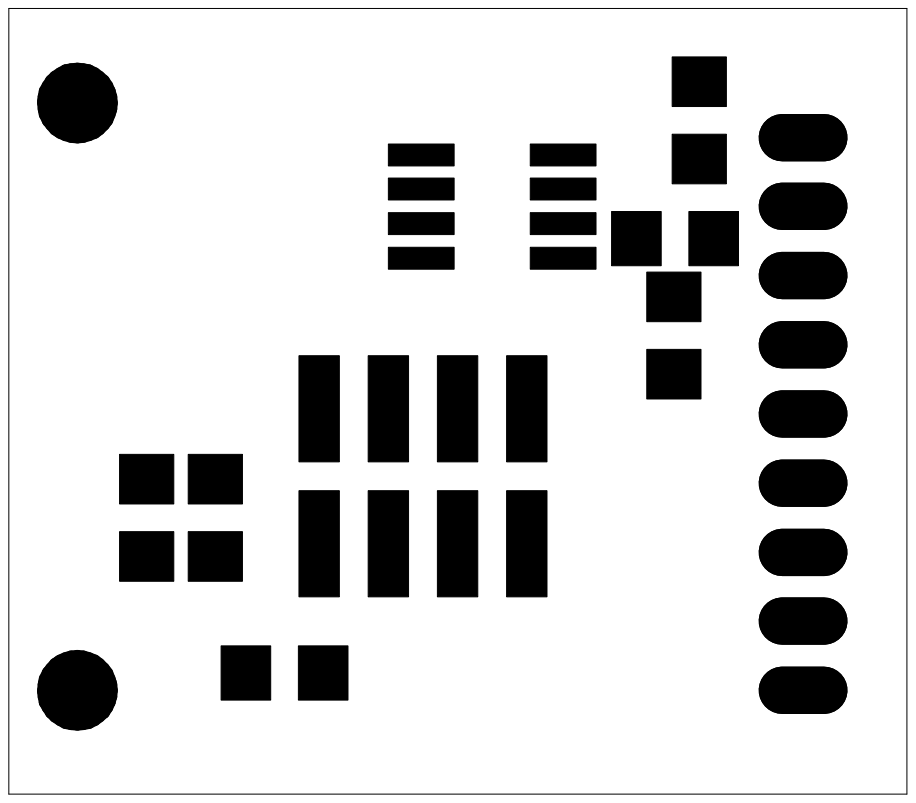
[picture p120: page 1]
