AlistairCheeseman/SmartHome-Project/Hardware/Connections/NRF24L01_PCB.pdf

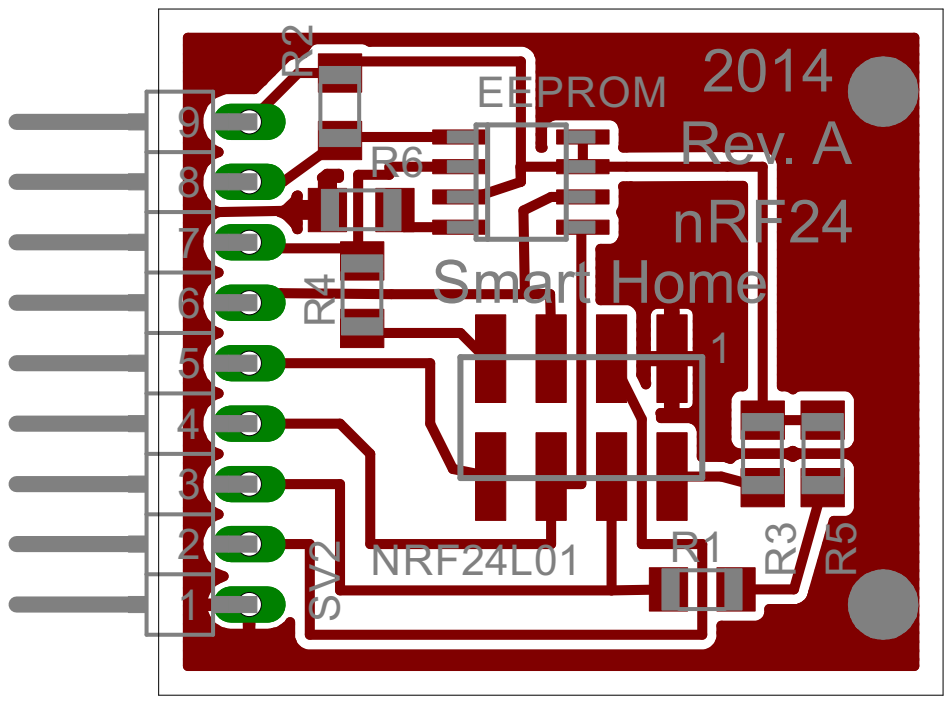
[picture p121: page 1]
