AlistairCheeseman/SmartHome-Project/Hardware/Connections/Programmer-Etch.pdf

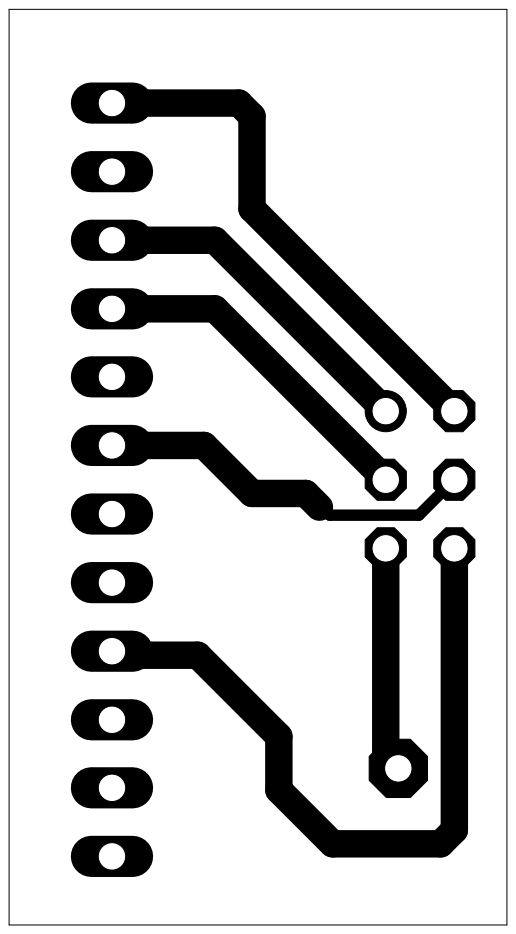
[picture p122: page 1]
