AlistairCheeseman/SmartHome-Project/Hardware/BeagleboneCape/BeagleboneCape-V2-Etch.pdf

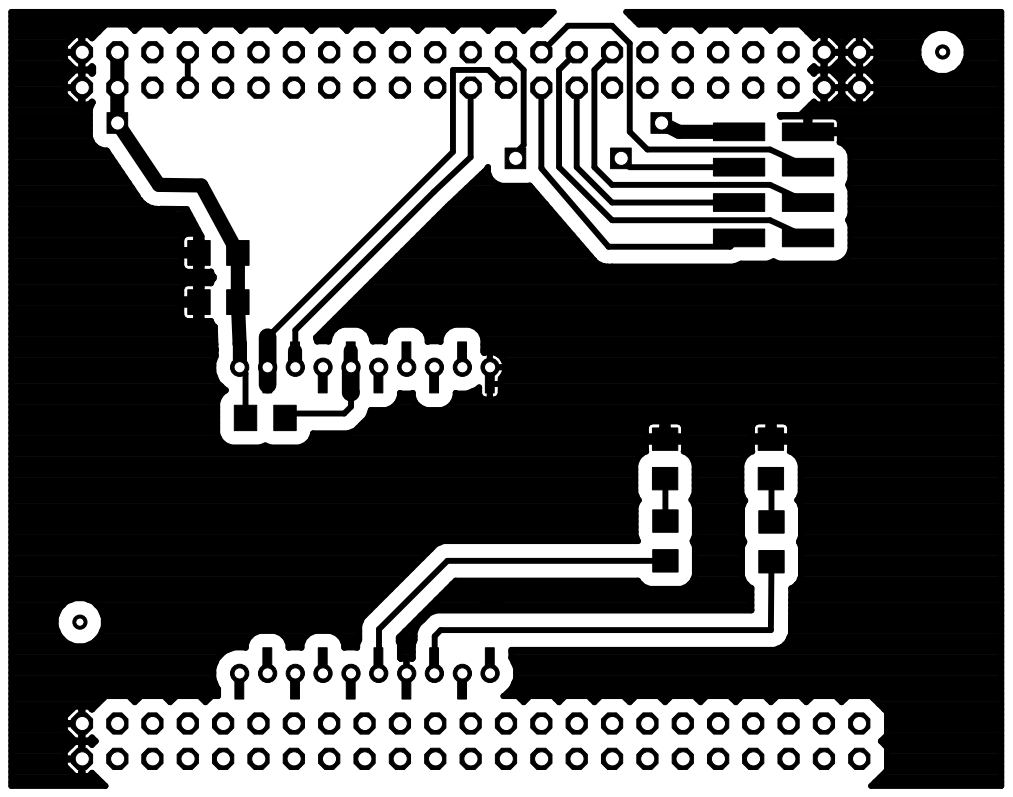
[picture p123: page 1]
