AlistairCheeseman/SmartHome-Project/Hardware/BeagleboneCape/BeagleboneCape-V2-Resist.pdf

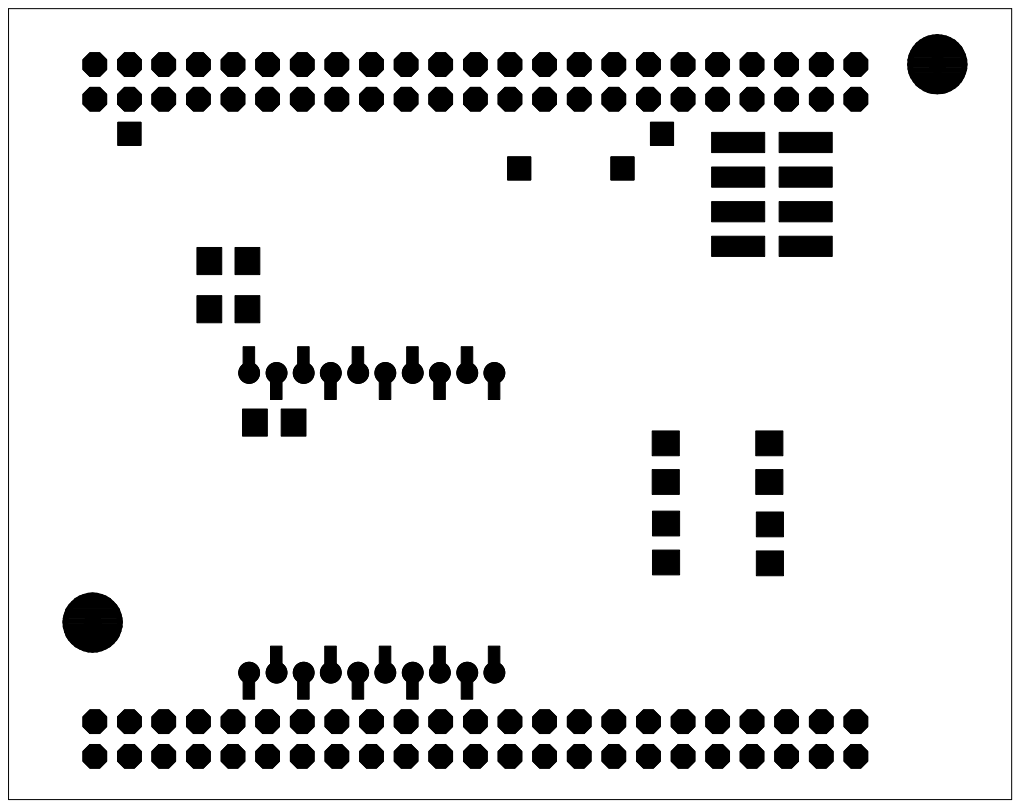
[picture p124: page 1]
