AlistairCheeseman/SmartHome-Project/Hardware/BeagleboneCape/BeagleboneCape-V2-Silk.pdf

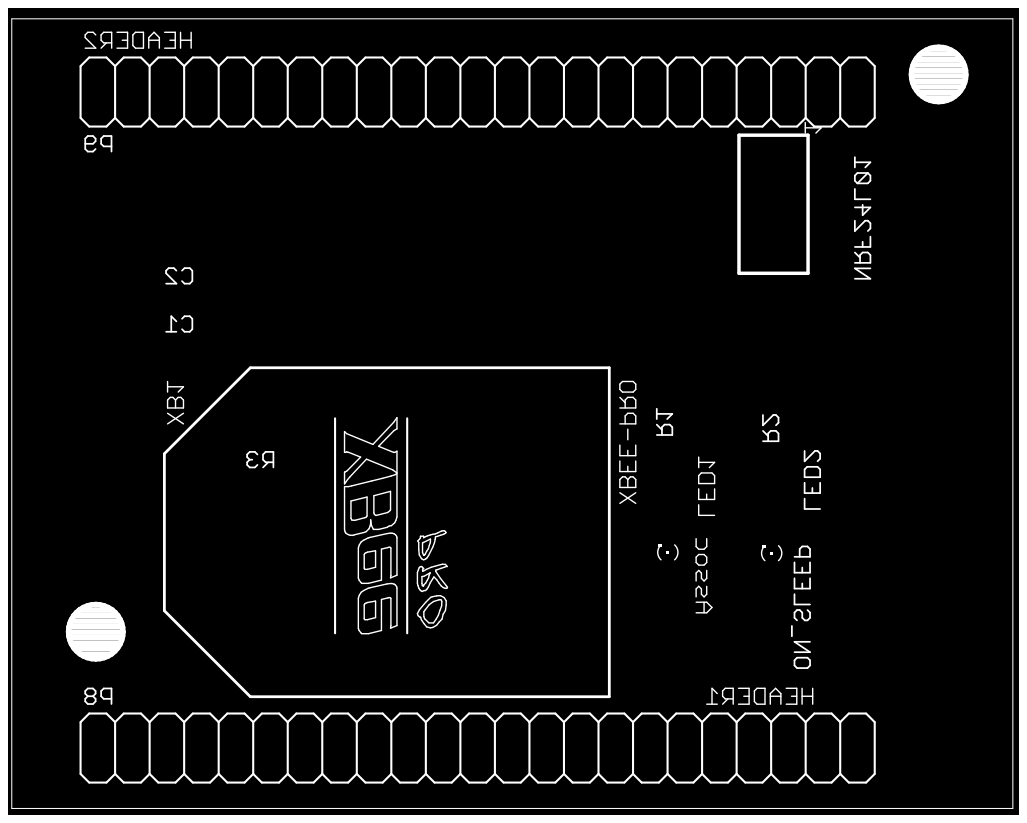
[picture p125: page 1]
