AlistairCheeseman/SmartHome-Project/Hardware/BeagleboneCape/BeagleboneCape-Silk-Mirror.pdf

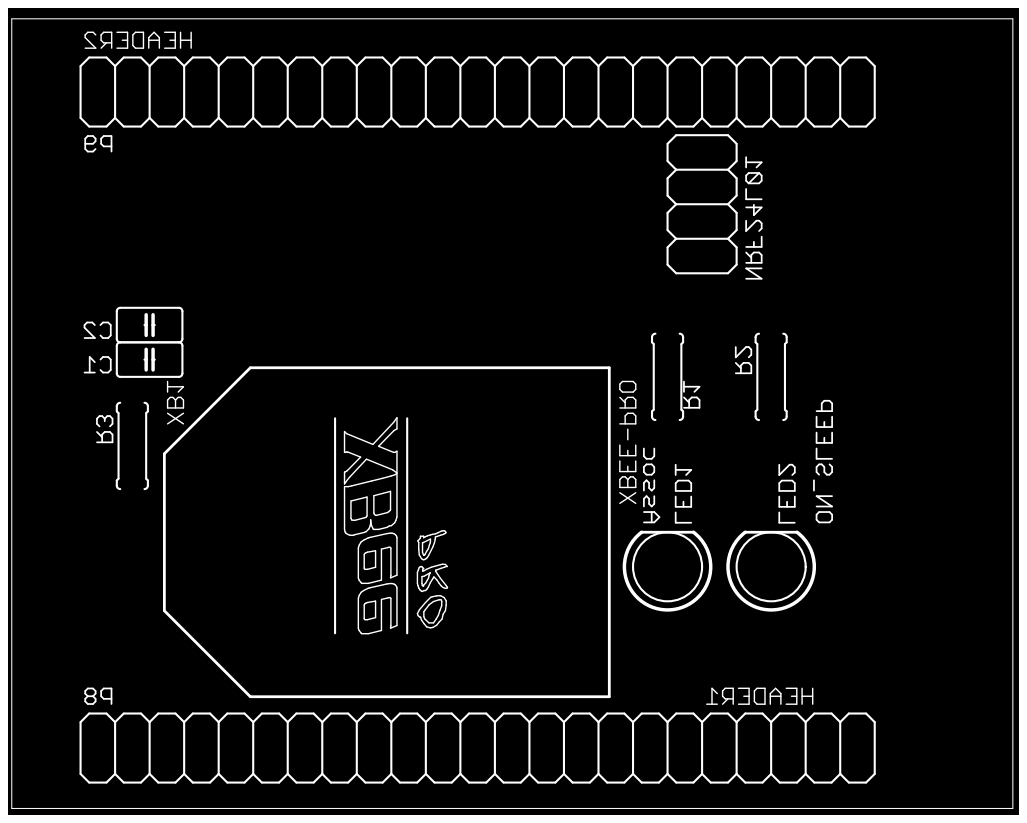
[picture p126: page 1]
