AlistairCheeseman/SmartHome-Project/Hardware/Connections/NRF24L01_SCH.pdf

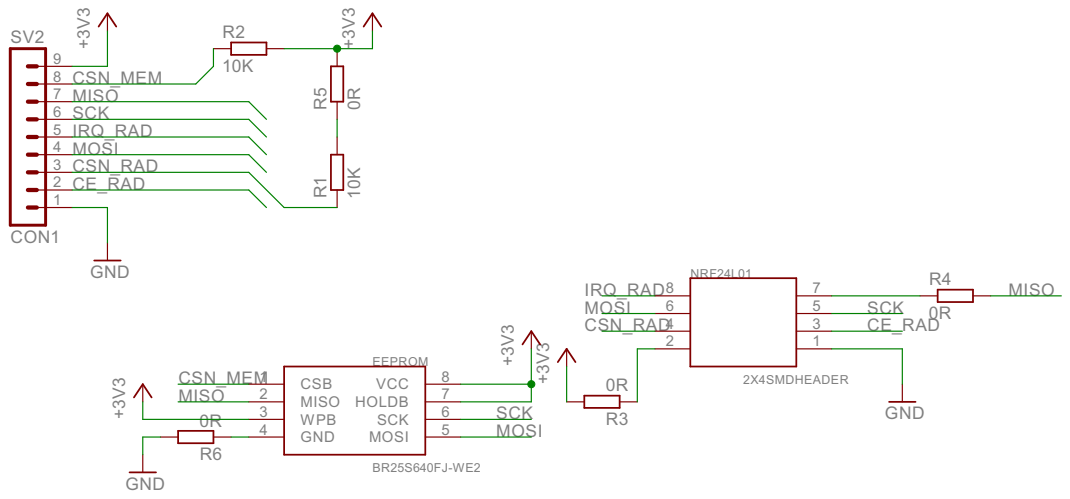
[picture p127: page 1]
