AlistairCheeseman/SmartHome-Project/Hardware/BeagleboneCape/BeagleboneCape-Schematic.pdf

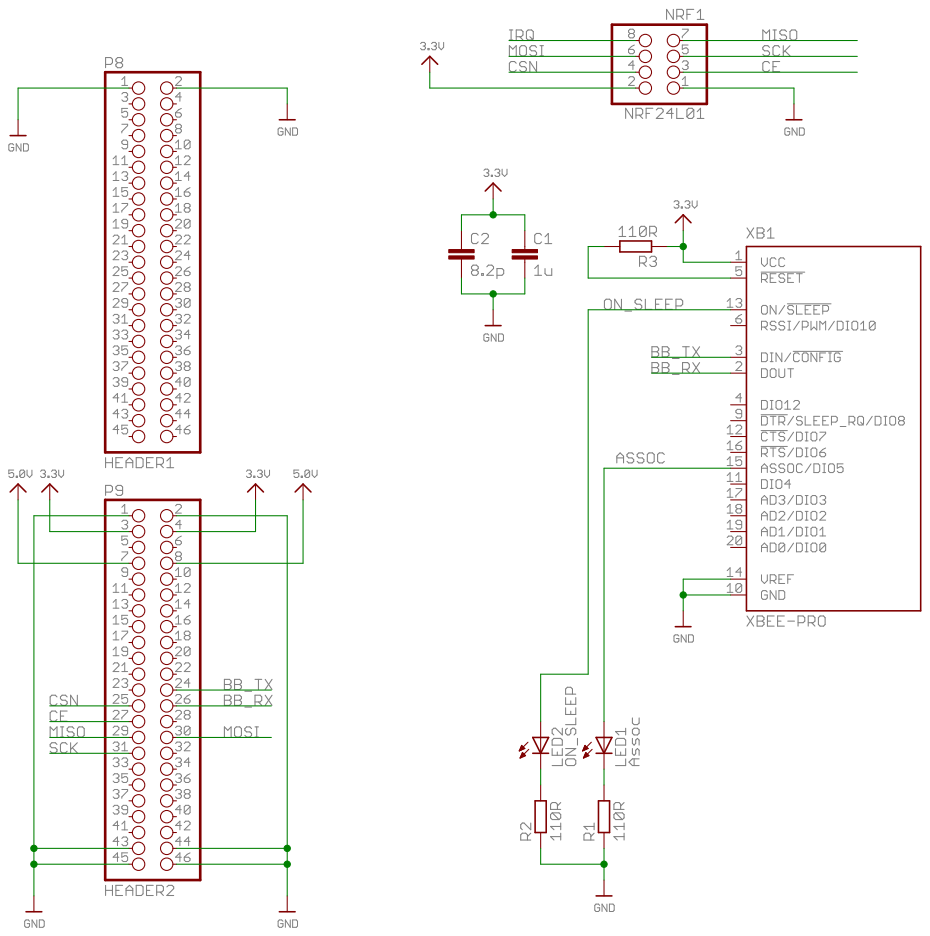
[picture p128: page 1]
