AlistairCheeseman/SmartHome-Project/Hardware/BeagleboneCape/BeagleboneCape-SolderResist.pdf

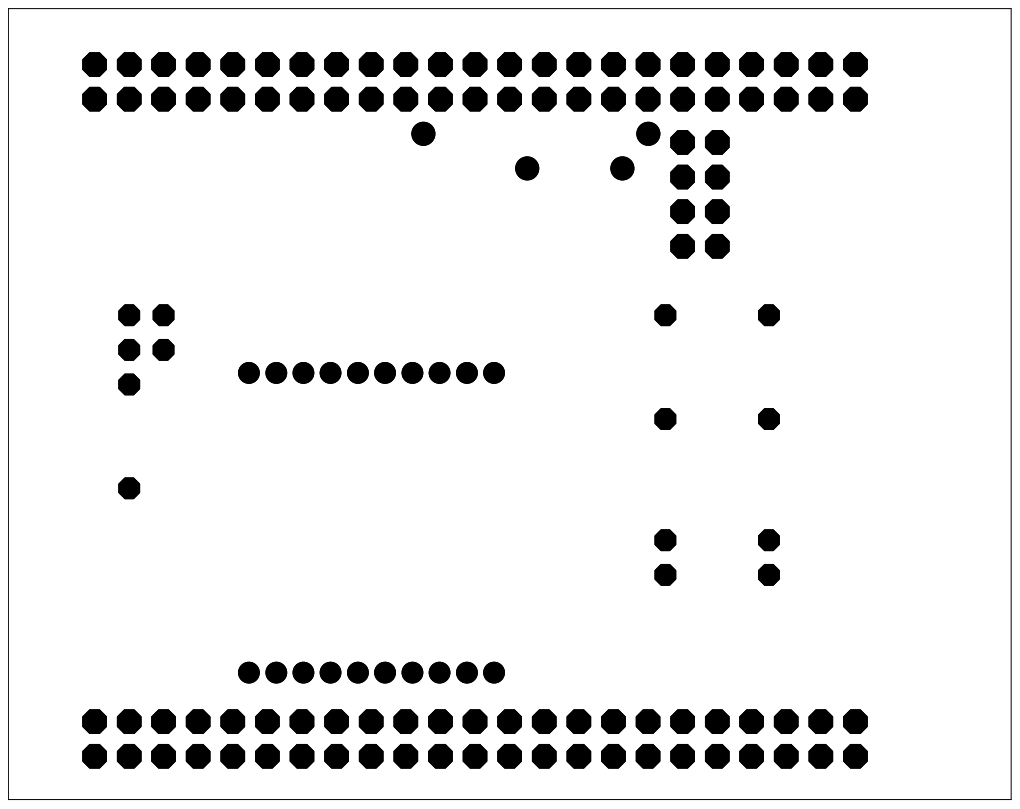
[picture p129: page 1]
