AlistairCheeseman/SmartHome-Project/Hardware/BeagleboneCape/BeagleboneCape-Etch.pdf

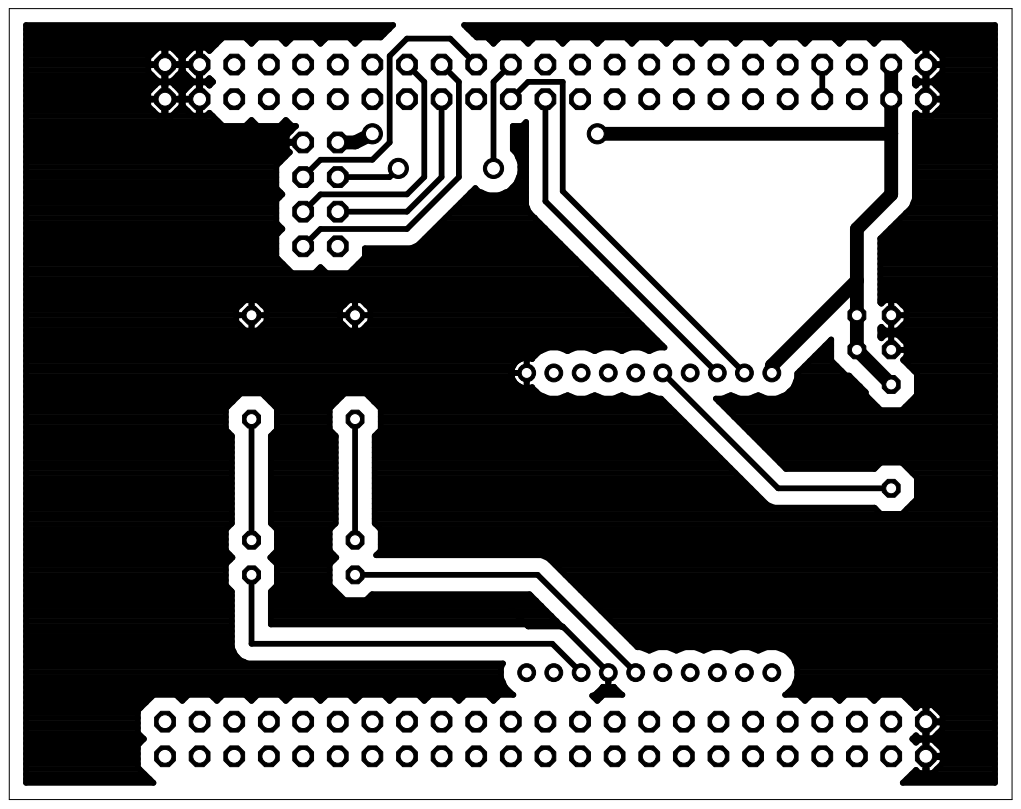
[picture p130: page 1]
