AlistairCheeseman/SmartHome-Project/Hardware/BeagleboneCape/BeagleboneCape-Silk.pdf

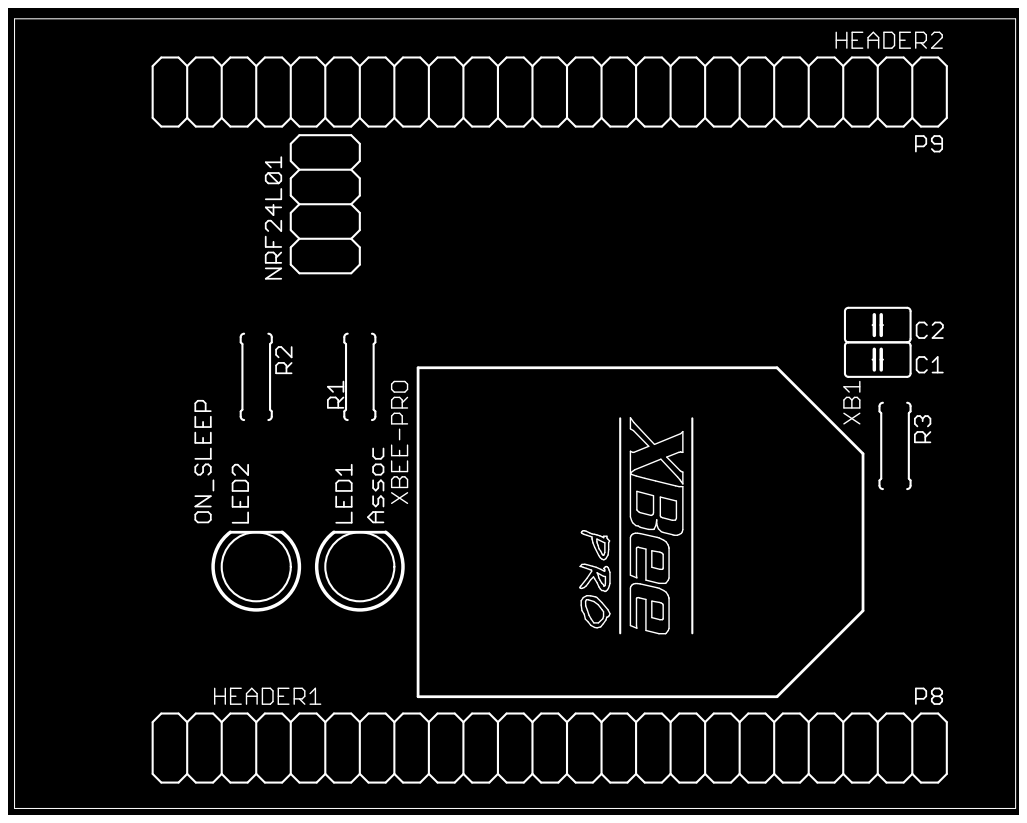
[picture p131: page 1]
