AlistairCheeseman/SmartHome-Project/Hardware/Connections/PoE.brd

## EAGLE design Hardware/Connections/PoE.brd (2015-02-03)

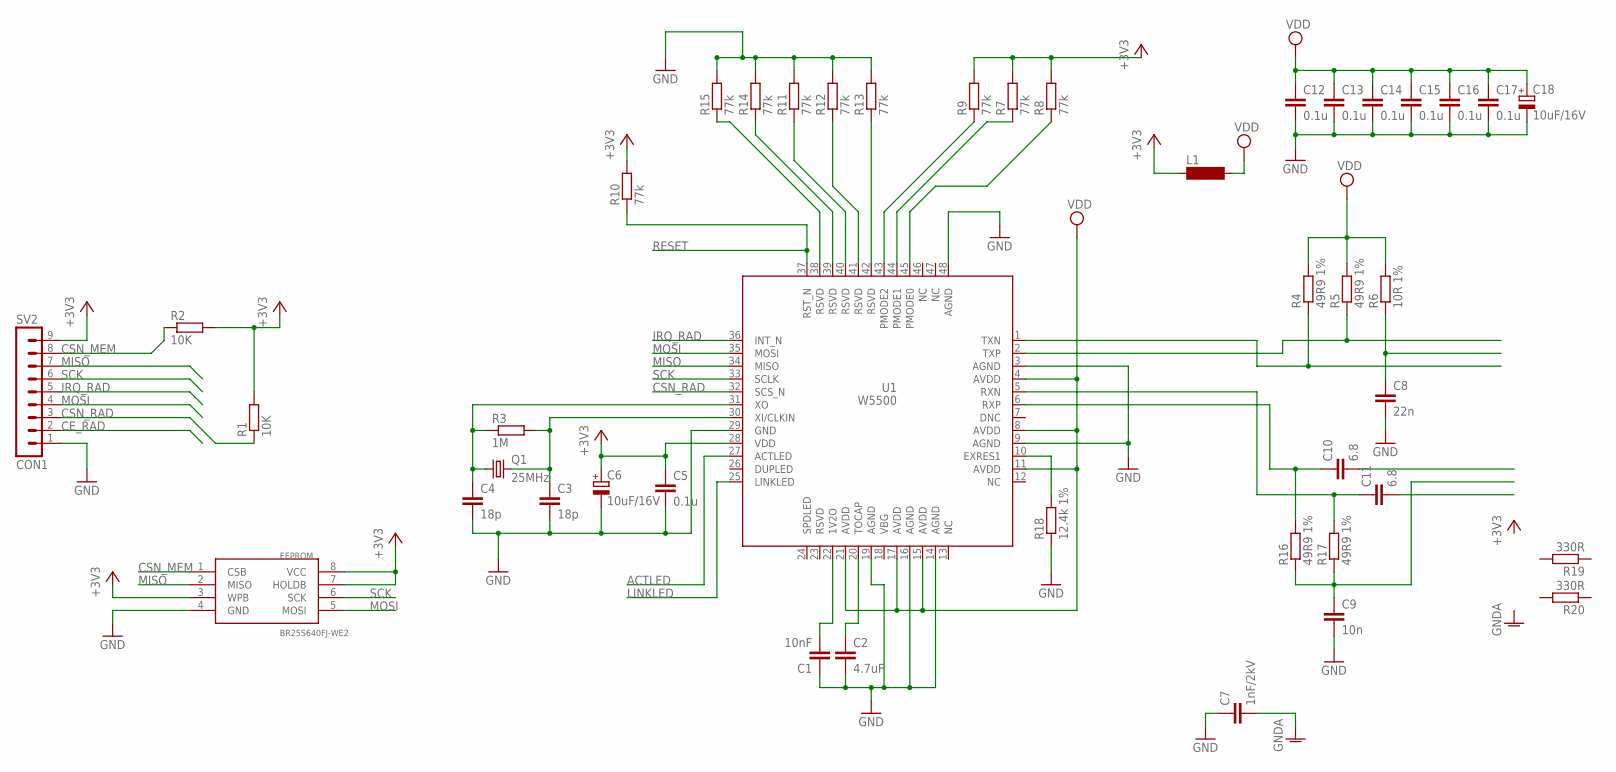
[picture p162: schematic PoE.sch]

Parts:
C1: 10nF; C1206
C2: 4.7uF; C1206
C3, C4: 18p; C1206
C5, C12, C13, C14, C15, C16, C17: 0.1u; C1206
C6: 10uF/16V; 153CLV-0505
C7: 1nF/2kV; C1206
C8: 22n; C1206
C9: 10n; C1206
C10, C11: 6.8; C1206
C18: 10uF/16V; 153CLV-0405
EEPROM: BR25S640FJ-WE2; SO8
L1: MS50
Q1: 25MHz; HC49UP
R1, R2: 10K; R1206
R3: 1M; R1206
R4, R5, R16, R17: 49R9 1%; R1206
R6: 10R 1%; R1206
R7, R8, R9, R10, R11, R12, R13, R14, R15: 77k; R1206
R18: 12.4k 1%; R1206
R19, R20: 330R; R1206
SV2: CON1; MA09-1W
U1: W5500

Connections:
+3V3: C5.1, C6.+, EEPROM.3 (WPB), EEPROM.7 (HOLDB), EEPROM.8 (VCC), L1.1, R1.2, R2.2, R7.2, R8.2, R9.2, R10.2, SV2.9, U1.28 (VDD)
ACTLED: U1.27 (ACTLED)
CE_RAD: SV2.2
CSN_MEM: EEPROM.1 (CSB), R2.1, SV2.8
CSN_RAD: R1.1, SV2.3, U1.32 (SCS_N)
GND: C1.1, C2.2, C3.2, C4.2, C5.2, C6.-, C7.1, C8.2, C9.2, C12.2, C13.2, C14.2, C15.2, C16.2, C17.2, C18.-, EEPROM.4 (GND), R11.2, R12.2, R13.2, R14.2, R15.2, R18.1, SV2.1, U1.3 (AGND), U1.9 (AGND), U1.14 (AGND), U1.16 (AGND), U1.19 (AGND), U1.29 (GND), U1.48 (AGND)
GNDA: C7.2
IRQ_RAD: SV2.5, U1.36 (INT_N)
LINKLED: U1.25 (LINKLED)
MISO: EEPROM.2 (MISO), SV2.7, U1.34 (MISO)
MOSI: EEPROM.5 (MOSI), SV2.4, U1.35 (MOSI)
unnamed: R9.1, U1.43 (PMODE2)
unnamed: C1.2, U1.22 (1V2O)
unnamed: C2.1, U1.20 (TOCAP)
unnamed: C4.1, Q1.1, R3.1, U1.31 (XO)
unnamed: C3.1, Q1.2, R3.2, U1.30 (XI/CLKIN)
unnamed: R7.1, U1.44 (PMODE1)
unnamed: C11.1, R17.2, U1.5 (RXN)
unnamed: R8.1, U1.45 (PMODE0)
unnamed: R15.1, U1.38 (RSVD)
unnamed: R14.1, U1.39 (RSVD)
unnamed: R11.1, U1.40 (RSVD)
unnamed: R12.1, U1.41 (RSVD)
unnamed: R13.1, U1.42 (RSVD)
unnamed: R5.1, U1.2 (TXP)
unnamed: C8.1, R6.1
unnamed: R4.1, U1.1 (TXN)
unnamed: C10.1, R16.2, U1.6 (RXP)
unnamed: C9.1, R16.1, R17.1
unnamed: R18.2, U1.10 (EXRES1)
RESET: R10.1, U1.37 (RST_N)
SCK: EEPROM.6 (SCK), SV2.6, U1.33 (SCLK)
VDD: C12.1, C13.1, C14.1, C15.1, C16.1, C17.1, C18.+, L1.2, R4.2, R5.2, R6.2, U1.4 (AVDD), U1.8 (AVDD), U1.11 (AVDD), U1.15 (AVDD), U1.17 (AVDD), U1.21 (AVDD)

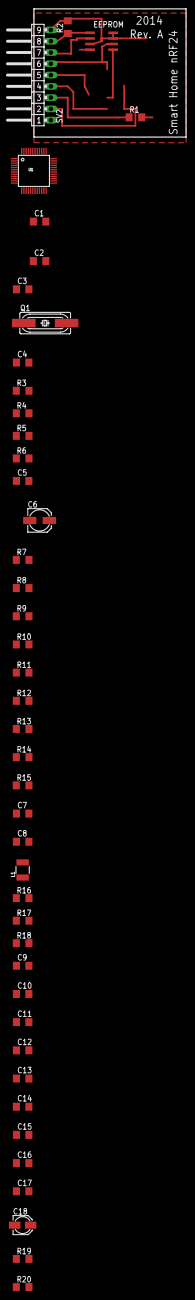
[picture p163: board PoE.brd from above]

Board: 2 copper layers, 34.3 x 28.9 mm, 43 parts (0 on the bottom side), 29 nets.
