AlistairCheeseman/SmartHome-Project/Hardware/Connections/XBEE.brd

## EAGLE design Hardware/Connections/XBEE.brd (2015-02-01)

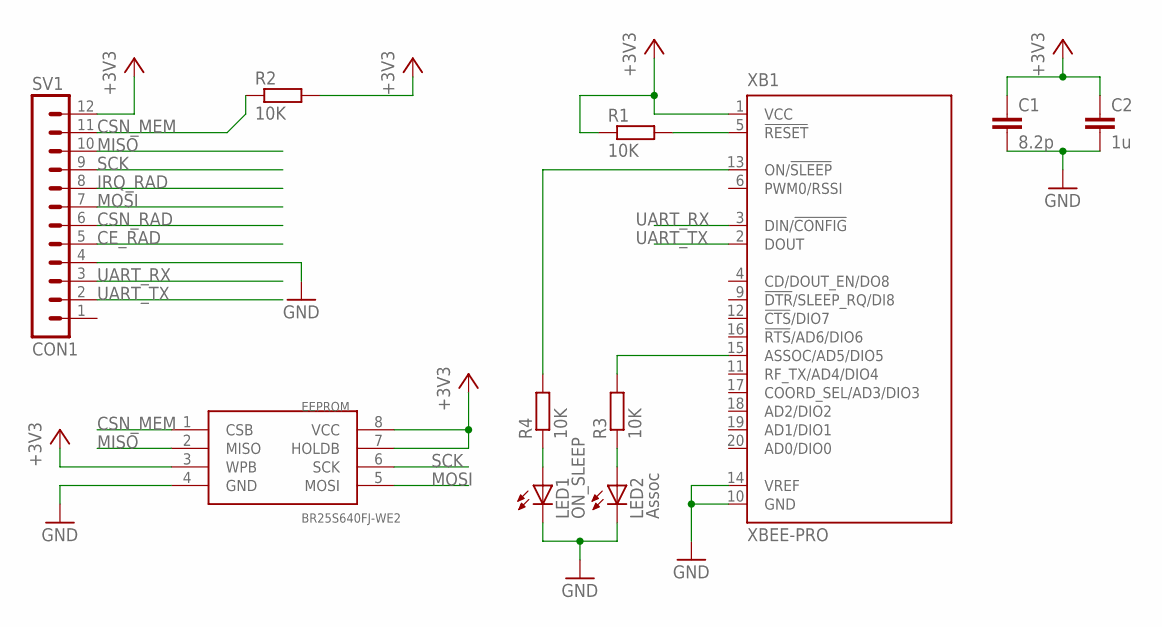
[picture p164: schematic XBEE.sch]

Parts:
C1: 8.2p; C1206
C2: 1u; C1206
EEPROM: BR25S640FJ-WE2; SO8
LED1: ON_SLEEP; 1206
LED2: Assoc; 1206
R1, R2, R3, R4: 10K; R1206
SV1: CON1; MA12-1W
XB1: XBEE-PRO

Connections:
+3V3: C1.1, C2.1, EEPROM.3 (WPB), EEPROM.7 (HOLDB), EEPROM.8 (VCC), R1.1, R2.2, SV1.12, XB1.1 (VCC)
CE_RAD: SV1.5
CSN_MEM: EEPROM.1 (CSB), R2.1, SV1.11
CSN_RAD: SV1.6
GND: C1.2, C2.2, EEPROM.4 (GND), LED1.C, LED2.C, SV1.4, XB1.10 (GND), XB1.14 (VREF)
IRQ_RAD: SV1.8
MISO: EEPROM.2 (MISO), SV1.10
MOSI: EEPROM.5 (MOSI), SV1.7
unnamed: R1.2, XB1.5 (!RESET)
unnamed: R4.2, XB1.13 (ON/!SLEEP)
unnamed: R3.2, XB1.15 (ASSOC/AD5/DIO5)
unnamed: LED1.A, R4.1
unnamed: LED2.A, R3.1
SCK: EEPROM.6 (SCK), SV1.9
UART_RX: SV1.3, XB1.3 (DIN/!CONFIG)
UART_TX: SV1.2, XB1.2 (DOUT)

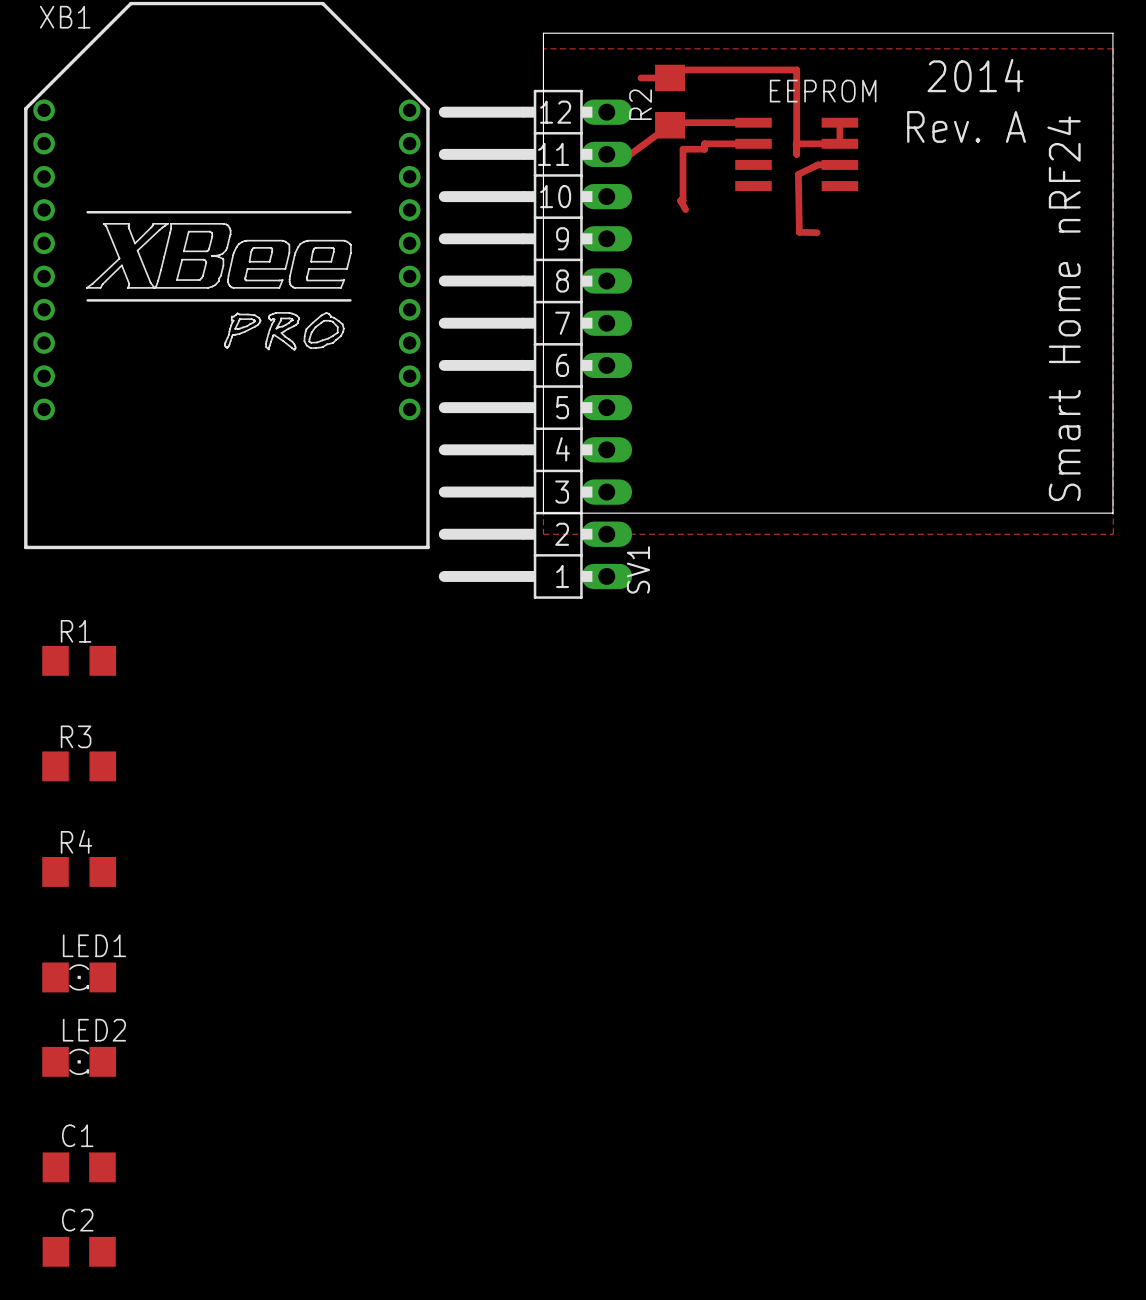
[picture p165: board XBEE.brd from above]

Board: 2 copper layers, 34.3 x 28.9 mm, 11 parts (0 on the bottom side), 13 nets.
