AlistairCheeseman/SmartHome-Project/Hardware/Connections/PLC.brd

## EAGLE design Hardware/Connections/PLC.brd (2014-12-04)

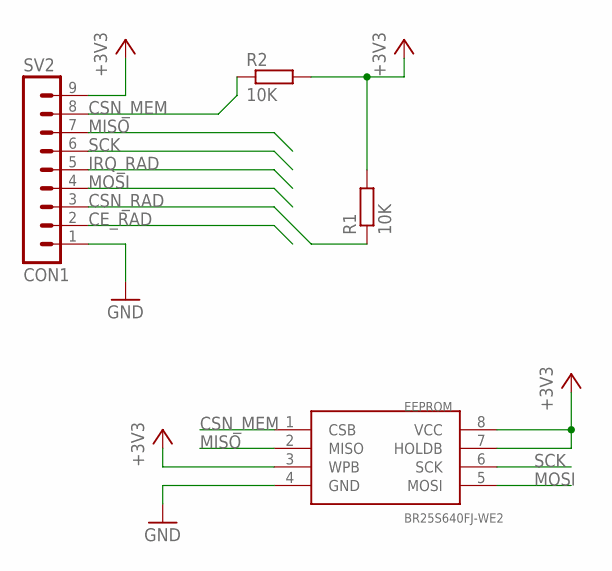
[picture p166: schematic PLC.sch]

Parts:
EEPROM: BR25S640FJ-WE2; SO8
R1, R2: 10K; R1206
SV2: CON1; MA09-1W

Connections:
+3V3: EEPROM.3 (WPB), EEPROM.7 (HOLDB), EEPROM.8 (VCC), R1.2, R2.2, SV2.9
CE_RAD: SV2.2
CSN_MEM: EEPROM.1 (CSB), R2.1, SV2.8
CSN_RAD: R1.1, SV2.3
GND: EEPROM.4 (GND), SV2.1
IRQ_RAD: SV2.5
MISO: EEPROM.2 (MISO), SV2.7
MOSI: EEPROM.5 (MOSI), SV2.4
SCK: EEPROM.6 (SCK), SV2.6

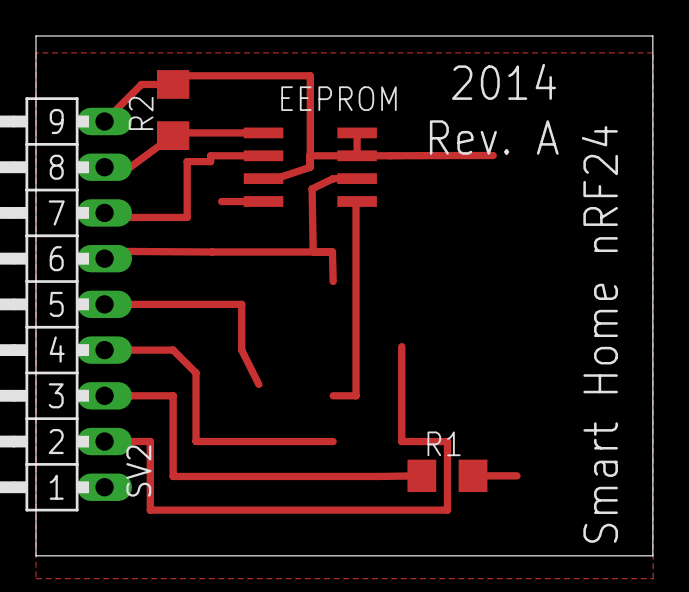
[picture p167: board PLC.brd from above]

Board: 2 copper layers, 34.3 x 28.9 mm, 4 parts (0 on the bottom side), 7 nets.
