AlistairCheeseman/SmartHome-Project/Software/Apps/LogicLayer/SQL.h

/* 
 * File:   SQL.h
 * Author: alistair
 *
 * Created on 02 February 2015, 14:43
 * file to hold SQL Class to handle the DAL Layer of the application
 */

#ifndef SQL_H
#define	SQL_H

#include <sqlite3.h>
#include <stdio.h>
#include "automationRule.h"
#include "log.h"
// handle all the sql data, rather than using straight sql commands, it is passed through this layer class to abstract the sql functions.
class SQL {
public:
    SQL(const char *filename);
    virtual ~SQL();
    void logVal(char *topic, char *payload);
    void execute(char *statement);
    void writePower(float pf, float pow);
    int callback(int argc, char **argv, char **azColName);
    void get_data();
    // get the topic that the SR Request must be published to for the Dev Request.
    char* getSRDEVTopic(char* mac, char* id);
    // get the topic that the SR Request must be published to for the MAP Request.
    char* getSRMAPTopic(char* room, char* device, char* setting);
    //get the Mapping layer path from the mac and Id.
    char* getMAPDevtopic(char* mac, char* id);
    //Set the current value into the db.
    void setSMAPVal(char* room, char* device, char* setting, char* MAPVal);
    //check if there is a matching automation rule
    bool checkRules(char* id);
    //actually get the rules
    int getRules(char* id, automationRule *(&AR));
    // from the mac and control ID get the Sensor Id
    char* getSensorId(char* mac, char* id);
private:
    void connectDB(const char *filename);
    sqlite3 *db;
    bool isdbopen;
    char* getCurrentMoment();

};

#endif	/* SQL_H */
